carletz/DOMIX-Open-Source-Modular-Home-Automation-System/Images/3D Total 3.png

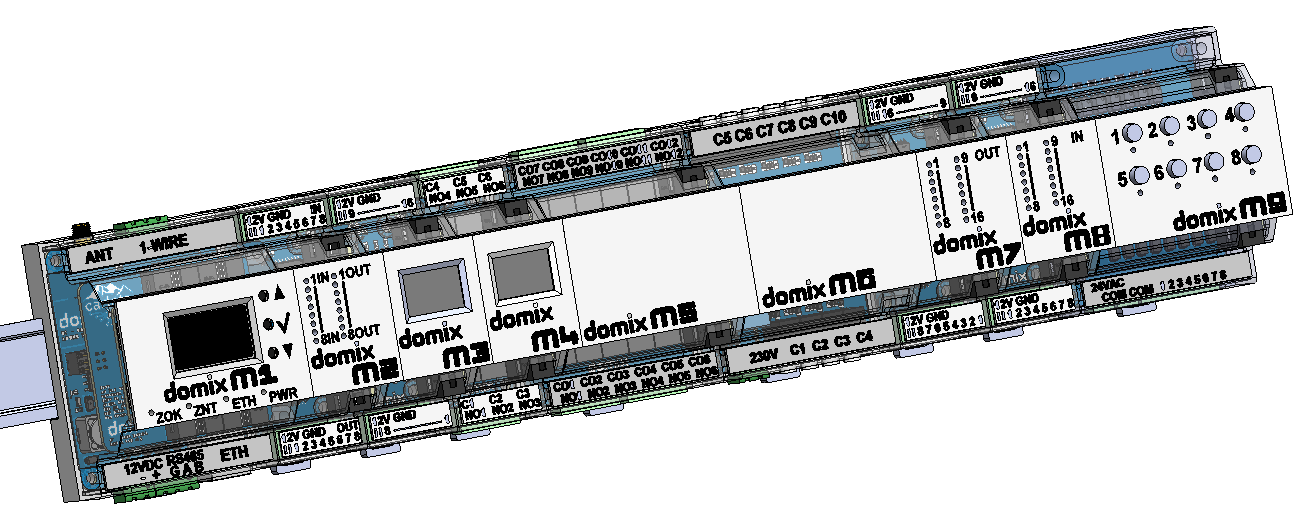
Images/3D Total 3.png
