carletz/DOMIX-Open-Source-Modular-Home-Automation-System/Images/8 module.png

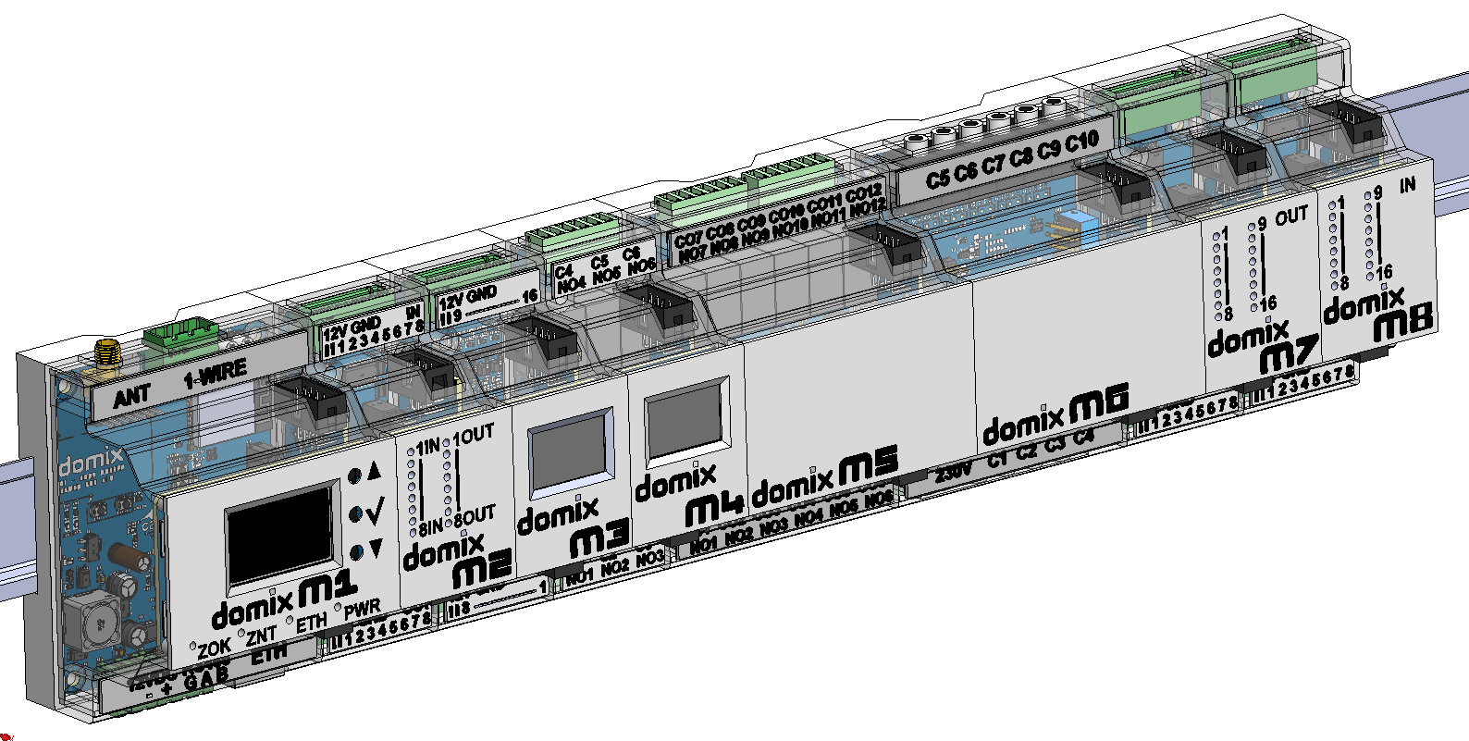
Images/8 module.png
