carletz/DOMIX-Open-Source-Modular-Home-Automation-System/Images/Board/domix total.png

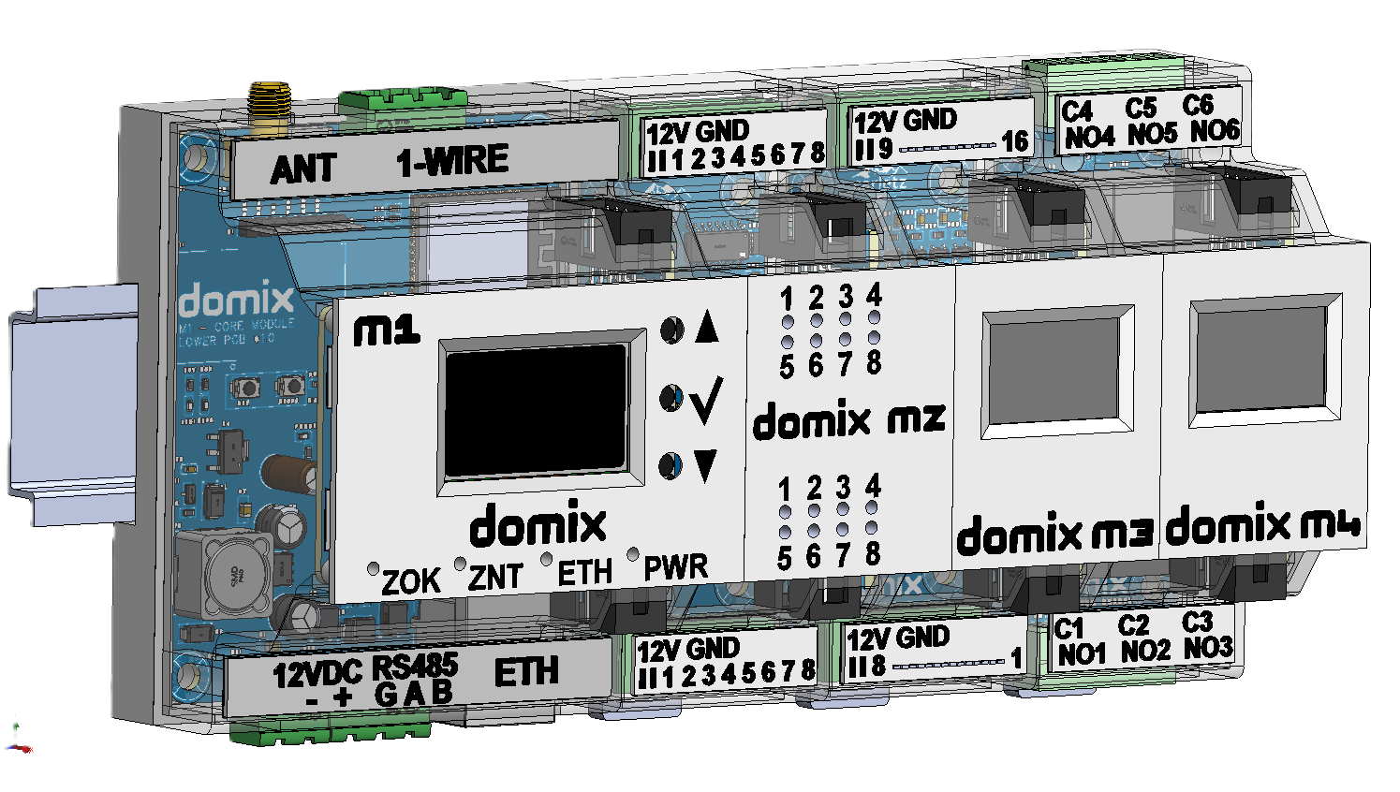
Images/Board/domix total.png
