carletz/DOMIX-Open-Source-Modular-Home-Automation-System/Images/Board/M1/M1 - 3D Board V0.1.png

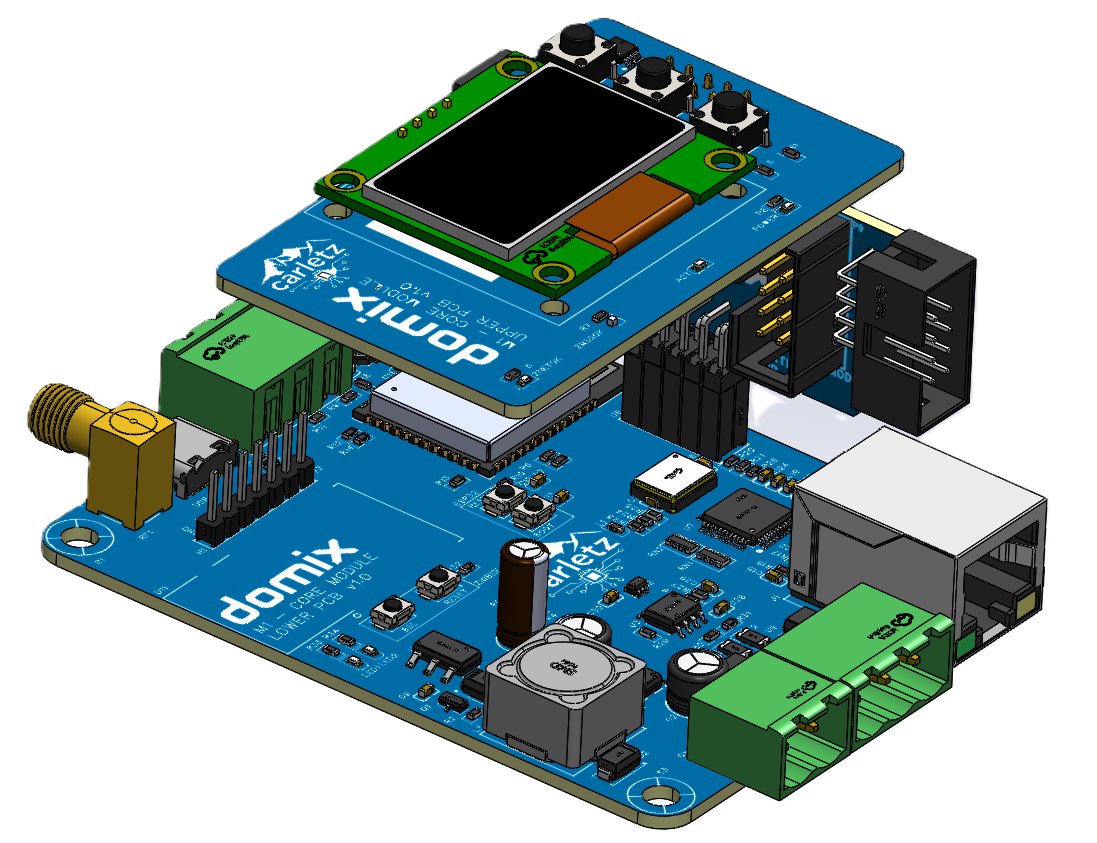
Images/Board/M1/M1 - 3D Board V0.1.png
