carletz/DOMIX-Open-Source-Modular-Home-Automation-System/Images/Board/M1/M1 - 3D Board V1.0.png

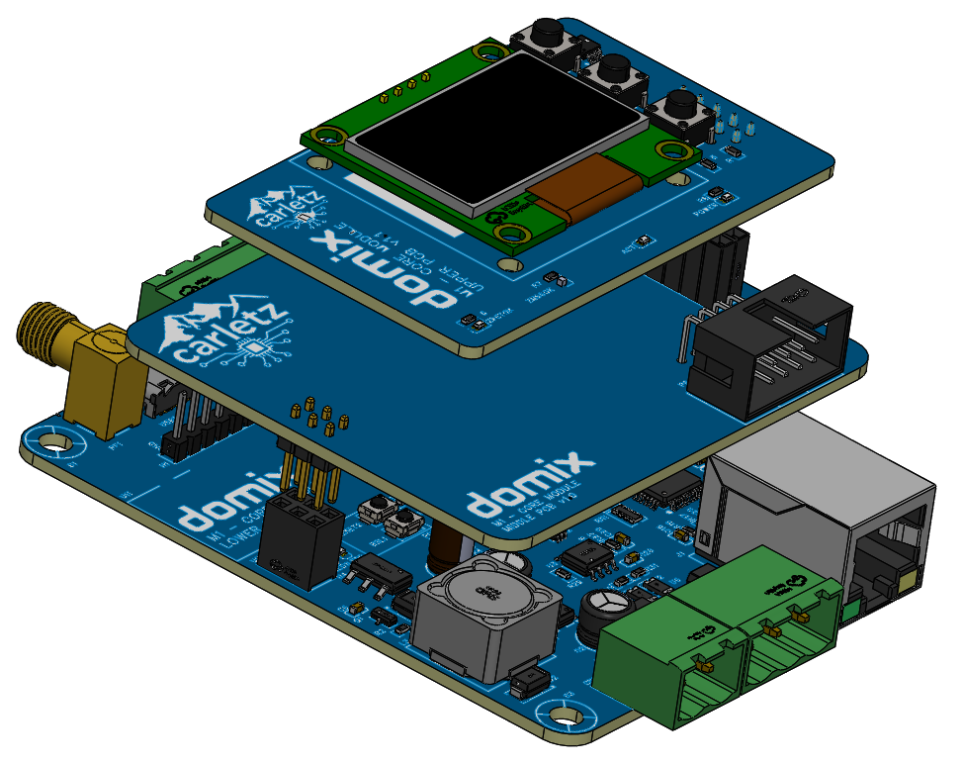
Images/Board/M1/M1 - 3D Board V1.0.png
