carletz/DOMIX-Open-Source-Modular-Home-Automation-System/Images/Board/M1/M1 - 3D Exploded.png

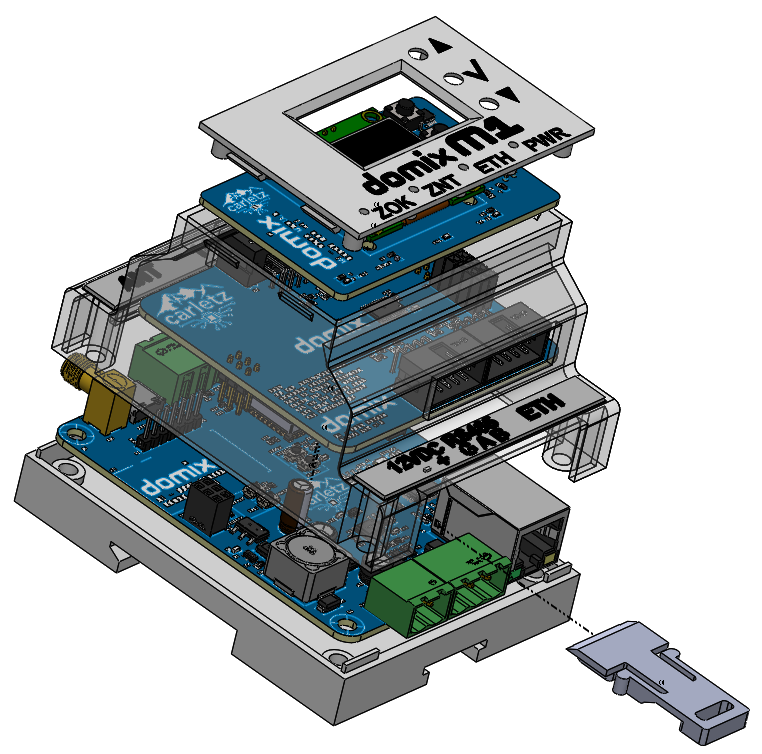
Images/Board/M1/M1 - 3D Exploded.png
