carletz/DOMIX-Open-Source-Modular-Home-Automation-System/Images/Board/M1/M1 - Lower.png

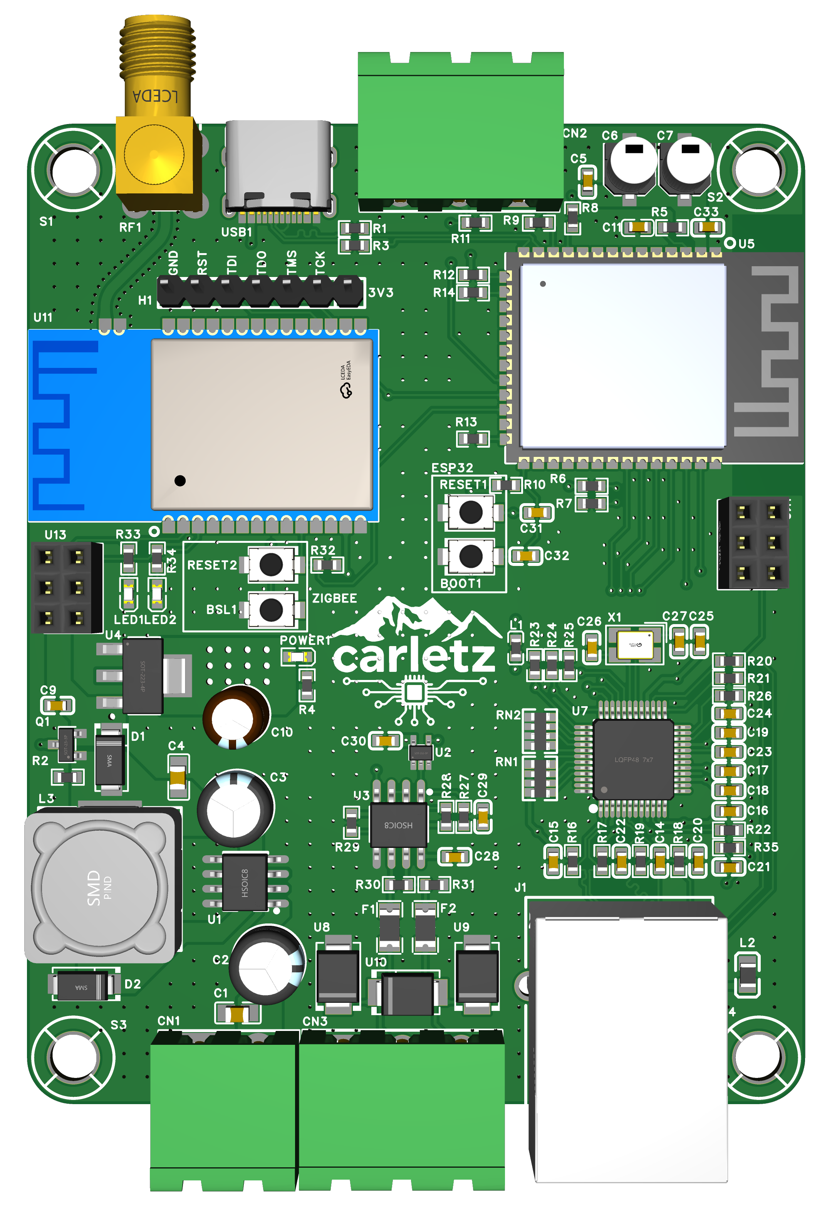
Images/Board/M1/M1 - Lower.png
