carletz/DOMIX-Open-Source-Modular-Home-Automation-System/Images/Board/M1/M1 - middle V1.0.png

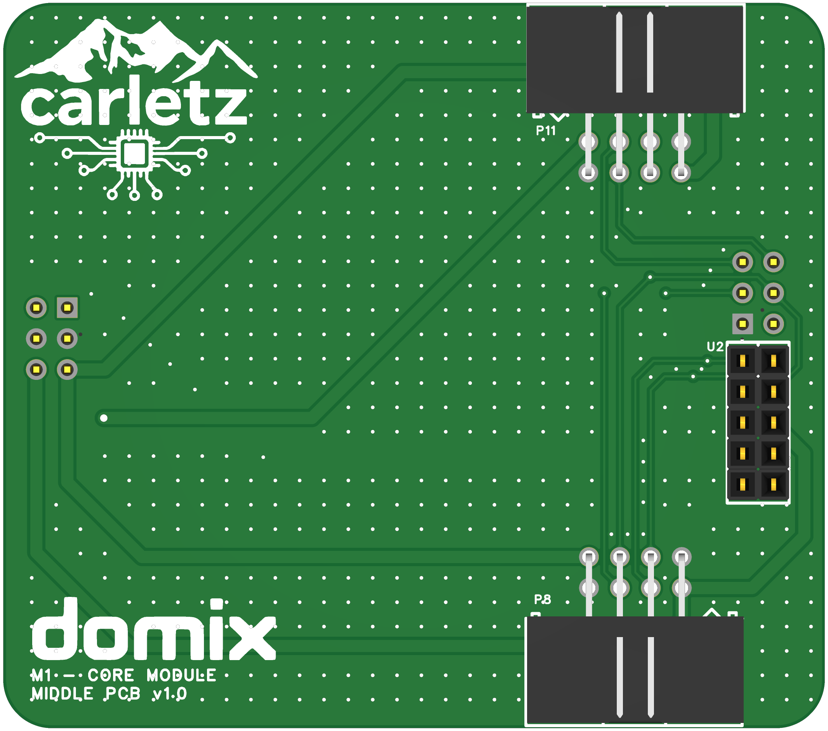
Images/Board/M1/M1 - middle V1.0.png
