carletz/DOMIX-Open-Source-Modular-Home-Automation-System/Images/Board/M1/M1 - Middle V1.1.png

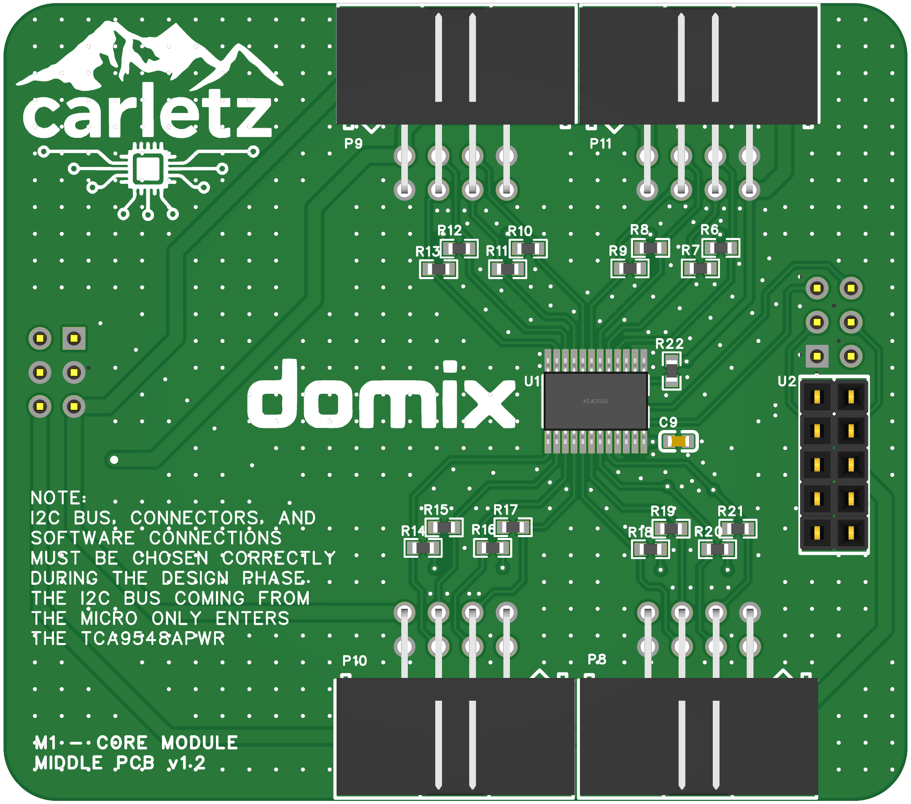
Images/Board/M1/M1 - Middle V1.1.png
