carletz/DOMIX-Open-Source-Modular-Home-Automation-System/Images/Board/M1/M1 - Upper.png

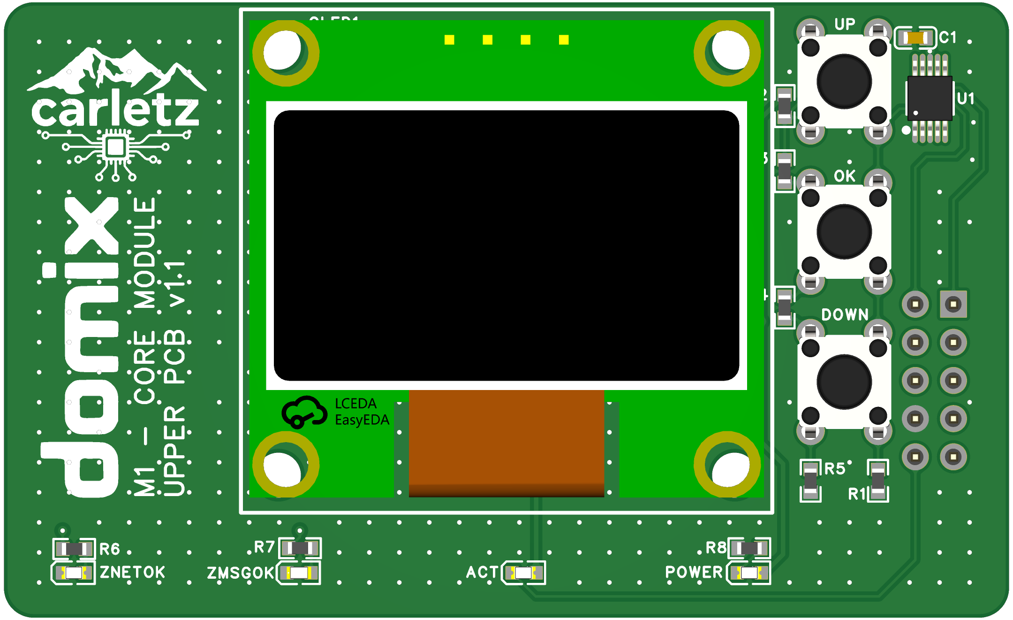
Images/Board/M1/M1 - Upper.png
