carletz/DOMIX-Open-Source-Modular-Home-Automation-System/Images/Board/M2/M2 - 3D Board.png

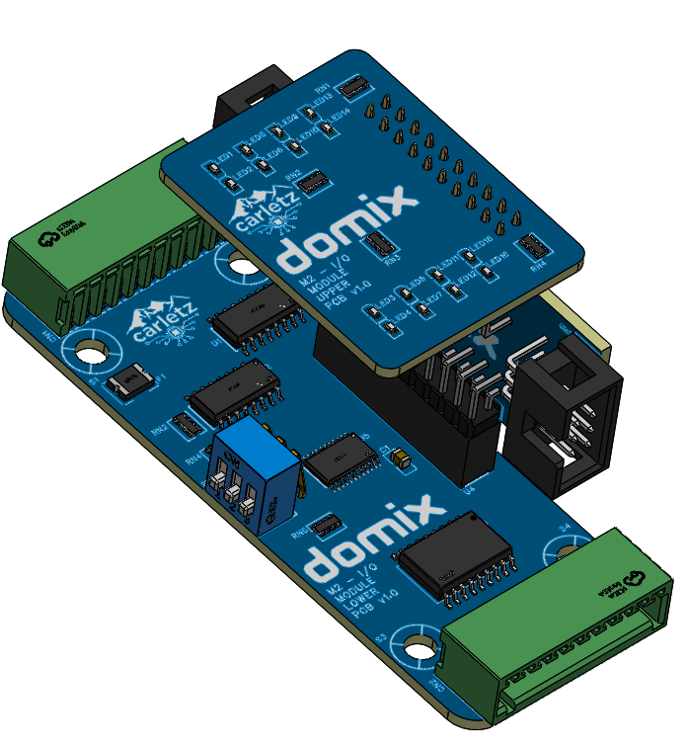
Images/Board/M2/M2 - 3D Board.png
