carletz/DOMIX-Open-Source-Modular-Home-Automation-System/Images/Board/M2/M2 - Lower.png

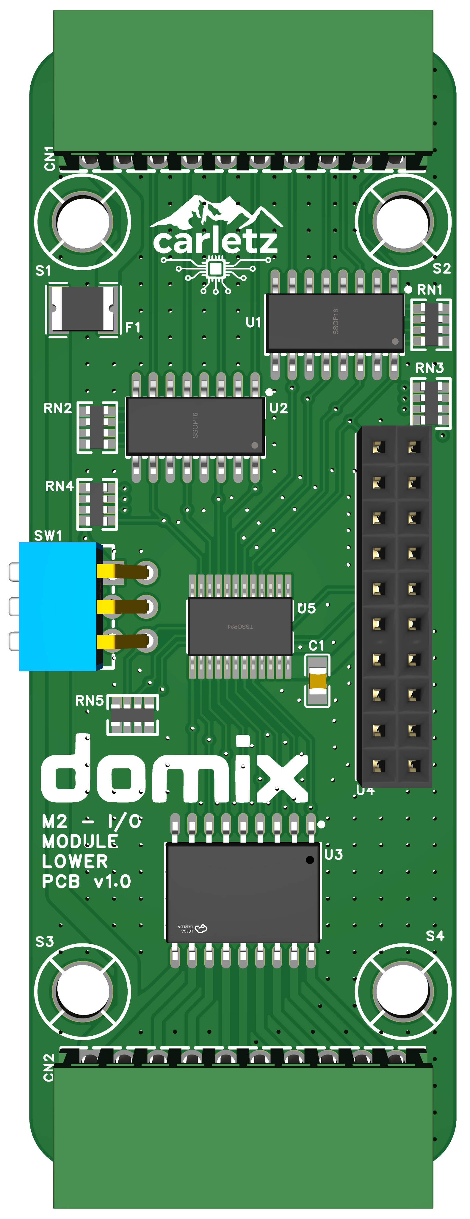
Images/Board/M2/M2 - Lower.png
