carletz/DOMIX-Open-Source-Modular-Home-Automation-System/Images/Board/M2/M2 - Pinout.png

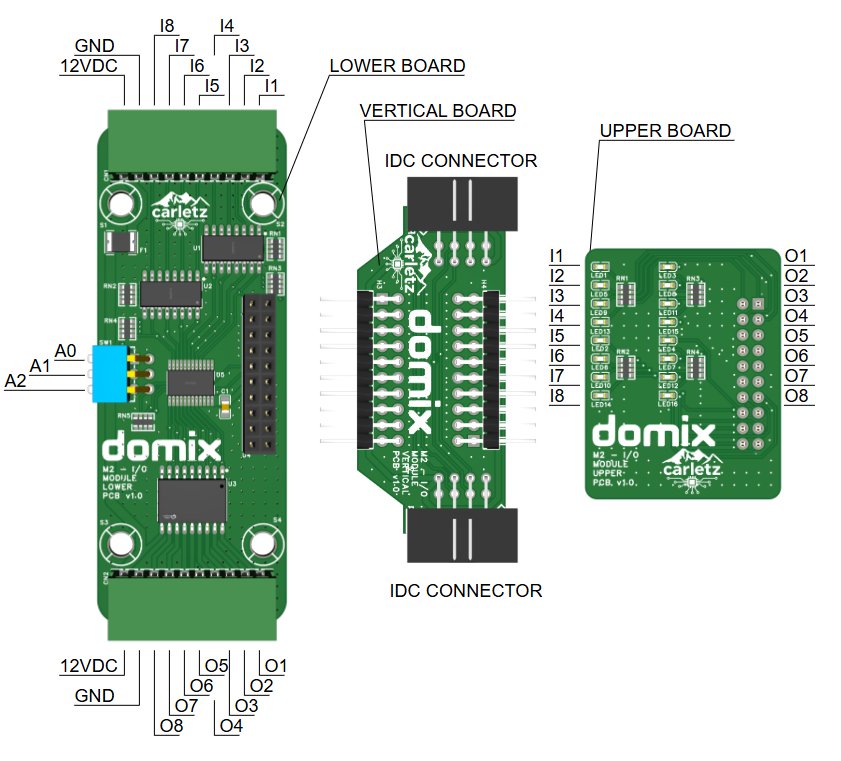
Images/Board/M2/M2 - Pinout.png
