carletz/DOMIX-Open-Source-Modular-Home-Automation-System/Images/Board/M3/M3 - 3D Board.png

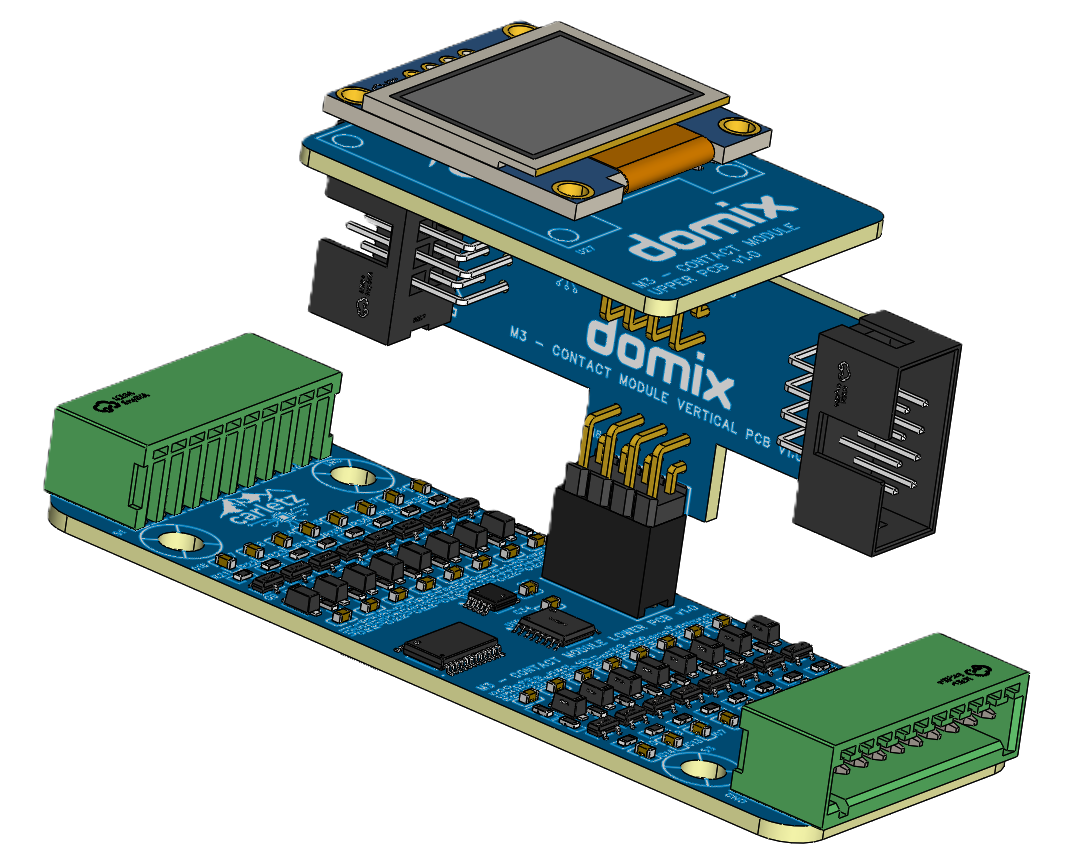
Images/Board/M3/M3 - 3D Board.png
