carletz/DOMIX-Open-Source-Modular-Home-Automation-System/Images/Board/M3/M3 - Lower.png

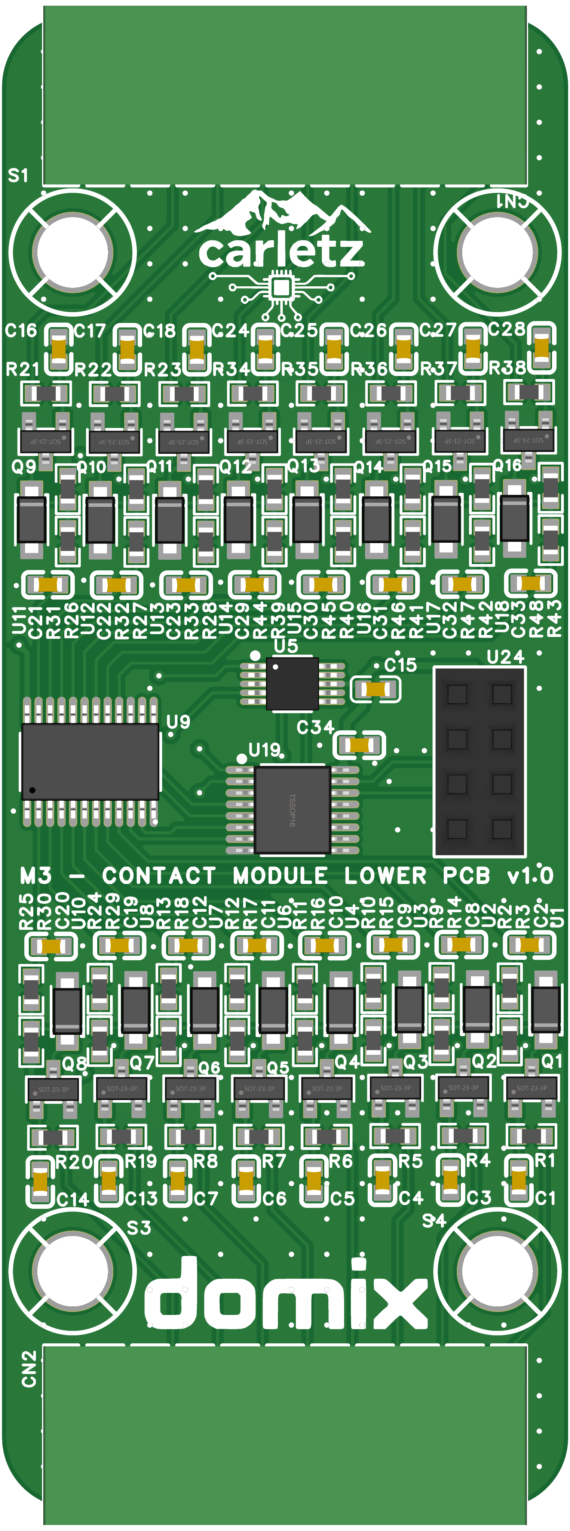
Images/Board/M3/M3 - Lower.png
