carletz/DOMIX-Open-Source-Modular-Home-Automation-System/Images/Board/M3/M3 - Upper.png

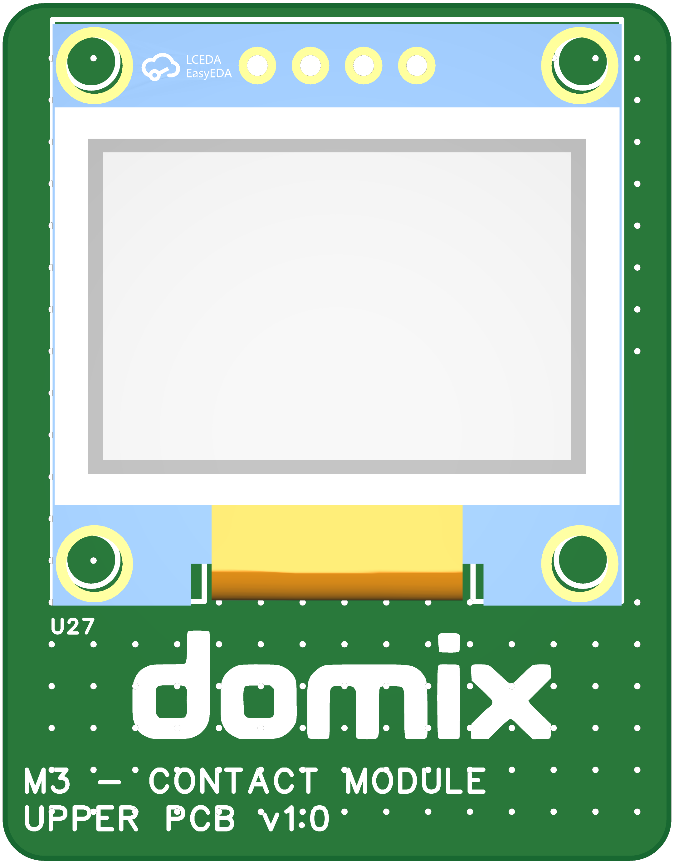
Images/Board/M3/M3 - Upper.png
