carletz/DOMIX-Open-Source-Modular-Home-Automation-System/Images/Board/M4/M4 - 3D Board.png

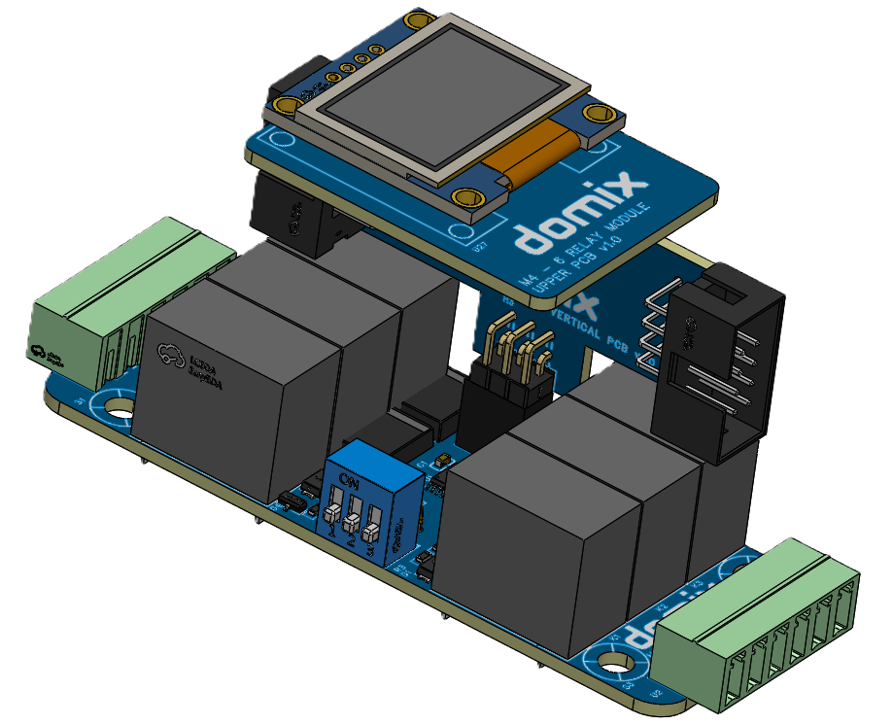
Images/Board/M4/M4 - 3D Board.png
