carletz/DOMIX-Open-Source-Modular-Home-Automation-System/Images/Board/M4/M4 - Pinout.png

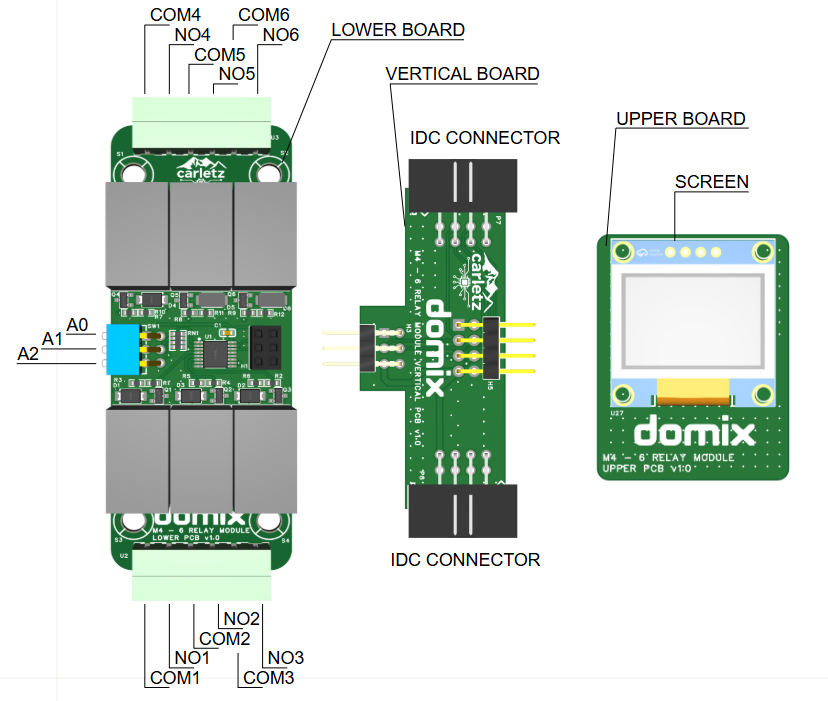
Images/Board/M4/M4 - Pinout.png
