carletz/DOMIX-Open-Source-Modular-Home-Automation-System/Images/Board/M5/M5 - Lower.png

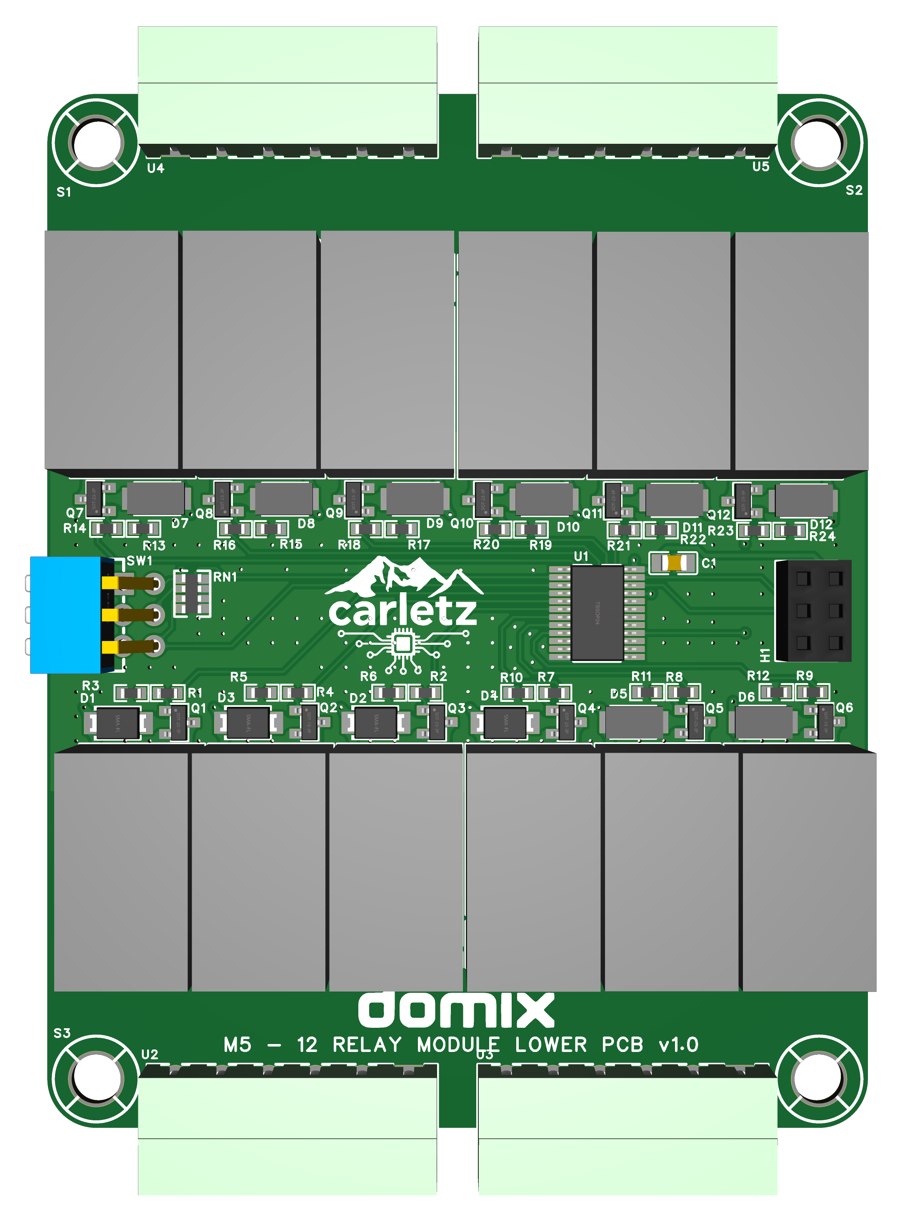
Images/Board/M5/M5 - Lower.png
