carletz/DOMIX-Open-Source-Modular-Home-Automation-System/Images/Board/M5/M5 - Pinout.png

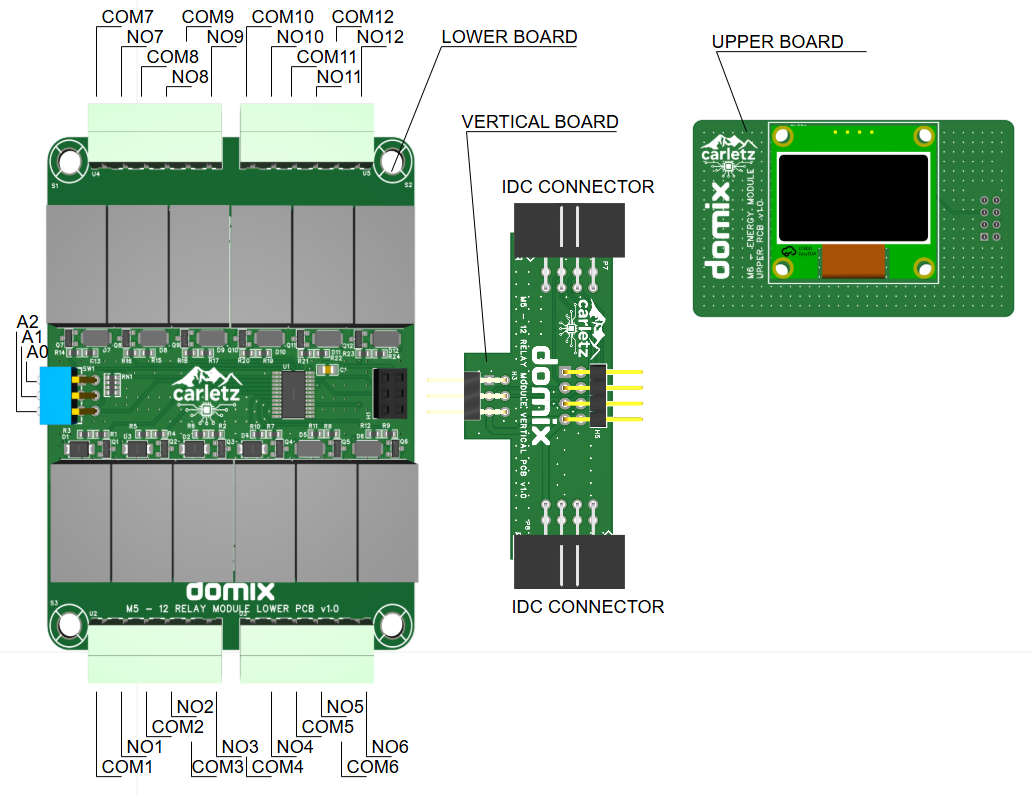
Images/Board/M5/M5 - Pinout.png
