carletz/DOMIX-Open-Source-Modular-Home-Automation-System/Images/Board/M5/M5-6 - Upper.png

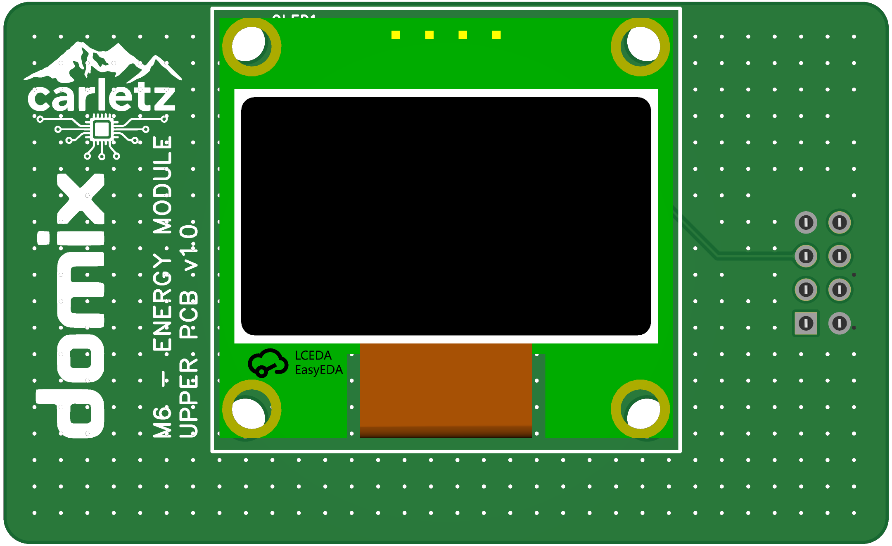
Images/Board/M5/M5-6 - Upper.png
