carletz/DOMIX-Open-Source-Modular-Home-Automation-System/Images/Board/M6/M6 - 3D Board.png

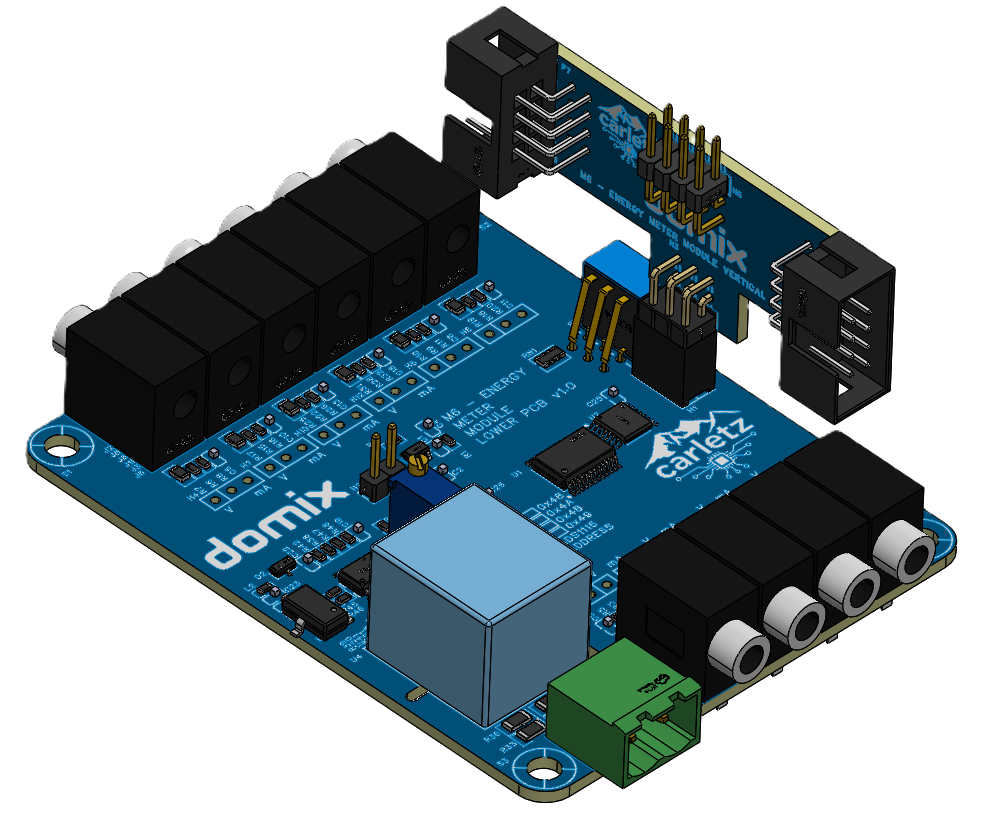
Images/Board/M6/M6 - 3D Board.png
