carletz/DOMIX-Open-Source-Modular-Home-Automation-System/Images/Board/M6/M6 - Lower.png

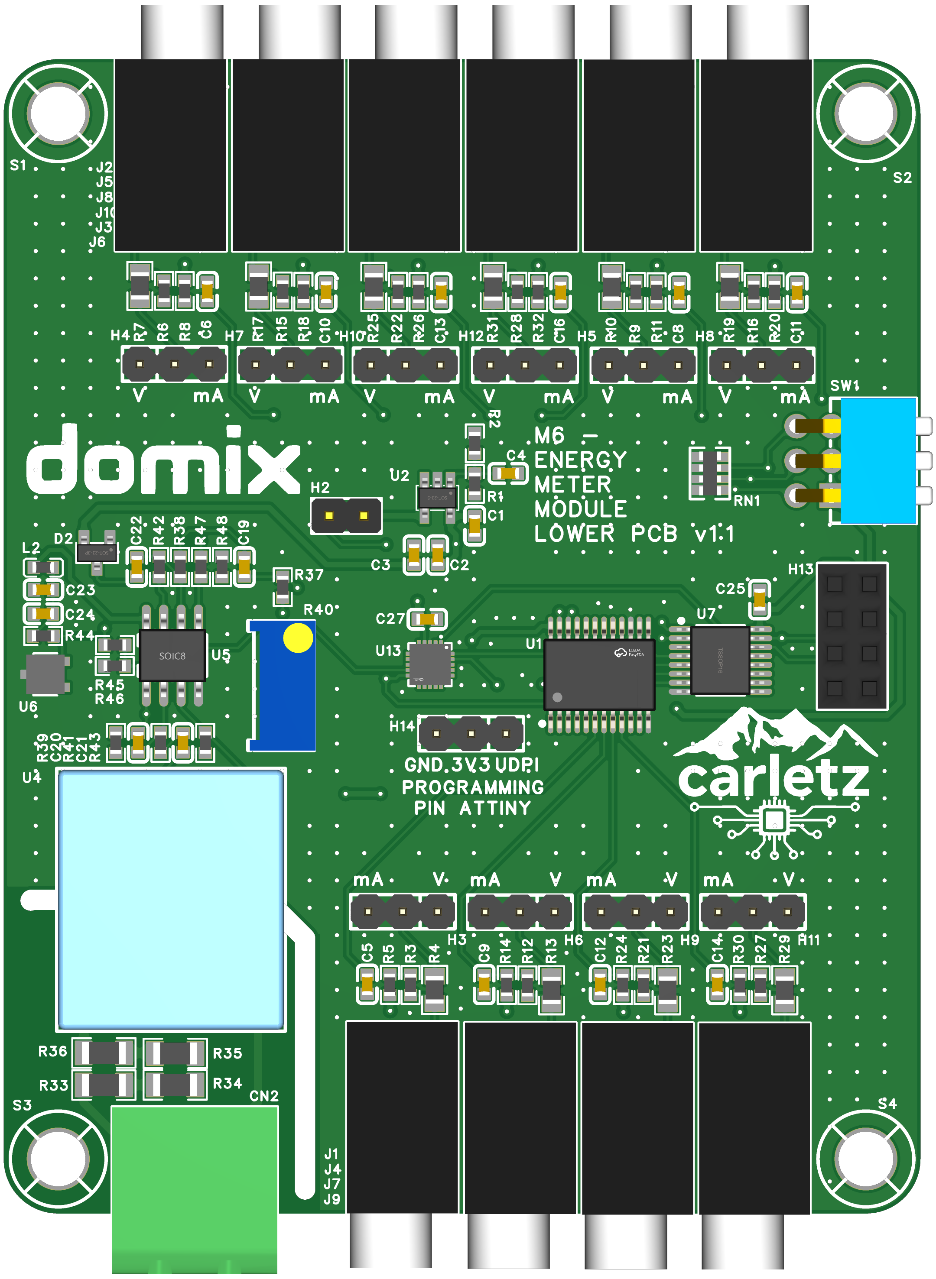
Images/Board/M6/M6 - Lower.png
