carletz/DOMIX-Open-Source-Modular-Home-Automation-System/Images/Board/M7/M7 - Upper.png

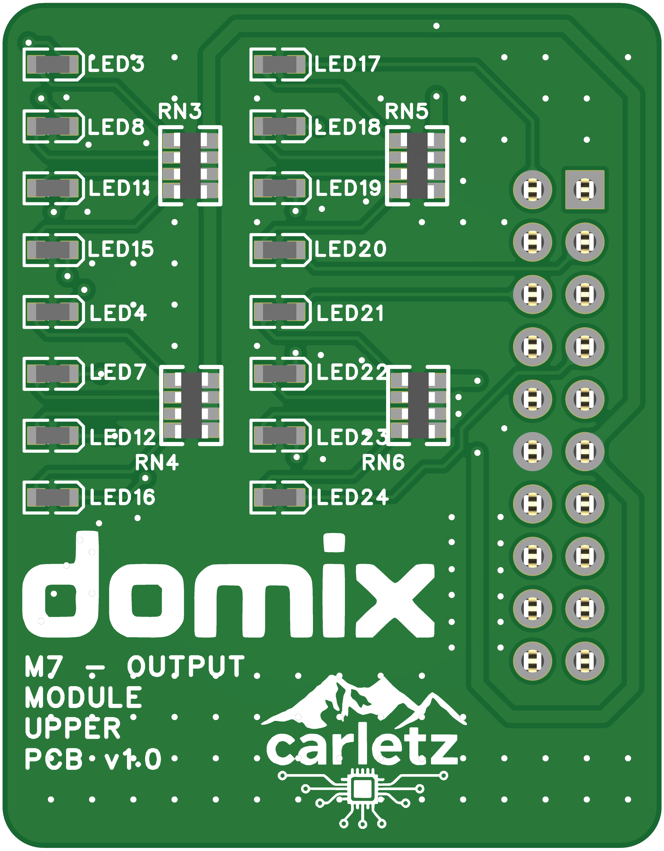
Images/Board/M7/M7 - Upper.png
