carletz/DOMIX-Open-Source-Modular-Home-Automation-System/Images/Board/M8/M8 - 3D Board.png

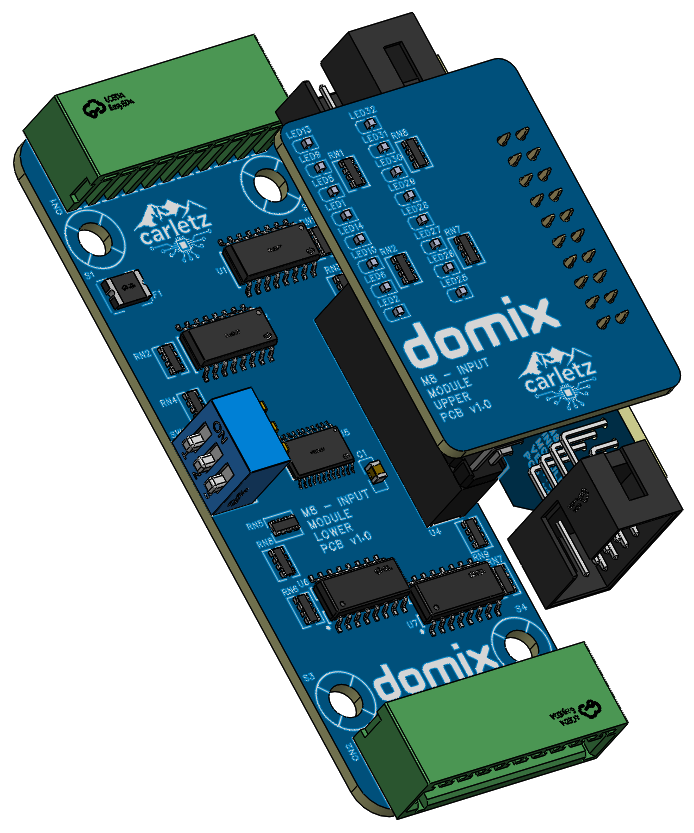
Images/Board/M8/M8 - 3D Board.png
