carletz/DOMIX-Open-Source-Modular-Home-Automation-System/Images/Board/M8/M8 - Lower.png

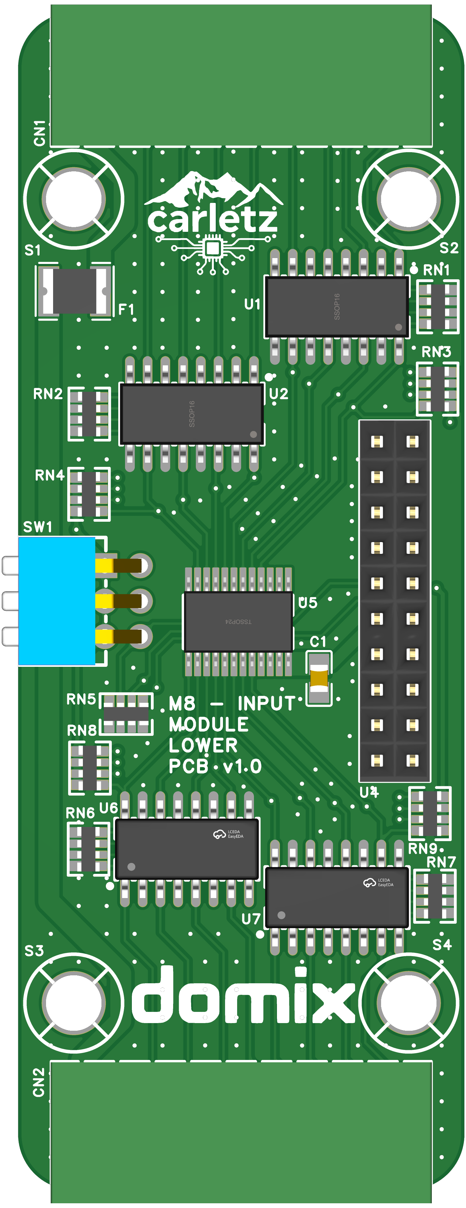
Images/Board/M8/M8 - Lower.png
