carletz/DOMIX-Open-Source-Modular-Home-Automation-System/Images/Board/M9/M9 - 3D Board.png

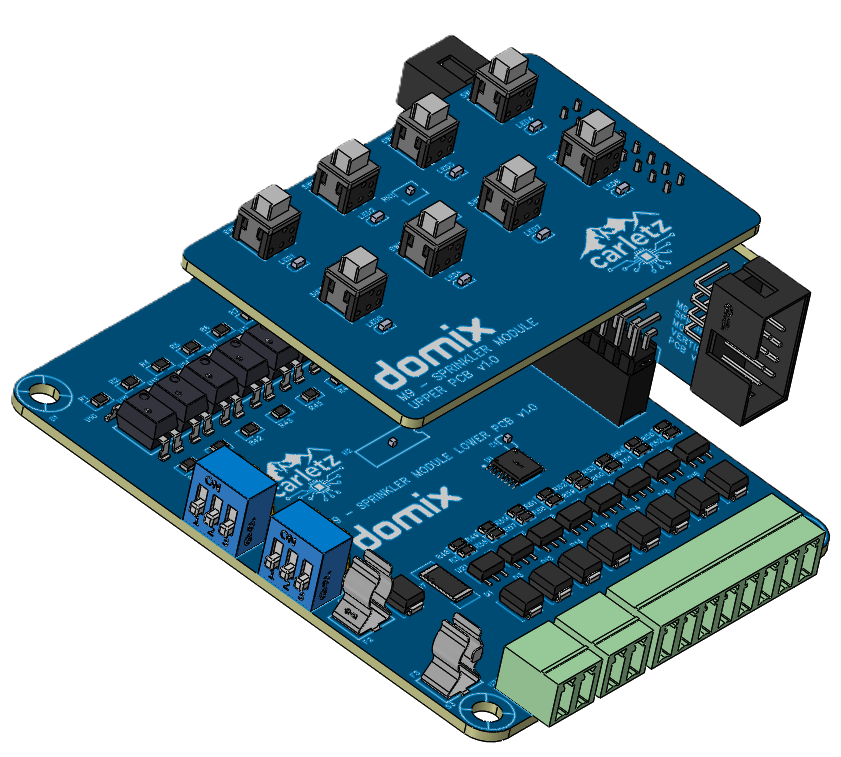
Images/Board/M9/M9 - 3D Board.png
