carletz/DOMIX-Open-Source-Modular-Home-Automation-System/Images/Board/M9/M9 - Upper.png

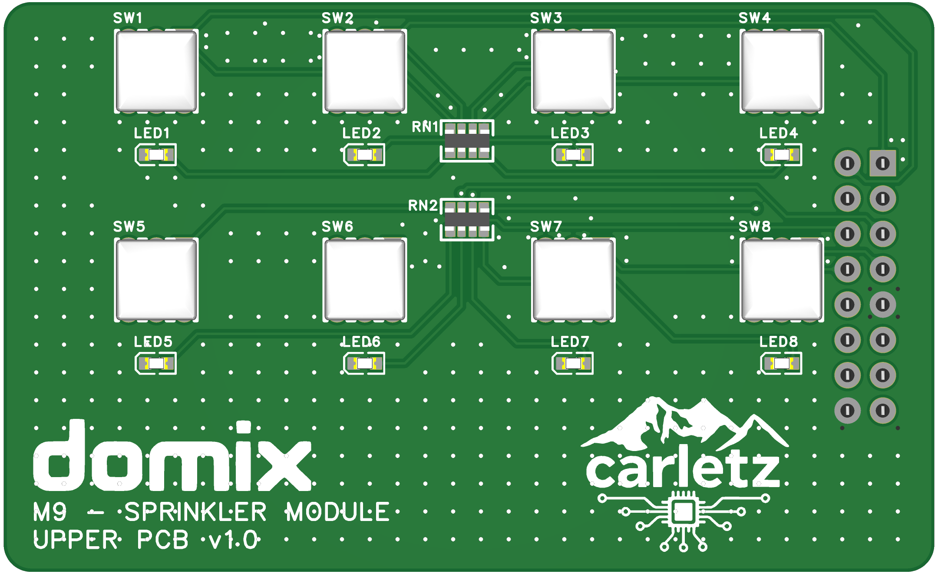
Images/Board/M9/M9 - Upper.png
