carletz/DOMIX-Open-Source-Modular-Home-Automation-System/Images/Board/S/S1 - 3D Explode.png

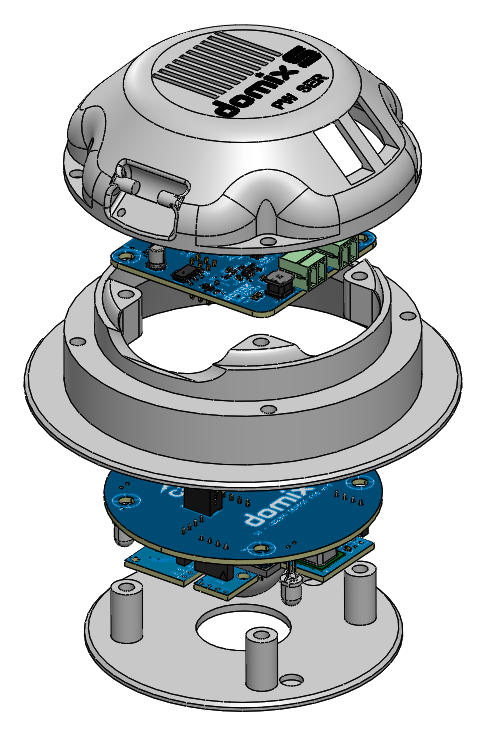
Images/Board/S/S1 - 3D Explode.png
