carletz/DOMIX-Open-Source-Modular-Home-Automation-System/Images/Board/S/S1b - 3D Module.png

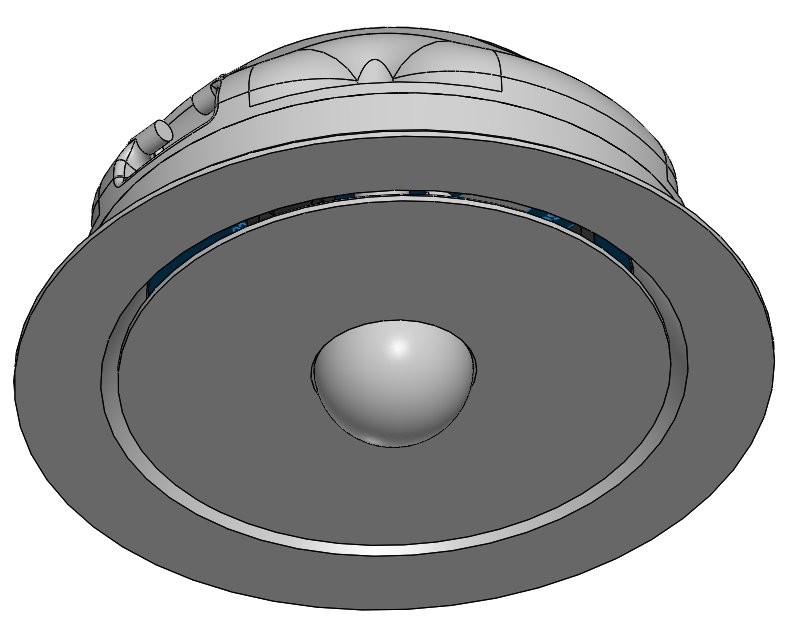
Images/Board/S/S1b - 3D Module.png
