carletz/DOMIX-Open-Source-Modular-Home-Automation-System/Images/Board/S/S1b - CEILING.png

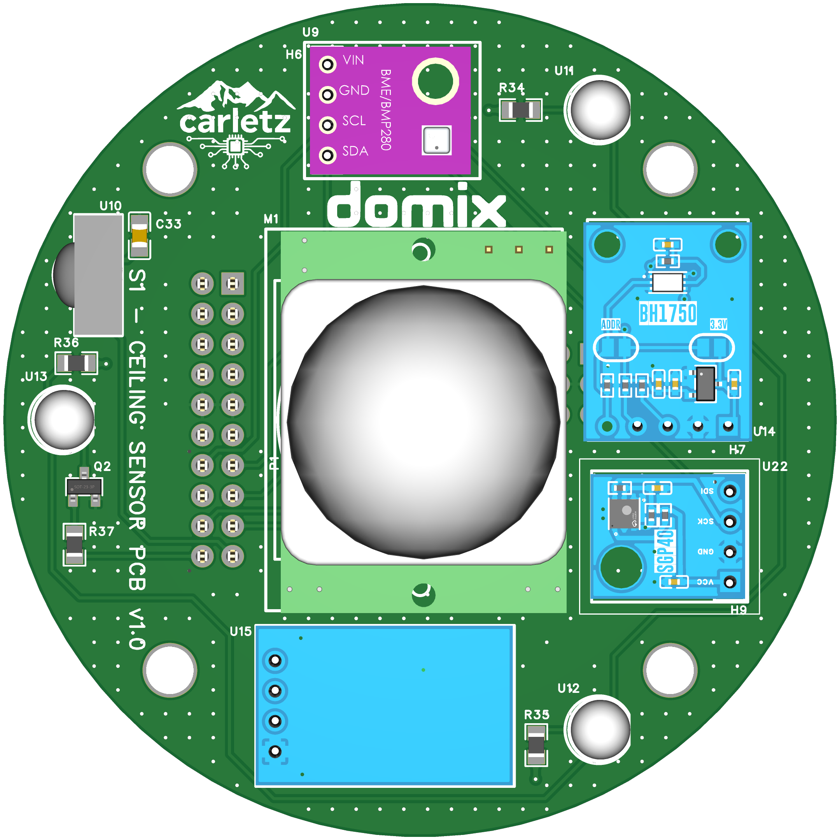
Images/Board/S/S1b - CEILING.png
