carletz/DOMIX-Open-Source-Modular-Home-Automation-System/Images/Board/S/S2a - 3D Module.png

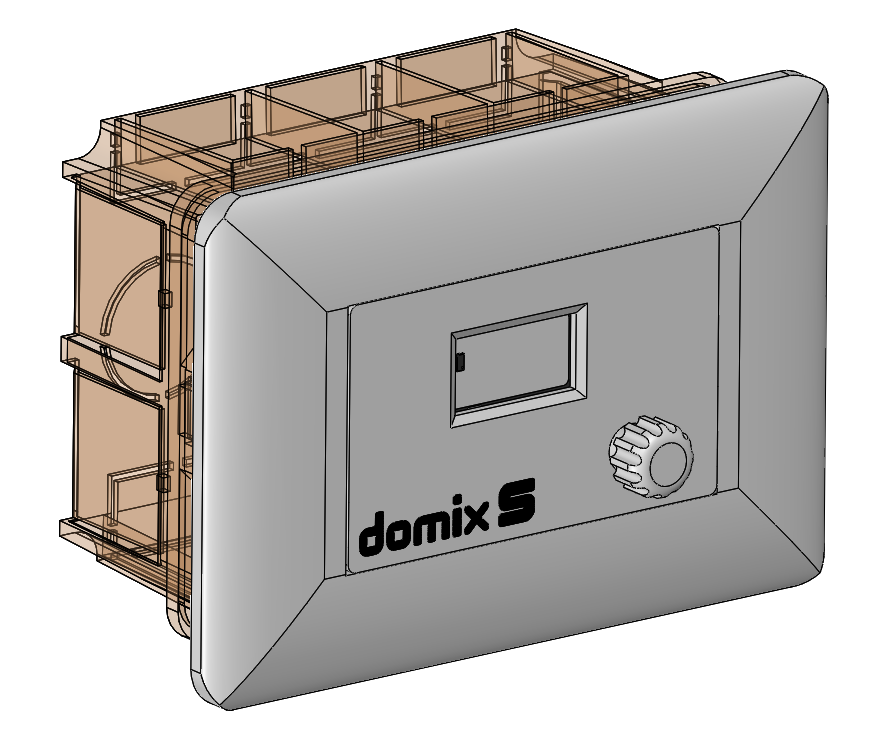
Images/Board/S/S2a - 3D Module.png
