carletz/DOMIX-Open-Source-Modular-Home-Automation-System/Images/Board/S/S2b - 3D Board.png

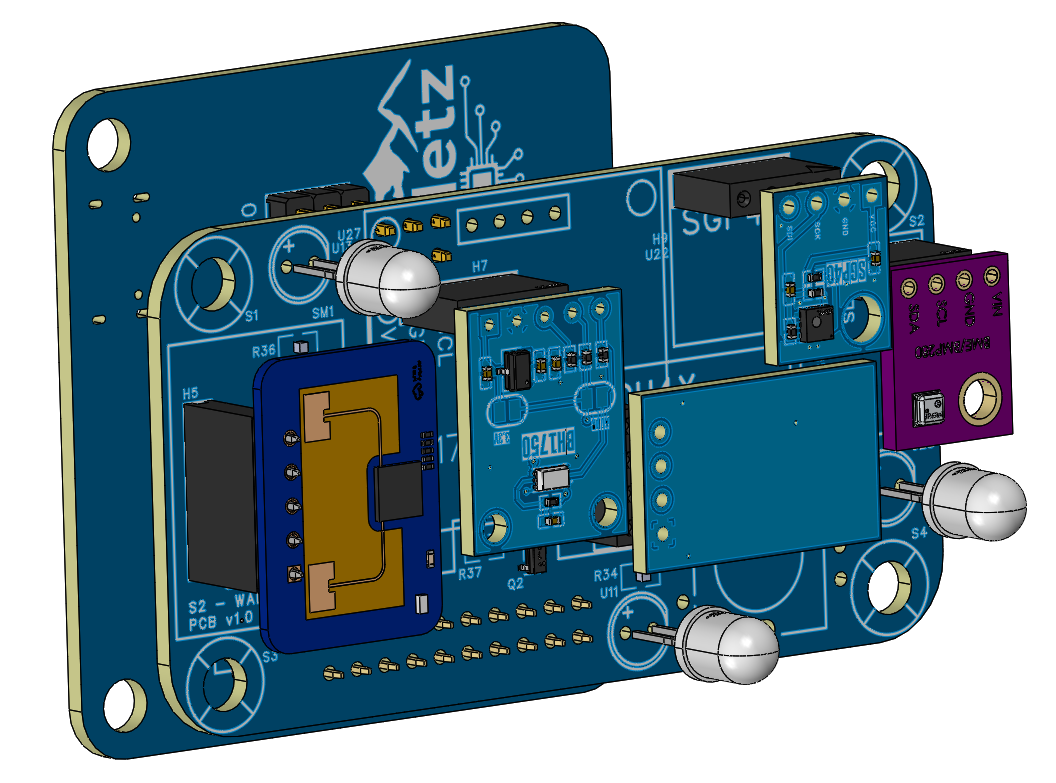
Images/Board/S/S2b - 3D Board.png
