carletz/DOMIX-Open-Source-Modular-Home-Automation-System/Images/Board/S/S2b - WALL.png

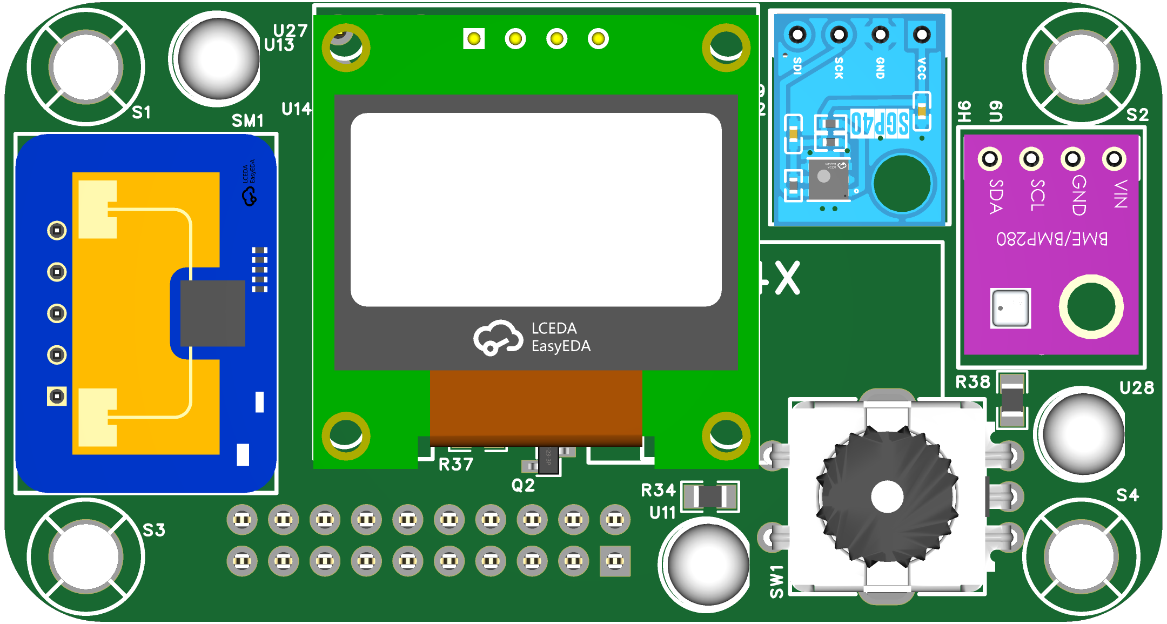
Images/Board/S/S2b - WALL.png
