carletz/DOMIX-Open-Source-Modular-Home-Automation-System/Images/Board/S/S - CORE SENSOR PCB.png

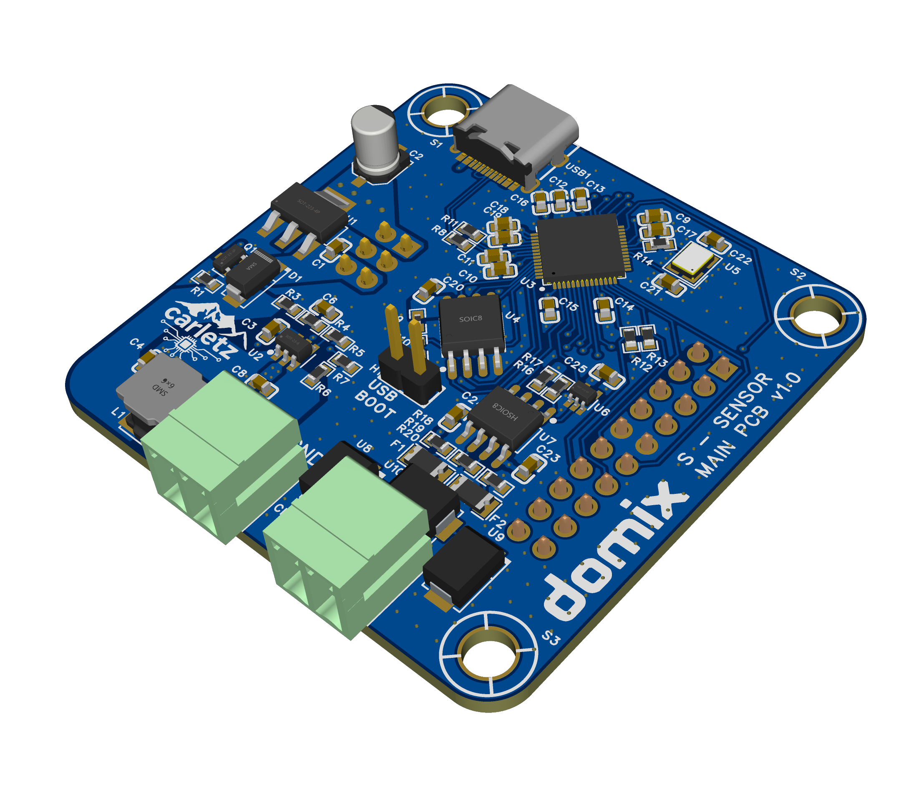
Images/Board/S/S - CORE SENSOR PCB.png
