carletz/DOMIX-Open-Source-Modular-Home-Automation-System/Images/Board/S/S - CORE SENSOR.png

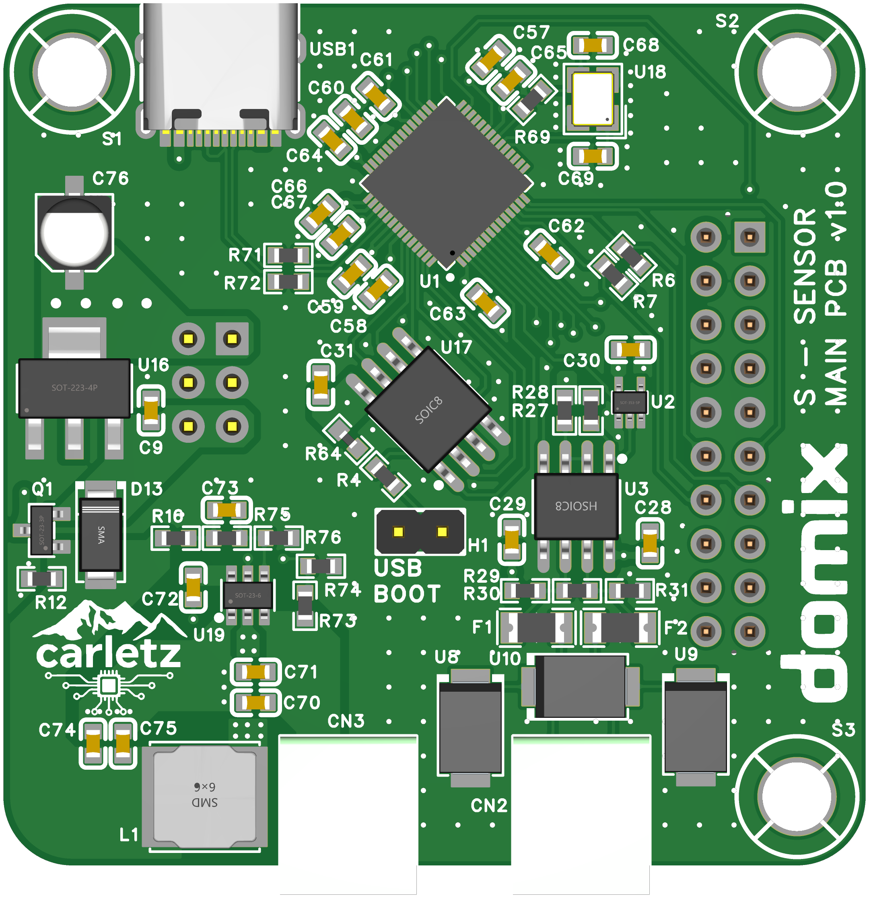
Images/Board/S/S - CORE SENSOR.png
