carletz/DOMIX-Open-Source-Modular-Home-Automation-System/Images/Board/S/S.png

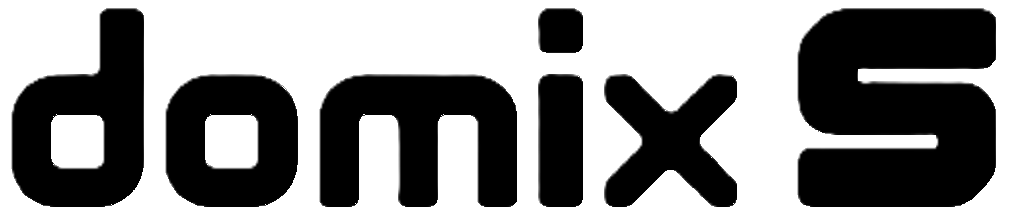
Images/Board/S/S.png
