carletz/DOMIX-Open-Source-Modular-Home-Automation-System/Images/IDC.png

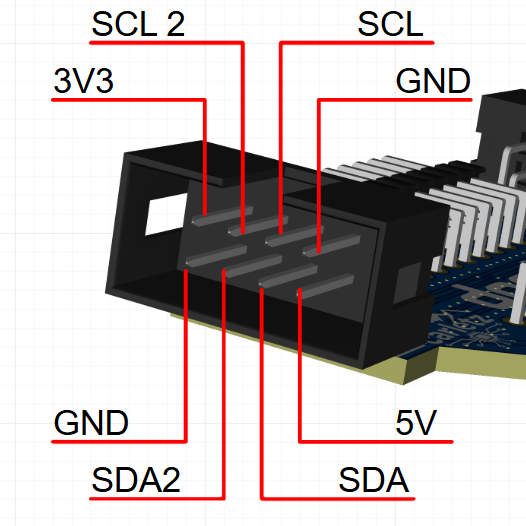
Images/IDC.png
