carletz/DOMIX-Open-Source-Modular-Home-Automation-System/BOM/BOM_M2 - I_O_M2 - I_O Module.xlsx

No. | Quantity | Comment | Designator | Footprint | Value | Manufacturer Part | Manufacturer | Supplier Part | Supplier | LCSC Stock | LCSC Price | Primary Category | Secondary Category | Pin Count | JLCPCB Stock | JLCPCB Price | 3D Model Title | Device | Name | Unique ID | Convert to PCB | Add into BOM | Symbol
1 | 1 | 100nF | C1 | C0805 | 100nF | 0805B104K500NT | FH(风华) | C38141 | LCSC |  |  | Capacitors | Multilayer Ceramic Capacitors MLCC - SMD/SMT | 2 | 3806470 | 0.0007 | C0805_L2.0-W1.3-H1.3 | 0805B104K500NT | 100nF | gge216_2 | yes | yes | 0805B104K500NT
2 | 2 | KF2EDGR-2.54-10P | CN1,CN2 | CONN-TH_10P-P2.54_KF2EDGR-2.54-10P |  | KF2EDGR-2.54-10P | KEFA(科发) | C577602 | LCSC |  |  | Connectors | Pluggable System Terminal Block | 10 | 1476 | 0.0757 | CONN-TH_10P-P2.54_KF2EDGR-2.54-10P | KF2EDGR-2.54-10P | KF2EDGR-2.54-10P | gge443,gge443_2 | yes | yes | KF2EDGR-2.54-10P
3 | 1 | JK-MSMD050-30 | F1 | F1812 |  | JK-MSMD050-30 | JK(金科) | C369168 | LCSC |  |  | Circuit Protection | Resettable Fuses | 2 | 127271 | 0.0051 | F1812_L4.5-W3.2-H1.0 | JK-MSMD050-30 | JK-MSMD050-30 | gge226 | yes | yes | JK-MSMD050-30
4 | 3 | 10kΩ | RN3,RN4,RN5 | RES-ARRAY-SMD_0603-8P-L3.2-W1.6-BL | 10kΩ | 4D03WGJ0103T5E | UNI-ROYAL(厚声) | C29718 | LCSC |  |  | Resistors | Resistor Networks, Arrays | 8 | 458521 | 0.0012 | R0603-8P_L3.2-W1.6-H0.6 | 4D03WGJ0103T5E | 10kΩ | gge210,gge210_1,gge225 | yes | yes | 4D03WGJ0103T5E
5 | 2 | 4.7kΩ | RN6,RN7 | RES-ARRAY-SMD_0603-8P-L3.2-W1.6-BL | 4.7kΩ | RC-ML08W472JT | FH(风华) | C172475 | LCSC |  |  | Resistors | Resistor Networks, Arrays | 8 | 12201 | 0.0012 | R0603-8P_L3.2-W1.6-H0.6 | RC-ML08W472JT | 4.7kΩ | gge445,gge446 | yes | yes | RC-ML08W472JT
6 | 1 | TM-03R | SW1 | SW-TH_TM-03R |  | TM-03R | Yuandi(元迪) | C882894 | LCSC |  |  | Switches | DIP Switches | 6 | 365 | 0.0642 | SW-TH_TM-03R | TM-03R | TM-03R | gge452_1 | yes | yes | TM-03R
7 | 2 | TLP290-4(GB-TP,E(T | U1,U2 | SOP-16_L10.3-W4.4-P1.27-LS7.0-BL |  | TLP290-4(GB-TP,E(T | TOSHIBA(东芝) | C39031 | LCSC |  |  | Optoisolators | Transistor, Photovoltaic Output Optoisolators | 16 | 19054 | 0.0783 | SOP-16_L10.3-W4.4-H2.0-LS7.0-P1.27 | TLP290-4(GB-TP,E(T | TLP290-4(GB-TP,E(T | gge219,gge219_1 | yes | yes | TLP290-4(GB-TP,E(T
8 | 1 | ULN2803A | U3 | SOP-18_L11.4-W7.6-P1.27-LS10.6-BL |  | ULN2803A | UMW(友台半导体) | C845537 | LCSC |  |  | Transistors/Thyristors | Darlington Transistor Arrays | 18 | 246001 | 0.0236 | SOP-18_L11.5-W7.5-H2.5-LS10.3-P1.27 | ULN2803A | ULN2803A | gge227_2 | yes | yes | ULN2803A_C845537
9 | 1 | ZX-PM2.54-2-10PY | U4 | HDR-TH_20P-P2.54-V-F-R2-C10-S2.54 |  | ZX-PM2.54-2-10PY | Megastar(兆星) | C7499346 | LCSC |  |  | Connectors | Female Headers | 20 | 8151 | 0.0264 | HDR-TH_20P-P2.54-F-LI-2X10P | ZX-PM2.54-2-10PY | ZX-PM2.54-2-10PY | gge444 | yes | yes | ZX-PM2.54-2-10PY
10 | 1 | PCA9535PW,118 | U5 | TSSOP-24_L7.8-W4.4-P0.65-LS6.4-BL |  | PCA9535PW,118 | NXP(恩智浦) | C255606 | LCSC |  |  | Interface | I/O Expanders | 24 | 2953 | 0.2662 | TSSOP-24_L7.8-W4.4-H1.0-LS6.4-P0.65 | PCA9535PW,118 | PCA9535PW,118 | gge234 | yes | yes | PCA9535PW,118
