carletz/DOMIX-Open-Source-Modular-Home-Automation-System/BOM/BOM_M9 - SPRINKLER_M9 - Sprinkler Module.xlsx

No. | Quantity | Comment | Designator | Footprint | Value | Manufacturer Part | Manufacturer | Supplier Part | Supplier | LCSC Stock | LCSC Price | Primary Category | Secondary Category | Pin Count | JLCPCB Stock | JLCPCB Price | 3D Model Title | Device | Name | Unique ID | Convert to PCB | Add into BOM | Symbol
1 | 1 | 100nF | C1 | C0603 | 100nF | CC0603KRX7R9BB104 | YAGEO(国巨) | C14663 | LCSC |  |  | Capacitors | Multilayer Ceramic Capacitors MLCC - SMD/SMT | 2 | 40399145 | 0.0004 | C0603_L1.6-W0.8-H0.8 | CC0603KRX7R9BB104 | 100nF | gge448_1 | yes | yes | CC0603KRX7R9BB104
2 | 9 | SMBJ43CA | D1,D2,D3,D4,D5,D13,D14,D15,D16 | SMB_L4.5-W3.6-LS5.3-BI |  | SMBJ43CA | GOODWORK(固得沃克) | C908858 | LCSC |  |  | TVS/Fuse/Board Level Protection | TVS | 2 | 5840 | 0.0058 | SMB_L4.5-W3.6-LS5.3-BI | SMBJ43CA_C908858 | SMBJ43CA | gge2,gge2_1,gge5,gge5_1,gge8,gge8_1,gge11,gge11_1,gge36 | yes | yes | SMBJ43CA_C908858
3 | 2 | 5x20 环保 保险管夹/座 | F2,F3 | FUSE-TH_5X20RHOSFUSECLIP-SEAT |  | 5x20 环保 保险管夹/座 | xcfuse(旭程) | C3130 | LCSC |  |  | TVS/Fuse/Board Level Protection | Fuse Holders | 1 | 448386 | 0.004 | FUSE-TH_5X20 | 5x20 环保 保险管夹/座 | 5x20 环保 保险管夹/座 | gge33,gge34 | yes | yes | 5x20 RHOS Fuse clip/seat
4 | 1 | 2.54-2*8P母 | J1 | HDR-TH_16P-P2.54-V-F-R2-C8-S2.54 |  | 2.54-2*8P母 | BOOMELE(博穆精密) | C30734 | LCSC |  |  | Connectors | Female Headers | 16 | 46451 | 0.0196 | HDR-TH_16P-P2.54-F-LI-2X8P | 2.54-2*8P母 | 2.54-2*8P母 | gge506 | yes | yes | Header-Female-2.54_2x8
5 | 8 | 1.33kΩ | R1,R2,R4,R5,R6,R7,R9,R11 | R0805 | 1.33kΩ | RC0805FR-071K33L | YAGEO(国巨) | C276298 | LCSC |  |  | Resistors | Chip Resistor - Surface Mount | 2 | 3057 | 0.0004 | R0805_L2.0-W1.3-H0.6 | RC0805FR-071K33L | 1.33kΩ | gge271,gge272,gge273,gge274,gge275,gge276,gge292,gge296 | yes | yes | RC0805FR-071K33L
6 | 8 | 10kΩ | R3,R56,R57,R58,R59,R60,R61,R62 | R0603 | 10kΩ | FRC0603F1002TS | FOJAN(富捷) | C2906982 | LCSC |  |  | Resistors | Chip Resistor - Surface Mount | 2 | 15261777 | 0.0002 | R0603 | FRC0603F1002TS | 10kΩ | gge422,gge422_1,gge422_2,gge422_3,gge422_4,gge422_5,gge422_6,gge422_7 | yes | yes | FRC0603F1002TS
7 | 8 | 1.43kΩ | R8,R10,R39,R40,R42,R43,R45,R46 | R0805 | 1.43kΩ | FRC0805F1431TS | FOJAN | C2933316 | LCSC |  |  | Resistors | Chip Resistor - Surface Mount | 2 | 11640 | 0.0004 | R0805_L2.0-W1.3-H0.6 | FRC0805F1431TS | 1.43kΩ | gge265,gge266,gge267,gge268,gge269,gge270,gge289,gge293 | yes | yes | FRC0805F1431TS
8 | 1 | 200mΩ | R47 | RES-SMD_L6.4-W3.2-R2512 | 200mΩ | HoYLR2512-3W-200mR-1% | Milliohm(毫欧) | C5375488 | LCSC |  |  | Resistors | Current Sense Resistors / Shunt Resistors | 2 | 30679 | 0.0083 | RES-SMD_L6.4-W3.2-R2512 | HoYLR2512-3W-200mR-1% | 200mΩ | gge494 | yes | yes | HOYLR2512-3W-200MR-1%
9 | 8 | 390Ω | R48,R49,R50,R51,R52,R53,R54,R55 | R0603 | 390Ω | 0603WAJ0391T5E | UNI-ROYAL(厚声) | C25235 | LCSC |  |  | Resistors | Chip Resistor - Surface Mount | 2 | 17094 | 0.0002 | R0603 | 0603WAJ0391T5E | 390Ω | gge495,gge496,gge497,gge498,gge499,gge500,gge501,gge502 | yes | yes | 0603WAJ0391T5E
10 | 2 | 10kΩ | RN1,RN2 | RES-ARRAY-SMD_0603-8P-L3.2-W1.6-BL | 10kΩ | 4D03WGJ0103T5E | UNI-ROYAL(厚声) | C29718 | LCSC |  |  | Resistors | Resistor Networks, Arrays | 8 | 458521 | 0.0012 | R0603-8P_L3.2-W1.6-H0.6 | 4D03WGJ0103T5E | 10kΩ | gge225,gge225_1 | yes | yes | 4D03WGJ0103T5E
11 | 9 | PCB-SGAP | SP1,SP2,SP3,SP4,SP5,SP6,SP7,SP8,SP9 | AIR-GAP |  |  |  |  |  | 25188300 | 0.0021 |  |  | 2 |  |  |  | PCB-SGAP | PCB-SGAP | gge3,gge3_1,gge6,gge6_1,gge9,gge9_1,gge12,gge12_1,gge37 | yes | yes | PCB-SGAP
12 | 2 | TM-03R | SW1,SW2 | SW-TH_TM-03R |  | TM-03R | Yuandi(元迪) | C882894 | LCSC |  |  | Switches | DIP Switches | 6 | 365 | 0.0642 | SW-TH_TM-03R | TM-03R | TM-03R | gge452,gge452_1 | yes | yes | TM-03R
13 | 1 | PCA9554APW,118 | U1 | TSSOP-16_L5.0-W4.4-P0.65-LS6.4-BL |  | PCA9554APW,118 | NXP(恩智浦) | C86803 | LCSC |  |  | Communication Interface Chip/UART/485/232 | I/O Expanders | 16 | 1902 | 0.1685 | TSSOP-16_L5.0-W4.4-H1.0-LS6.4-P0.65 | PCA9554APW,118 | PCA9554APW,118 | gge53_1 | yes | yes | PCA9554APW,118
14 | 1 | PCF8574M/TR | U2 | SOIC-16_L9.9-W3.9-P1.27-LS6.0-BL-1 |  | PCF8574M/TR | HGSEMI(华冠) | C5310792 | LCSC |  |  | Interface | I/O Expanders | 16 | 752 | 0.0799 | SOIC-16_L9.9-W3.9-H1.8-LS6.0-P1.27 | PCF8574M/TR | PCF8574M/TR | gge144_1 | yes | yes | PCF8574M/TR
15 | 8 | PC817AS | U3,U4,U5,U10,U12,U13,U14,U16 | SOP-4_L6.4-W4.6-P2.54-LS10.2-BL |  | PC817AS | AOTE(奥特) | C22375537 | LCSC |  |  | Optoisolators | Transistor, Photovoltaic Output Optoisolators | 4 | 17282 | 0.0066 | SOP-4_L6.5-W4.6-H4.5-P2.54-LS10.2-TL | PC817AS | PC817AS | gge147,gge152,gge156,gge160,gge164,gge168,gge168_1,gge168_2 | yes | yes | PC817AS
16 | 8 | MAC97A8 | U6,U9,U11,U15,U17,U18,U19,U21 | SOT-89-3_L4.5-W2.5-P1.50-LS4.2-BR |  | MAC97A8 | MSKSEMI(美森科) | C5140027 | LCSC |  |  | Triode/MOS Tube/Transistor | TRIACs | 3 | 271 | 0.0117 | SOT-89-3_L4.3-W2.5-H1.6-LS4.1-P1.50 | MAC97A8_1 | MAC97A8 | gge1,gge1_1,gge4,gge4_1,gge7,gge7_1,gge10,gge10_1 | yes | yes | MAC97A8_C5140027
17 | 1 | XD15EDGRC-3.81-8P-V | U22 | CONN-TH_8P-P3.81_XD15EDGRC-3.81-8P-V |  | XD15EDGRC-3.81-8P-V | XUNDA(讯答) | C22365798 | LCSC |  |  | Connectors | Pluggable System Terminal Block | 8 | 1635 | 0.0319 | CONN-TH_8P-P3.81_XD15EDGRC-3.81-8P-V | XD15EDGRC-3.81-8P-V | XD15EDGRC-3.81-8P-V | gge503 | yes | yes | XD15EDGRC-3.81-8P-V
18 | 2 | XD15EDGRC-3.81-2P-V | U23,U24 | CONN-TH_2P-P3.81_XD15EDGRC-3.81-2P-V |  | XD15EDGRC-3.81-2P-V | XUNDA(讯答) | C22365792 | LCSC |  |  | Connectors | Pluggable System Terminal Block | 2 | 1529 | 0.0075 | CONN-TH_2P-P3.81_XD15EDGRC-3.81-2P-V | XD15EDGRC-3.81-2P-V | XD15EDGRC-3.81-2P-V | gge504,gge505 | yes | yes | XD15EDGRC-3.81-2P-V
