carletz/DOMIX-Open-Source-Modular-Home-Automation-System/BOM/BOM_U1 - CORE - UPPER V1.1_M1 - Display Module V1.1.xlsx

No. | Quantity | Comment | Designator | Footprint | Value | Manufacturer Part | Manufacturer | Supplier Part | Supplier | LCSC Stock | LCSC Price | Primary Category | Secondary Category | Pin Count | JLCPCB Stock | JLCPCB Price | 3D Model Title | Device | Name | Unique ID | Convert to PCB | Add into BOM | Symbol
1 | 1 | 19-213/Y2C-CQ2R2L/3T(CY) | ACT1 | LED0603-RD-YELLOW |  | 19-213/Y2C-CQ2R2L/3T(CY) | EVERLIGHT(亿光) | C72038 | LCSC |  |  | Optoelectronics | LED Indication - Discrete | 2 | 1095857 | 0.0033 | LED0603-RD-YELLOW | 19-213/Y2C-CQ2R2L/3T(CY) | 19-213/Y2C-CQ2R2L/3T(CY) | gge439 | yes | yes | 19-213/Y2C-CQ2R2L/3T(CY)
2 | 1 | 1uF | C1 | C0603 | 1uF | CL10A105KA8NNNC | SAMSUNG(三星) | C5673 | LCSC |  |  | Capacitors | Multilayer Ceramic Capacitors MLCC - SMD/SMT | 2 | 207479 | 0.0009 | C0603_L1.6-W0.8-H0.8 | CL10A105KA8NNNC | 1uF | gge38_1 | yes | yes | CL10A105KA8NNNC
3 | 3 | KH-6X6X8H-TJ | DOWN1,OK1,UP1 | SW-TH_4P-L6.0-W6.0-P4.50-LS6.5 |  | KH-6X6X8H-TJ | kinghelm(金航标) | C2837518 | LCSC |  |  | Key/Switch | Tactile Switches | 4 | 10394 | 0.0023 | SW-TH_4P-L6.0-W6.0-H5.0-LS6.5-P4.50 | KH-6X6X8H-TJ | KH-6X6X8H-TJ | gge35_1,gge36_1,gge38 | yes | yes | KH-6X6X8H-TJ
4 | 1 | HDR-M_2.54_2x5 | H1 | HDR-TH_10P-P2.54-V-M-R2-C5-S2.54 |  |  |  |  |  |  | 0.0497 | Connectors | Pin Headers | 10 |  |  | HDR-TH_10P-P2.54-V-M-R2-C5-S2.54 | HDR-M_2.54_2x5 |  | gge440 | yes | yes | HDR-M-2.54_2x5
5 | 1 | HS13L03W2C01 | OLED1 | OLED-TH_L35.4-W33.5_HS13L03W2C01 |  | HS13L03W2C01 | HS(汉昇) | C7465997 | LCSC |  |  | Displays | OLED Display | 4 | 245 | 0.7645 | OLED-TH_L35.4-W33.5_HS13L03W2C01 | HS13L03W2C01 | HS13L03W2C01 | gge306 | yes | yes | HS13L03W2C01
6 | 1 | MHT192CRCT | POWER1 | LED0603-RD |  | MHT192CRCT | MEIHUA(美华) | C389517 | LCSC |  |  | Optoelectronics | LED Indication - Discrete | 2 | 102980 | 0.0033 | LED0603-RD | MHT192CRCT | MHT192CRCT | gge48 | yes | yes | MHT192CRCT
7 | 1 | 1MΩ | R1 | R0603 | 1MΩ | 0603WAF1004T5E | UNI-ROYAL(厚声) | C22935 | LCSC |  |  | Resistors | Chip Resistor - Surface Mount | 2 | 5022779 | 0.0002 | R0603 | 0603WAF1004T5E | 1MΩ | gge305 | yes | yes | 0603WAF1004T5E
8 | 7 | 1kΩ | R2,R3,R4,R5,R6,R7,R8 | R0603 | 1kΩ | RS-03K1001FT | FH(风华) | C115325 | LCSC |  |  | Resistors | Chip Resistor - Surface Mount | 2 | 4257181 | 0.0003 | R0603 | RS-03K1001FT | 1kΩ | gge46,gge46_1,gge46_2,gge46_3,gge46_4,gge46_5,gge46_6 | yes | yes | RS-03K1001FT
9 | 1 | ADS1115IDGSR | U1 | MSOP-10_L3.0-W3.0-P0.50-LS5.0-BL |  | ADS1115IDGSR | TI(德州仪器) | C37593 | LCSC |  |  | Data Acquisition | Analog to Digital Converters (ADC) | 10 | 1504 | 0.1424 | MSOP-10_L3.0-W3.0-H1.1-LS5.0-P0.50 | ADS1115IDGSR | ADS1115IDGSR | gge190 | yes | yes | ADS1115IDGSR
10 | 1 | MHT193CGCT | ZMSGOK1 | LED0603-RD_GREEN |  | MHT193CGCT | MEIHUA(美华) | C2962098 | LCSC |  |  | Optoelectronics | LED Indication - Discrete | 2 | 2139 | 0.0061 | LED0603-RD_GREEN | MHT193CGCT | MHT193CGCT | gge438 | yes | yes | MHT193CGCT
11 | 1 | MHT192UBCT | ZNETOK1 | LED0603-RD |  | MHT192UBCT | MEIHUA(美华) | C389520 | LCSC |  |  | Optoelectronics | LED Indication - Discrete | 2 | 46146 | 0.0037 | LED0603-RD | MHT192UBCT | MHT192UBCT | gge437 | yes | yes | MHT192UBCT
