carletz/DOMIX-Open-Source-Modular-Home-Automation-System/BOM/BOM_U2 - I_O - UPPER_M2 - Display Module.xlsx

No. | Quantity | Comment | Designator | Footprint | Value | Manufacturer Part | Manufacturer | Supplier Part | Supplier | LCSC Stock | LCSC Price | Primary Category | Secondary Category | Pin Count | JLCPCB Stock | JLCPCB Price | 3D Model Title | Device | Name | Unique ID | Convert to PCB | Add into BOM | Symbol
1 | 16 | MHT192CRCT | LED1,LED2,LED3,LED4,LED5,LED6,LED7,LED8,LED9,LED10,LED11,LED12,LED13,LED14,LED15,LED16 | LED0603-RD |  | MHT192CRCT | MEIHUA(美华) | C389517 | LCSC |  |  | Optoelectronics | LED Indication - Discrete | 2 | 102980 | 0.0033 | LED0603-RD | MHT192CRCT | MHT192CRCT | gge237_1,gge238_1,gge239_1,gge240_1,gge243_1,gge244_1,gge245_1,gge246_1,gge247_1,gge248_1,gge249_1,gge251_1,gge252_1,gge253_1,gge255_1,gge256_1 | yes | yes | MHT192CRCT
2 | 2 | 270Ω | RN1,RN2 | RES-ARRAY-SMD_0603-8P-L3.2-W1.6-BL | 270Ω | 4D03WGJ0271T5E | UNI-ROYAL(厚声) | C425067 | LCSC |  |  | Resistors | Resistor Networks, Arrays | 8 | 4137 | 0.0009 | R0603-8P_L3.2-W1.6-H0.6 | 4D03WGJ0271T5E | 270Ω | gge241_1,gge242_1 | yes | yes | 4D03WGJ0271T5E
3 | 2 | 680Ω | RN3,RN4 | RES-ARRAY-SMD_0603-8P-L3.2-W1.6-BL | 680Ω | 4D03WGJ0681T5E | UNI-ROYAL(厚声) | C12035 | LCSC |  |  | Resistors | Resistor Networks, Arrays | 8 | 17292 | 0.001 | R0603-8P_L3.2-W1.6-H0.6 | 4D03WGJ0681T5E | 680Ω | gge250_1,gge254_1 | yes | yes | 4D03WGJ0681T5E
4 | 1 | ZX-PM2.54-2-10PY | U1 | HDR-TH_20P-P2.54-V-F-R2-C10-S2.54 |  | ZX-PM2.54-2-10PY | Megastar(兆星) | C7499346 | LCSC |  |  | Connectors | Female Headers | 20 | 8151 | 0.0264 | HDR-TH_20P-P2.54-F-LI-2X10P | ZX-PM2.54-2-10PY | ZX-PM2.54-2-10PY | gge1 | yes | yes | ZX-PM2.54-2-10PY
