carletz/DOMIX-Open-Source-Modular-Home-Automation-System/BOM/BOM_U3-4 - MULTI - UPPER_M3-4 - Display Module.xlsx

No. | Quantity | Comment | Designator | Footprint | Value | Manufacturer Part | Manufacturer | Supplier Part | Supplier | LCSC Stock | LCSC Price | Primary Category | Secondary Category | Pin Count | JLCPCB Stock | JLCPCB Price | 3D Model Title | Device | Name | Unique ID | Convert to PCB | Add into BOM | Symbol
1 | 1 | 2.54-2*4 | U24 | HDR-TH_8P-P2.54-V-F-R2-C4-S2.54 |  | 2.54-2*4 | ZHOURI(洲日) | C2977588 | LCSC |  |  | Connectors | Female Headers | 8 | 17462 | 0.015 | HDR-TH_8P-P2.54-F-LI-2X4P | 2.54-2*4 | 2.54-2*4 | gge493 | yes | yes | 2.54-2*4
2 | 1 | HS96L03W2C03 | U27 | OLED-TH_L27.8-W27.2-P2.54_C9900033791 |  | HS96L03W2C03 | HS(汉昇) | C5248080 | LCSC |  |  | Displays | OLED Display | 4 | 11677 | 0.3192 | OLED-TH_L27.8-W27.2-P2.54_C9900033791 | HS96L03W2C03 | HS96L03W2C03 | gge304 | yes | yes | HS96L03W2C03
