carletz/DOMIX-Open-Source-Modular-Home-Automation-System/BOM/BOM_U8 - INPUT - UPPER_M8 - Display Module.xlsx

No. | Quantity | Comment | Designator | Footprint | Value | Manufacturer Part | Manufacturer | Supplier Part | Supplier | LCSC Stock | LCSC Price | Primary Category | Secondary Category | Pin Count | JLCPCB Stock | JLCPCB Price | 3D Model Title | Device | Name | Unique ID | Convert to PCB | Add into BOM | Symbol
1 | 16 | MHT192CRCT | LED1,LED2,LED5,LED6,LED9,LED10,LED13,LED14,LED25,LED26,LED27,LED28,LED29,LED30,LED31,LED32 | LED0603-RD |  | MHT192CRCT | MEIHUA(美华) | C389517 | LCSC |  |  | Optoelectronics | LED Indication - Discrete | 2 | 102980 | 0.0033 | LED0603-RD | MHT192CRCT | MHT192CRCT | gge237_1,gge237_2,gge238_1,gge238_2,gge239_1,gge239_2,gge240_1,gge240_2,gge243_1,gge243_2,gge244_1,gge244_2,gge245_1,gge245_2,gge246_1,gge246_2 | yes | yes | MHT192CRCT
2 | 4 | 270Ω | RN1,RN2,RN7,RN8 | RES-ARRAY-SMD_0603-8P-L3.2-W1.6-BL | 270Ω | 4D03WGJ0271T5E | UNI-ROYAL(厚声) | C425067 | LCSC |  |  | Resistors | Resistor Networks, Arrays | 8 | 4137 | 0.0009 | R0603-8P_L3.2-W1.6-H0.6 | 4D03WGJ0271T5E | 270Ω | gge241_1,gge241_2,gge242_1,gge242_2 | yes | yes | 4D03WGJ0271T5E
3 | 1 | ZX-PM2.54-2-10PY | U4 | HDR-TH_20P-P2.54-V-F-R2-C10-S2.54 |  | ZX-PM2.54-2-10PY | Megastar(兆星) | C7499346 | LCSC |  |  | Connectors | Female Headers | 20 | 8151 | 0.0264 | HDR-TH_20P-P2.54-F-LI-2X10P | ZX-PM2.54-2-10PY | ZX-PM2.54-2-10PY | gge444 | yes | yes | ZX-PM2.54-2-10PY
