carletz/DOMIX-Open-Source-Modular-Home-Automation-System/BOM/BOM_U9 - SPRINKLER - UPPER_M9 - Upper Module.xlsx

No. | Quantity | Comment | Designator | Footprint | Value | Manufacturer Part | Manufacturer | Supplier Part | Supplier | LCSC Stock | LCSC Price | Primary Category | Secondary Category | Pin Count | JLCPCB Stock | JLCPCB Price | 3D Model Title | Device | Name | Unique ID | Convert to PCB | Add into BOM | Symbol
1 | 1 | 2.54-2*8P母 | J1 | HDR-TH_16P-P2.54-V-F-R2-C8-S2.54 |  | 2.54-2*8P母 | BOOMELE(博穆精密) | C30734 | LCSC |  |  | Connectors | Female Headers | 16 | 46451 | 0.0196 | HDR-TH_16P-P2.54-F-LI-2X8P | 2.54-2*8P母 | 2.54-2*8P母 | gge506 | yes | yes | Header-Female-2.54_2x8
2 | 8 | MHT192CRCT | LED1,LED2,LED3,LED4,LED5,LED6,LED7,LED8 | LED0603-RD |  | MHT192CRCT | MEIHUA(美华) | C389517 | LCSC |  |  | Optoelectronics | LED Indication - Discrete | 2 | 102980 | 0.0033 | LED0603-RD | MHT192CRCT | MHT192CRCT | gge239_1,gge239_2,gge239_3,gge239_4,gge239_5,gge239_6,gge239_7,gge239_8 | yes | yes | MHT192CRCT
3 | 2 | 470Ω | RN1,RN2 | RES-ARRAY-SMD_0603-8P-L3.2-W1.6-BL | 470Ω | 4D03WGJ0471T5E | UNI-ROYAL(厚声) | C25510 | LCSC |  |  | Resistors | Resistor Networks, Arrays | 8 | 53494 | 0.0011 | R0603-8P_L3.2-W1.6-H0.6 | 4D03WGJ0471T5E | 470Ω | gge507,gge508 | yes | yes | 4D03WGJ0471T5E
4 | 8 | 5.8 ZSPT | SW1,SW2,SW3,SW4,SW5,SW6,SW7,SW8 | SW-TH_5.8ZSPT |  | 5.8 ZSPT | SHOU HAN(首韩) | C2681588 | LCSC |  |  | Switches | Pushbutton Switches | 6 | 18282 | 0.0107 | SW-TH_5.8ZSPT | 5.8 ZSPT | 5.8 ZSPT | gge278,gge278_1,gge278_2,gge278_3,gge278_4,gge278_5,gge278_6,gge278_7 | yes | yes | 5.8 ZSPT
