carletz/DOMIX-Open-Source-Modular-Home-Automation-System/BOM/BOM_V1 - CORE - MIDDLE V1.0_M1 - Middle Module V1.0.xlsx

No. | Quantity | Comment | Designator | Footprint | Value | Manufacturer Part | Manufacturer | Supplier Part | Supplier | LCSC Stock | LCSC Price | Primary Category | Secondary Category | Pin Count | JLCPCB Stock | JLCPCB Price | 3D Model Title | Device | Name | Unique ID | Convert to PCB | Add into BOM | Symbol
1 | 2 | HDR-M_2.54_2x3 | H7,H8 | HDR-TH_6P-P2.54-V-R2-C3-S2.54_A2541WV-2X3P |  |  |  |  |  |  | 0.0169 | Connectors | Pin Headers | 6 |  |  | HDR2.54-M-LI-2x3P | HDR-M_2.54_2x3 |  | gge8,gge9 | yes | yes | HDR-M-2.54_2x3
2 | 2 | 2.54-2*4P弯简牛 | P8,P11 | IDC-TH_8P-P2.54-H-R2-C4-S2.54_1 |  | 2.54-2*4P弯简牛 | BOOMELE(博穆精密) | C9139 | LCSC |  |  | Connectors | IDC Connectors | 8 | 2340 | 0.0178 |  | 2.54-2*4P弯简牛 | 2.54-2*4P弯简牛 | gge7_1,gge7_4 | yes | yes | IDC Box 2X4 2.54MM
3 | 1 | ZX-PM2.54-2-5PY | U2 | HDR-TH_10P-P2.54-V-F-R2-C5-S2.54 |  | ZX-PM2.54-2-5PY | Megastar(兆星) | C7499341 | LCSC |  |  | Connectors | Female Headers | 10 | 955 | 0.0225 | HDR2.54-F-LI-2X5P | ZX-PM2.54-2-5PY | ZX-PM2.54-2-5PY | gge437_1 | yes | yes | ZX-PM2.54-2-5PY
