carletz/DOMIX-Open-Source-Modular-Home-Automation-System/BOM/BOM_V1 - CORE - MIDDLE V1.2_M1 - Middle Module V1.2.xlsx

No. | Quantity | Comment | Designator | Footprint | Value | Manufacturer Part | Manufacturer | Supplier Part | Supplier | LCSC Stock | LCSC Price | Primary Category | Secondary Category | Pin Count | JLCPCB Stock | JLCPCB Price | 3D Model Title | Device | Name | Unique ID | Convert to PCB | Add into BOM | Symbol
1 | 1 | 10uF | C9 | C0603 | 10uF | CL10A106KP8NNNC | SAMSUNG(三星) | C19702 | LCSC |  |  | Capacitors | Multilayer Ceramic Capacitors MLCC - SMD/SMT | 2 | 18469542 | 0.001 | C0603_L1.6-W0.8-H0.8 | CL10A106KP8NNNC | 10uF | gge432 | yes | yes | CL10A106KP8NNNC
2 | 2 | HDR-M_2.54_2x3 | H7,H8 | HDR-TH_6P-P2.54-V-R2-C3-S2.54_A2541WV-2X3P |  |  |  |  |  |  | 0.0013 | Connectors | Pin Headers | 6 |  |  | HDR2.54-M-LI-2x3P | HDR-M_2.54_2x3 |  | gge8,gge9 | yes | yes | HDR-M-2.54_2x3
3 | 4 | 2.54-2*4P弯简牛 | P8,P9,P10,P11 | IDC-TH_8P-P2.54-H-R2-C4-S2.54_1 |  | 2.54-2*4P弯简牛 | BOOMELE(博穆精密) | C9139 | LCSC |  |  | Connectors | IDC Connectors | 8 | 2340 | 0.0178 |  | 2.54-2*4P弯简牛 | 2.54-2*4P弯简牛 | gge7_1,gge7_2,gge7_3,gge7_4 | yes | yes | IDC Box 2X4 2.54MM
4 | 16 | 2.2kΩ | R6,R7,R8,R9,R10,R11,R12,R13,R14,R15,R16,R17,R18,R19,R20,R21 | R0603 | 2.2kΩ | FRC0603F2201TS | FOJAN(富捷) | C2907005 | LCSC |  |  | Resistors | Chip Resistor - Surface Mount | 2 | 3498670 | 0.0002 | R0603 | FRC0603F2201TS | 2.2kΩ | gge435,gge435_1,gge435_2,gge435_3,gge435_4,gge435_5,gge435_6,gge435_7,gge436,gge436_1,gge436_2,gge436_3,gge436_4,gge436_5,gge436_6,gge436_7 | yes | yes | FRC0603F2201TS
5 | 1 | 10kΩ | R22 | R0603 | 10kΩ | FRC0603F1002TS | FOJAN(富捷) | C2906982 | LCSC |  |  | Resistors | Chip Resistor - Surface Mount | 2 | 15261777 | 0.0002 | R0603 | FRC0603F1002TS | 10kΩ | gge422 | yes | yes | FRC0603F1002TS
6 | 1 | TCA9548APWR | U1 | TSSOP-24_L7.8-W4.4-P0.65-LS6.4-BL |  | TCA9548APWR | TI(德州仪器) | C130026 | LCSC |  |  | Interface | Interface - Specialized | 24 | 4323 | 0.0713 | TSSOP-24_L7.8-W4.4-H1.0-LS6.4-P0.65 | TCA9548APWR | TCA9548APWR | gge433 | yes | yes | TCA9548APWR
7 | 1 | ZX-PM2.54-2-5PY | U2 | HDR-TH_10P-P2.54-V-F-R2-C5-S2.54 |  | ZX-PM2.54-2-5PY | Megastar(兆星) | C7499341 | LCSC |  |  | Connectors | Female Headers | 10 | 955 | 0.0225 | HDR2.54-F-LI-2X5P | ZX-PM2.54-2-5PY | ZX-PM2.54-2-5PY | gge437_1 | yes | yes | ZX-PM2.54-2-5PY
