carletz/DOMIX-Open-Source-Modular-Home-Automation-System/BOM/BOM_V3-4-5-6 - MULTI - VERTICAL_M3-4-5-6 - Vertical Module.xlsx

No. | Quantity | Comment | Designator | Footprint | Value | Manufacturer Part | Manufacturer | Supplier Part | Supplier | LCSC Stock | LCSC Price | Primary Category | Secondary Category | Pin Count | JLCPCB Stock | JLCPCB Price | 3D Model Title | Device | Name | Unique ID | Convert to PCB | Add into BOM | Symbol
1 | 2 | A254AD-WS04P | H5,H6 | HDR-TH_8P-P2.54-H-M-R2-C4-S2.54-W12.4-N |  | A254AD-WS04P | BXCONN(宝讯) | C41413854 | LCSC |  |  | Connectors | Pin Headers | 8 | 6100 | 0.0064 | HDR-TH_8P-P2.54-H-M-R2-C4-S2.54-W12.4-N | A254AD-WS04P | A254AD-WS04P | gge8,gge9 | yes | yes | A254AD-WS04P
2 | 2 | 2.54-2*4P弯简牛 | P7,P8 | IDC-TH_8P-P2.54-H-R2-C4-S2.54_1 |  | 2.54-2*4P弯简牛 | BOOMELE(博穆精密) | C9139 | LCSC |  |  | Connectors | IDC Connectors | 8 | 2340 | 0.0178 |  | 2.54-2*4P弯简牛 | 2.54-2*4P弯简牛 | gge7,gge7_1 | yes | yes | IDC Box 2X4 2.54MM
