carletz/DOMIX-Open-Source-Modular-Home-Automation-System/BOM/BOM_V9 - SPRINKLER - VERTICAL_M9 - Vertical Module.xlsx

No. | Quantity | Comment | Designator | Footprint | Value | Manufacturer Part | Manufacturer | Supplier Part | Supplier | LCSC Stock | LCSC Price | Primary Category | Secondary Category | Pin Count | JLCPCB Stock | JLCPCB Price | 3D Model Title | Device | Name | Unique ID | Convert to PCB | Add into BOM | Symbol
1 | 2 | 2.54-2*4P弯简牛 | P7,P8 | IDC-TH_8P-P2.54-H-R2-C4-S2.54_1 |  | 2.54-2*4P弯简牛 | BOOMELE(博穆精密) | C9139 | LCSC |  |  | Connectors | IDC Connectors | 8 | 2340 | 0.0178 |  | 2.54-2*4P弯简牛 | 2.54-2*4P弯简牛 | gge7,gge7_1 | yes | yes | IDC Box 2X4 2.54MM
2 | 2 | 2541WR-2x08P | U1,U2 | HDR-TH_16P-P2.54-H-M-R2-C8-S2.54 |  | 2541WR-2x08P | HanElectricity(瀚源) | C5383092 | LCSC |  |  | Connectors | Pin Headers | 16 | 4468 | 0.0095 | HDR-TH_16P-P2.54-M-WI-2X8P | 2541WR-2x08P | 2541WR-2x08P | gge8,gge9 | yes | yes | 2541WR-2X08P
