carletz/DOMIX-Open-Source-Modular-Home-Automation-System/3D Print files/M6 - ENERGY - Top clean.STL

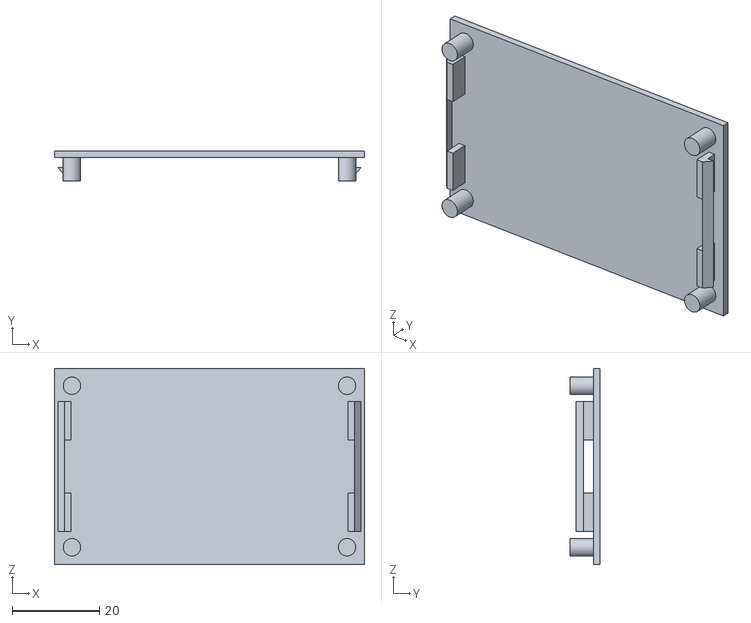
[picture p104: CAD file, 2026-03-12]
3D Print files/M6 - ENERGY - Top clean.STL
71.0 x 6.80 x 45.0
