carletz/DOMIX-Open-Source-Modular-Home-Automation-System/3D Print files/S - Wall Cover clean no hole.STL

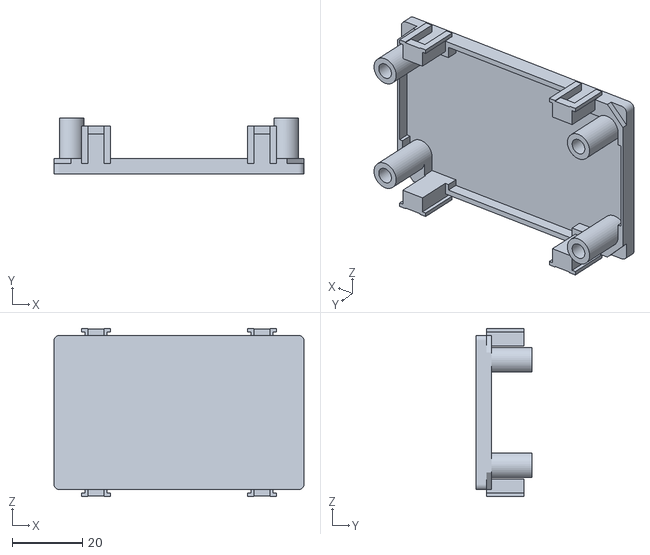
[picture p105: CAD file, 2026-03-12]
3D Print files/S - Wall Cover clean no hole.STL
71.0 x 16.0 x 47.8
