carletz/DOMIX-Open-Source-Modular-Home-Automation-System/3D Print files/M7 - OUTPUT - Top clean.STL

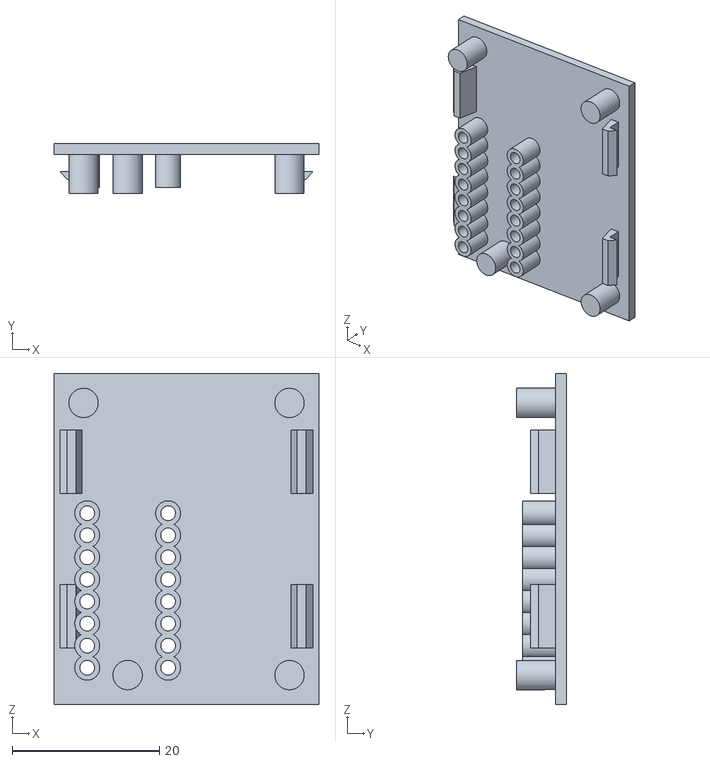
[picture p106: CAD file, 2026-03-12]
3D Print files/M7 - OUTPUT - Top clean.STL
36.0 x 6.80 x 45.0
