carletz/DOMIX-Open-Source-Modular-Home-Automation-System/3D Print files/M9 - SPRINKLER - Top clean.STL

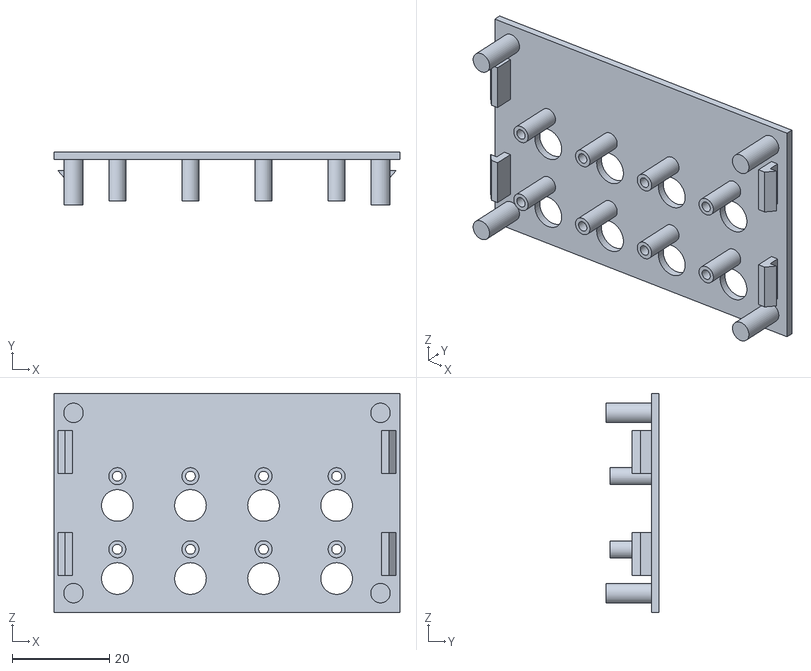
[picture p107: CAD file, 2026-03-12]
3D Print files/M9 - SPRINKLER - Top clean.STL
71.0 x 10.8 x 45.0
