carletz/DOMIX-Open-Source-Modular-Home-Automation-System/3D Print files/S - Ceiling Top Cover clean.STL

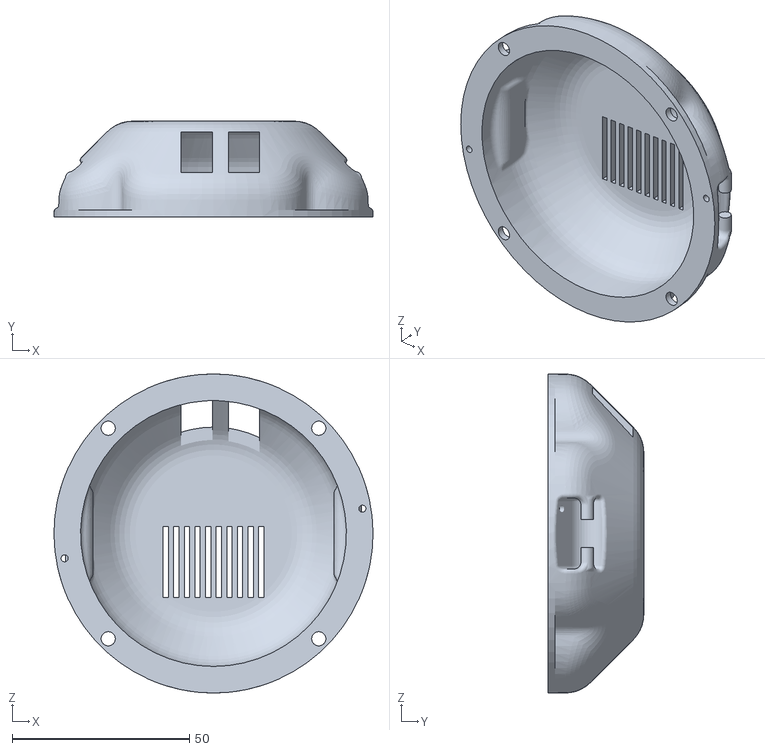
[picture p108: CAD file, 2026-03-12]
3D Print files/S - Ceiling Top Cover clean.STL
90.0 x 27.0 x 90.0
