carletz/DOMIX-Open-Source-Modular-Home-Automation-System/3D Print files/M4 - 6 RELAY - Top clean hole.STL

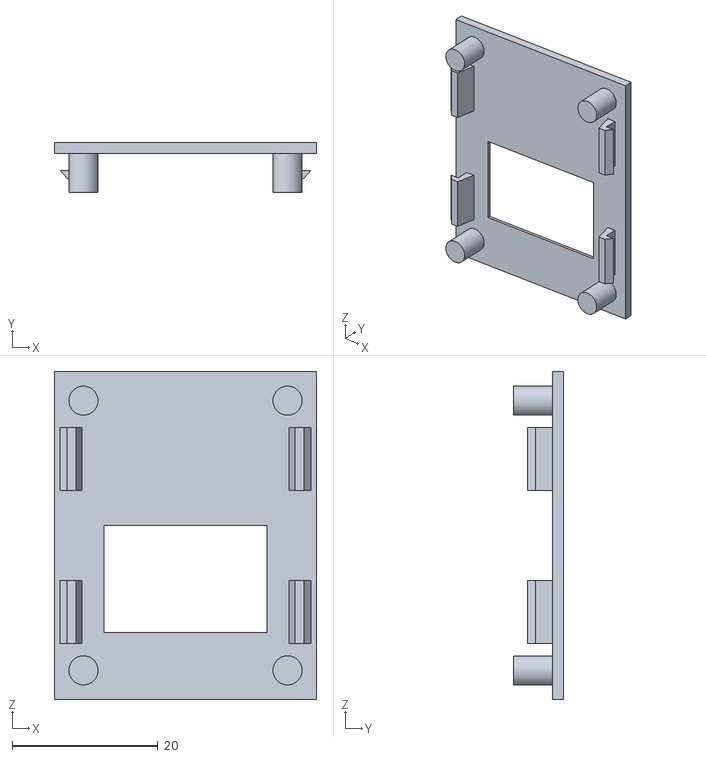
[picture p109: CAD file, 2026-03-12]
3D Print files/M4 - 6 RELAY - Top clean hole.STL
36.0 x 6.80 x 45.0
