carletz/DOMIX-Open-Source-Modular-Home-Automation-System/3D Print files/S - Ceiling External.STL

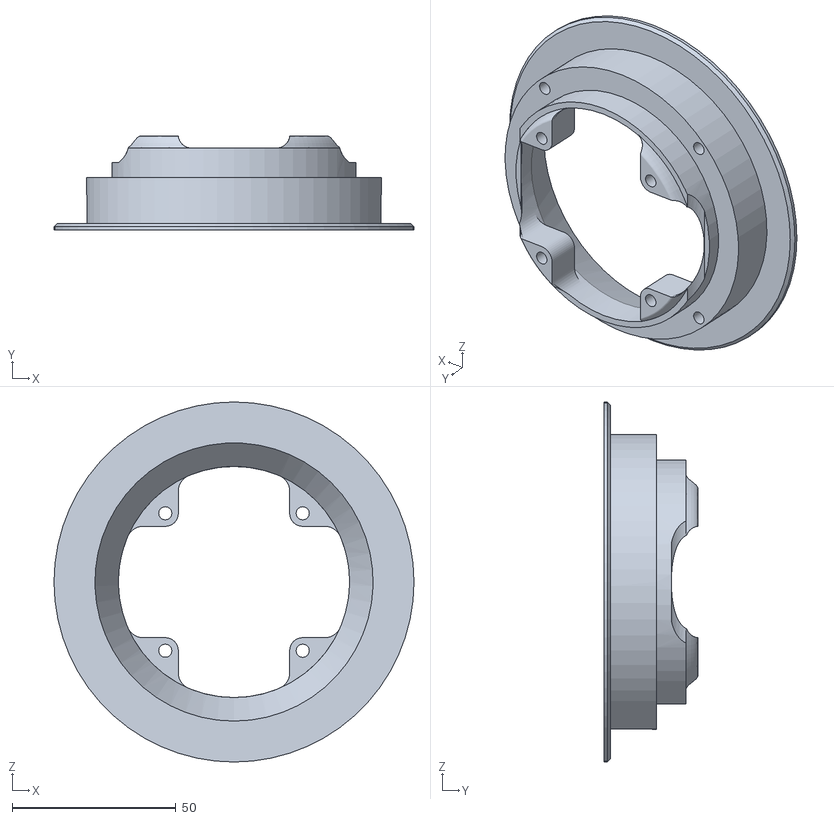
[picture p111: CAD file, 2026-03-01]
3D Print files/S - Ceiling External.STL
110.0 x 28.6 x 110.0
