carletz/DOMIX-Open-Source-Modular-Home-Automation-System/3D Print files/S - Ceiling Cover.STL

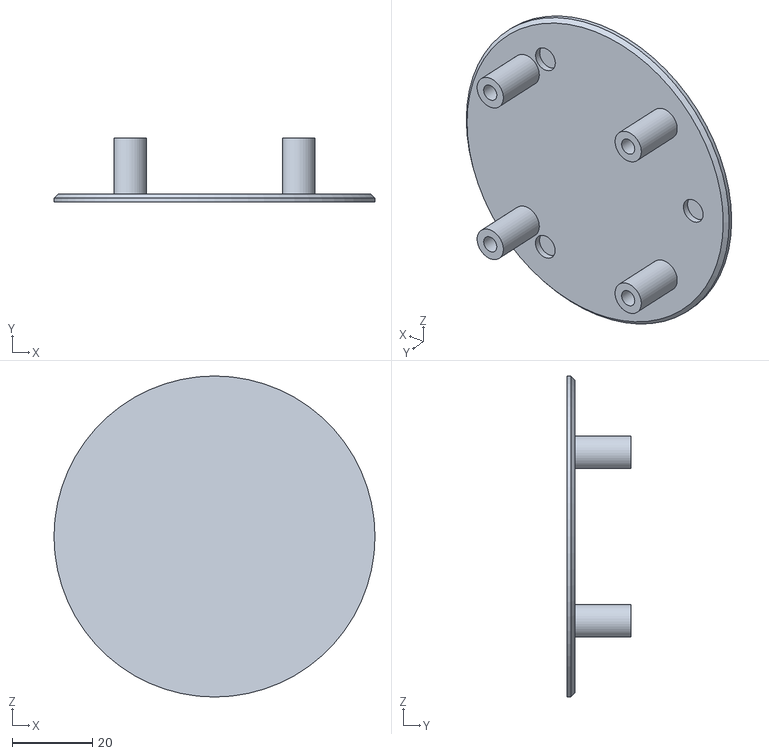
[picture p112: CAD file, 2026-03-01]
3D Print files/S - Ceiling Cover.STL
80.0 x 16.0 x 80.0
