carletz/DOMIX-Open-Source-Modular-Home-Automation-System/3D Print files/S - Ceiling Top Cover.3MF

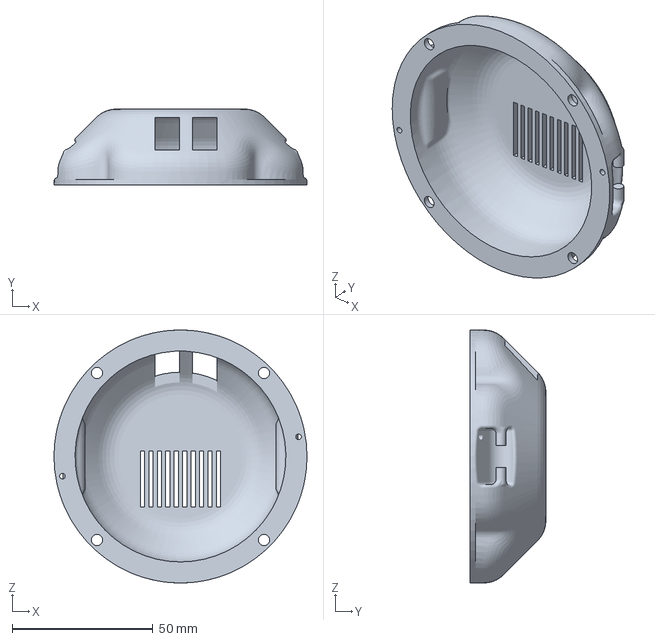
[picture p113: CAD file, 2026-03-01]
3D Print files/S - Ceiling Top Cover.3MF
90.0 x 27.0 x 90.0 mm
