carletz/DOMIX-Open-Source-Modular-Home-Automation-System/3D Print files/S - Ceiling Cover PIR.STL

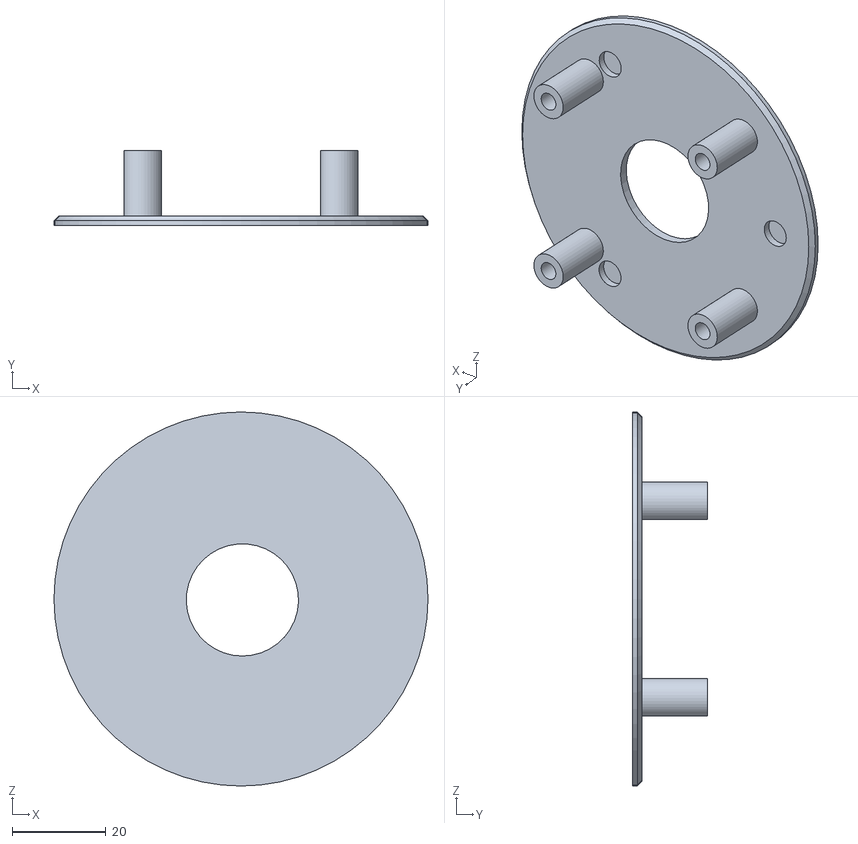
[picture p114: CAD file, 2026-03-01]
3D Print files/S - Ceiling Cover PIR.STL
80.0 x 16.0 x 80.0
