carletz/DOMIX-Open-Source-Modular-Home-Automation-System/3D Print files/M3 - CONTACT - Bottom.STL

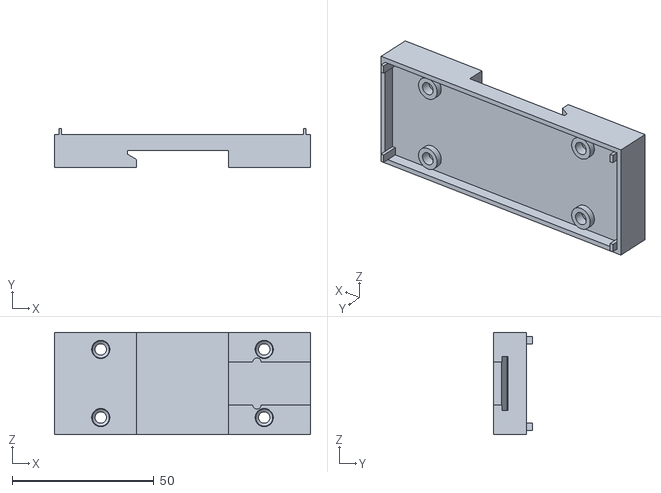
[picture p115: CAD file, 2026-02-15]
3D Print files/M3 - CONTACT - Bottom.STL
90.2 x 13.6 x 36.0
