carletz/DOMIX-Open-Source-Modular-Home-Automation-System/3D Print files/Stopper.STL

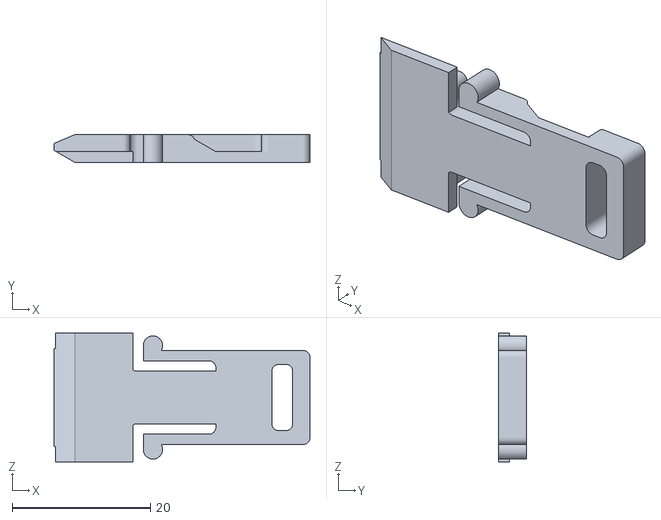
[picture p116: CAD file, 2026-02-15]
3D Print files/Stopper.STL
37.0 x 4.00 x 18.6
