carletz/DOMIX-Open-Source-Modular-Home-Automation-System/3D Print files/M3 - CONTACT - Top Clean.3MF

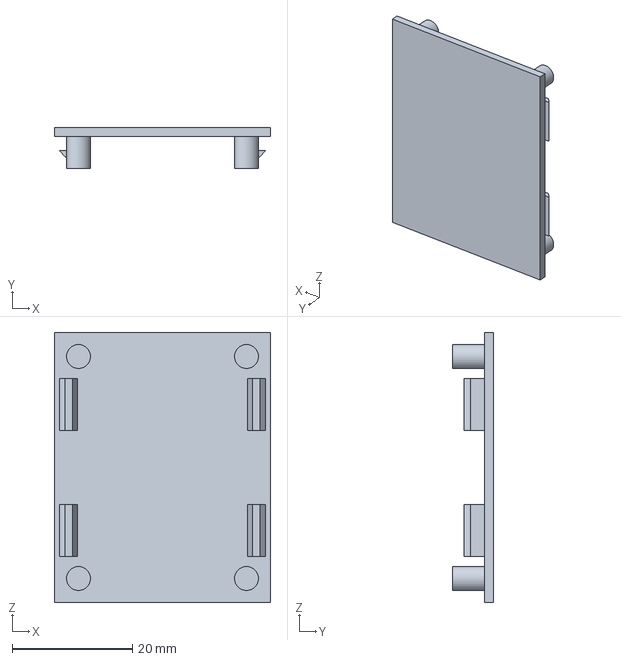
[picture p117: CAD file, 2026-02-15]
3D Print files/M3 - CONTACT - Top Clean.3MF
36.0 x 6.80 x 45.0 mm
