carletz/DOMIX-Open-Source-Modular-Home-Automation-System/3D Print files/M3 - CONTACT - Indication2.3MF

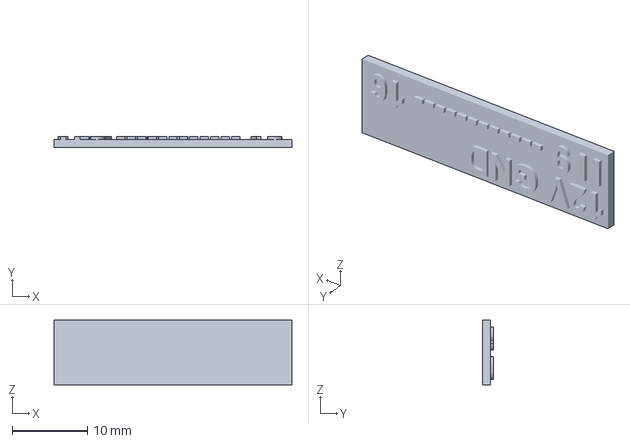
[picture p120: CAD file, 2026-02-15]
3D Print files/M3 - CONTACT - Indication2.3MF
31.6 x 1.40 x 8.60 mm
