carletz/DOMIX-Open-Source-Modular-Home-Automation-System/3D Print files/M6 - ENERGY - Box.STL

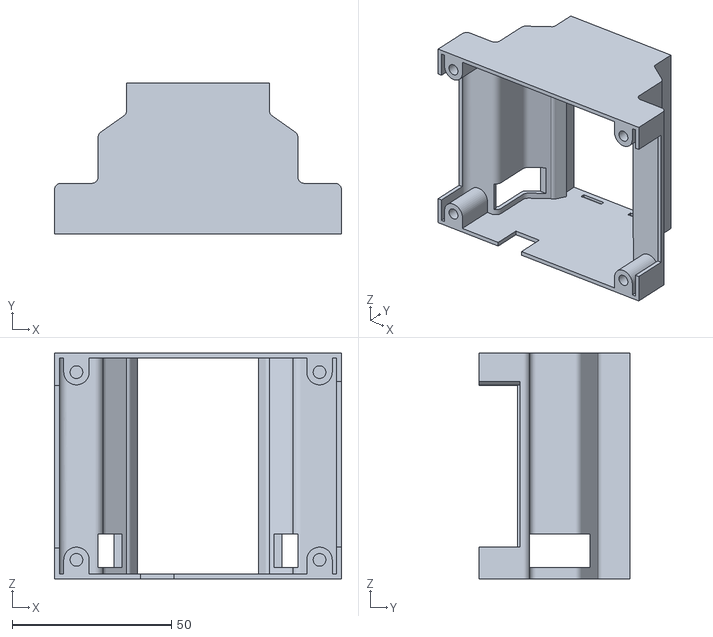
[picture p121: CAD file, 2026-02-15]
3D Print files/M6 - ENERGY - Box.STL
90.2 x 47.4 x 71.0
