carletz/DOMIX-Open-Source-Modular-Home-Automation-System/3D Print files/DOMIX.3mf

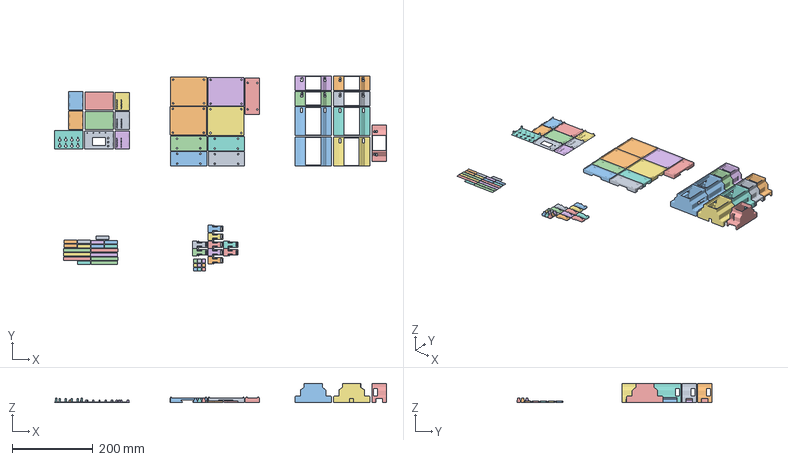
[picture p122: CAD file, 2026-02-15]
3D Print files/DOMIX.3mf
821.6 x 483.1 x 47.4 mm
M2 - IO - Top
M3 - CONTACT Top Clean
M4 - 6 RELAY Top Clean
M5 - 12 RELAY - Top
M6 - ENERGY - Top
M7 - OUTPUT - Top
M8 - INPUT - Top
M9 - SPRINKLER - Top
M1 - CORE - Top
M1 - CORE - Bottom.STL
M2 - IO - Bottom.STL
M3 - CONTACT - Bottom.STL
M4 - 6 RELAY - Bottom.STL
M5 - 12 RELAY - Bottom.STL
M6 - ENERGY - Bottom.STL
M7 - OUTPUT - Bottom.STL
M8 - INPUT - Bottom.STL
M9 - SPRINKLER - Bottom.STL
M1 - CORE - Box.STL
M2 - IO - Box.STL
M3 - CONTACT - Box.STL
M4 - 6 RELAY - Box.STL
M5 - 12 RELAY - Box.STL
M6 - ENERGY - Box.STL
M7 - OUTPUT - Box.STL
M8 - INPUT - Box.STL
M9 - SPRINKLER - Box.STL
M1 - CORE - Indication
M1 - CORE - Indication2
M2 - IO - Indication
M2 - IO - Indication2
M3 - CONTACT - Indication
M3 - CONTACT - Indication2
M4 - 6 RELAY - Indication
M4 - 6 RELAY - Indication2
M5 - 12 RELAY - Indication
M5 - 12 RELAY - Indication2
M6 - ENERGY - Indication
M6 - ENERGY - Indication2
M7 - OUTPUT - Indication
M7 - OUTPUT - Indication2
M8 - INPUT - Indication
M8 - INPUT - Indication2
M9 - SPRINKLER - Indication
Stopper.STL x 9
M9 - SPRINKLER - Button.STL x 9
