carletz/DOMIX-Open-Source-Modular-Home-Automation-System/3D Print files/M3 - CONTACT - Top Screen.3MF

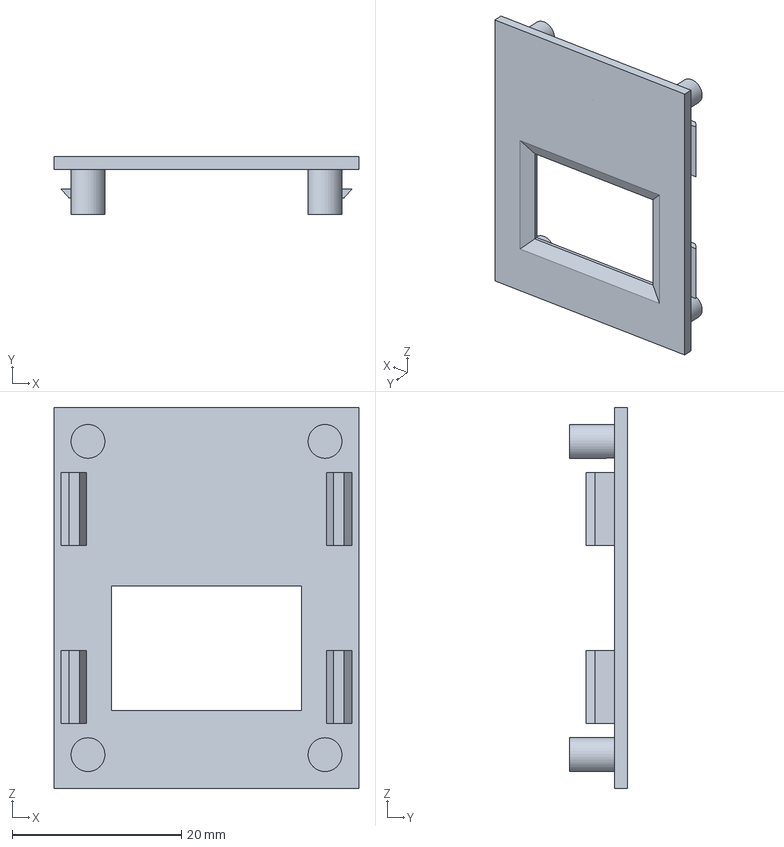
[picture p123: CAD file, 2026-02-15]
3D Print files/M3 - CONTACT - Top Screen.3MF
36.0 x 6.80 x 45.0 mm
