carletz/DOMIX-Open-Source-Modular-Home-Automation-System/3D Print files/M8 - INPUT - Top.3MF

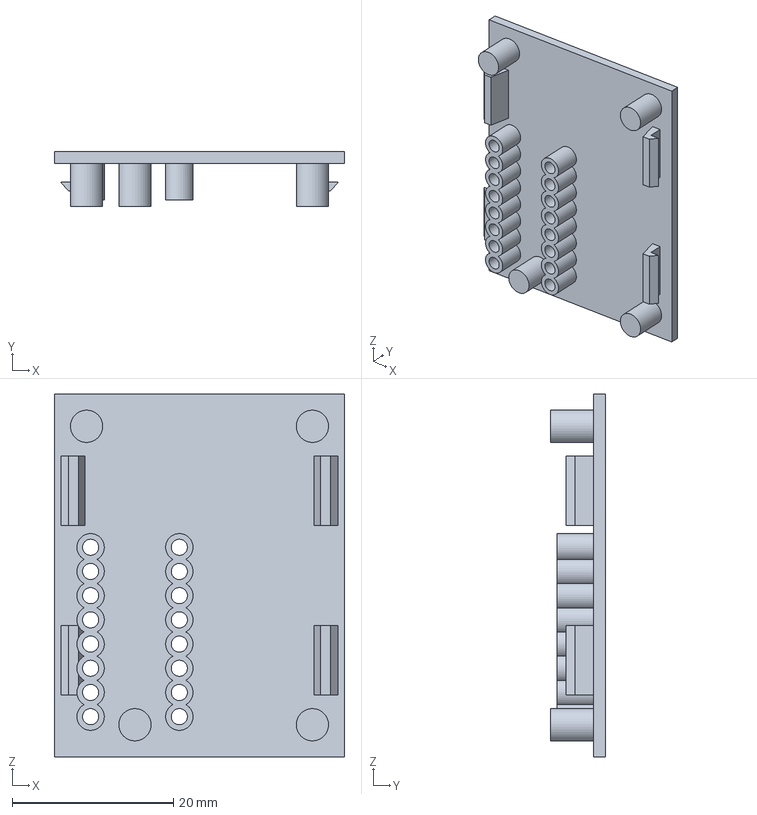
[picture p124: CAD file, 2026-02-15]
3D Print files/M8 - INPUT - Top.3MF
36.0 x 6.80 x 45.0 mm
