carletz/DOMIX-Open-Source-Modular-Home-Automation-System/3D Print files/M1 - CORE - Box.STL

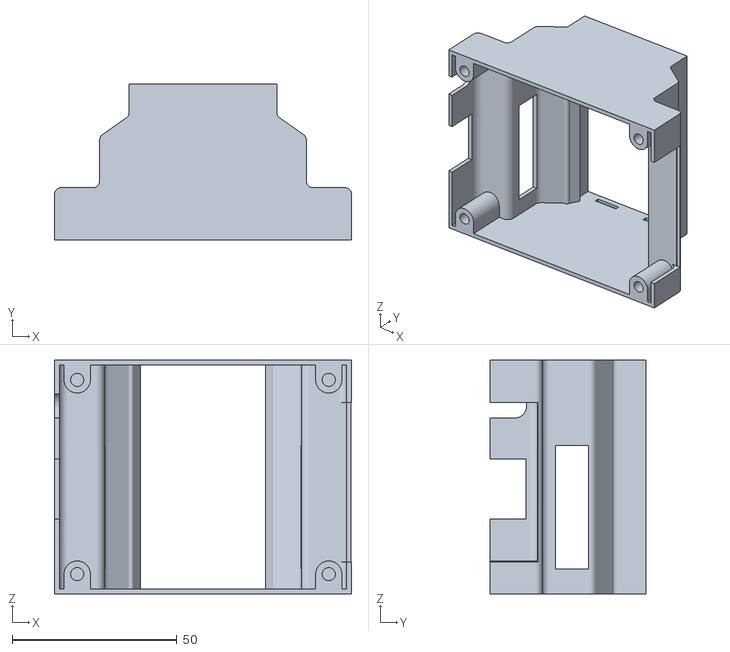
[picture p125: CAD file, 2026-02-15]
3D Print files/M1 - CORE - Box.STL
90.2 x 47.4 x 71.0
