carletz/DOMIX-Open-Source-Modular-Home-Automation-System/3D Print files/M5 - 12 RELAY - Top.3MF

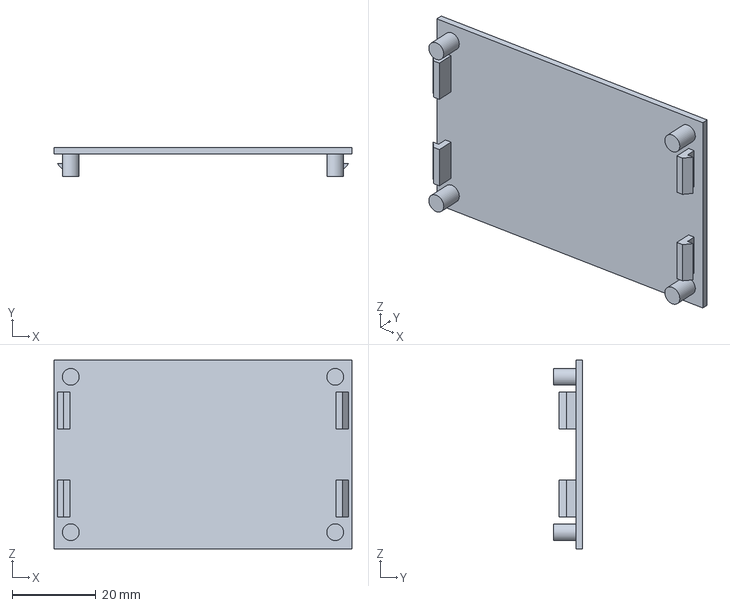
[picture p127: CAD file, 2026-02-15]
3D Print files/M5 - 12 RELAY - Top.3MF
71.0 x 6.80 x 45.0 mm
