carletz/DOMIX-Open-Source-Modular-Home-Automation-System/3D Print files/M1 - CORE - Bottom.STL

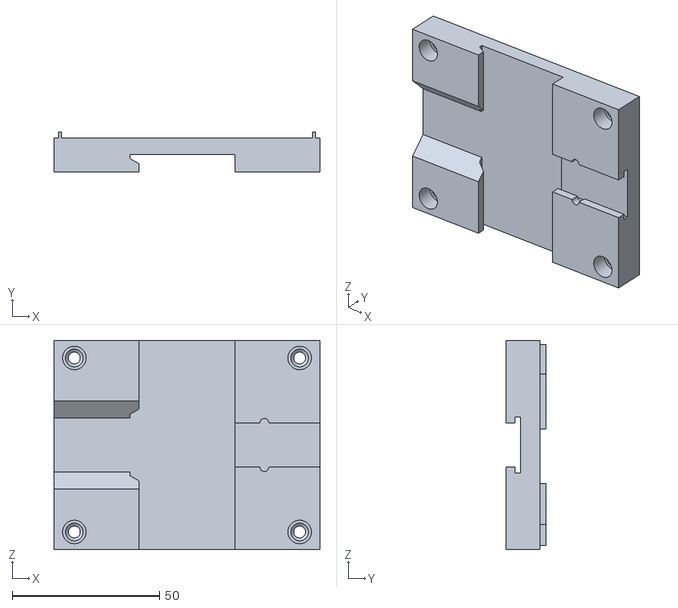
[picture p128: CAD file, 2026-02-15]
3D Print files/M1 - CORE - Bottom.STL
90.2 x 13.6 x 71.0
