carletz/DOMIX-Open-Source-Modular-Home-Automation-System/3D Print files/M2 - IO - Box.STL

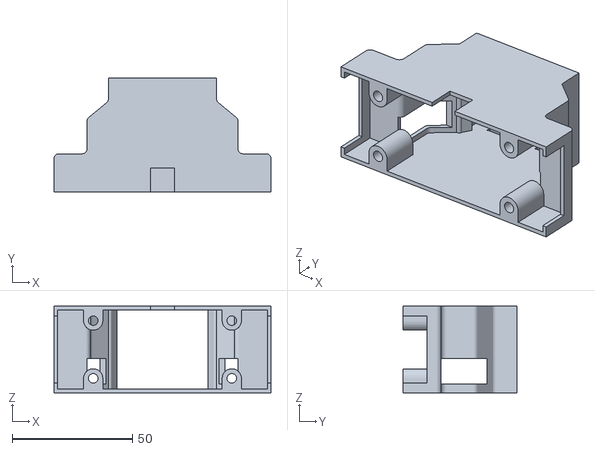
[picture p129: CAD file, 2026-02-15]
3D Print files/M2 - IO - Box.STL
90.2 x 47.4 x 36.0
