carletz/DOMIX-Open-Source-Modular-Home-Automation-System/3D Print files/M1 - CORE - Top.3MF

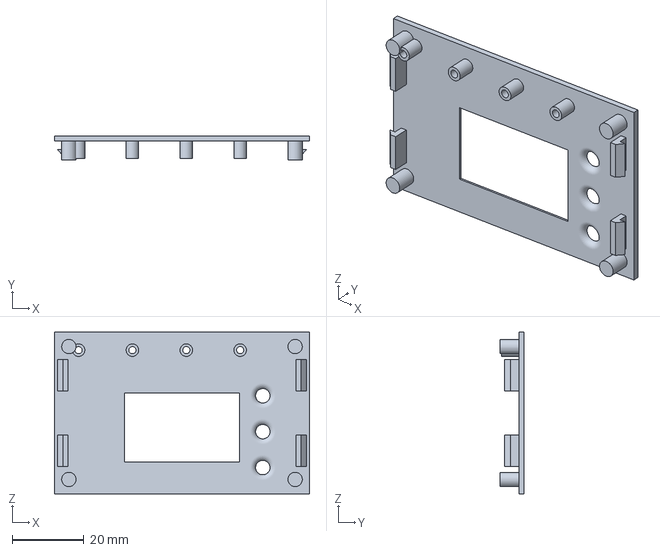
[picture p131: CAD file, 2026-02-15]
3D Print files/M1 - CORE - Top.3MF
71.0 x 6.80 x 45.0 mm
