carletz/DOMIX-Open-Source-Modular-Home-Automation-System/3D Print files/M9 - SPRINKLER - Top.3MF

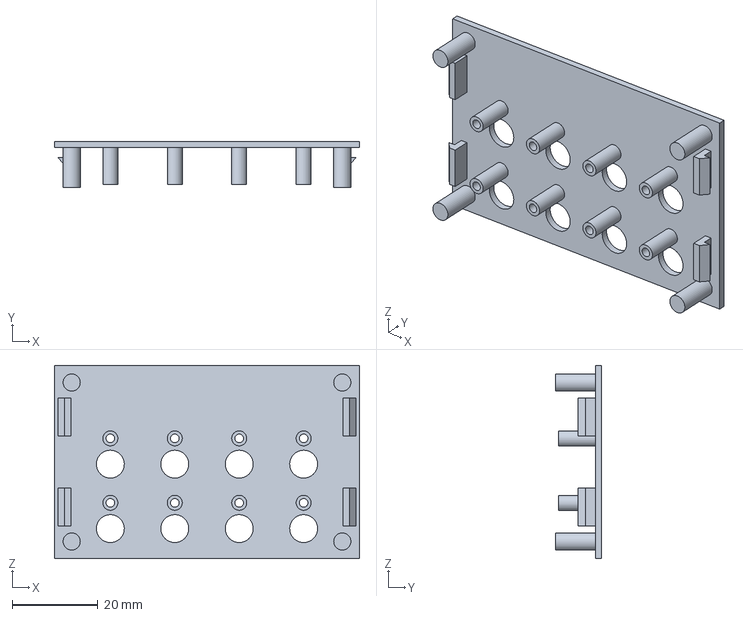
[picture p132: CAD file, 2026-02-15]
3D Print files/M9 - SPRINKLER - Top.3MF
71.0 x 10.8 x 45.0 mm
