carletz/DOMIX-Open-Source-Modular-Home-Automation-System/3D Print files/M6 - ENERGY - Top.3MF

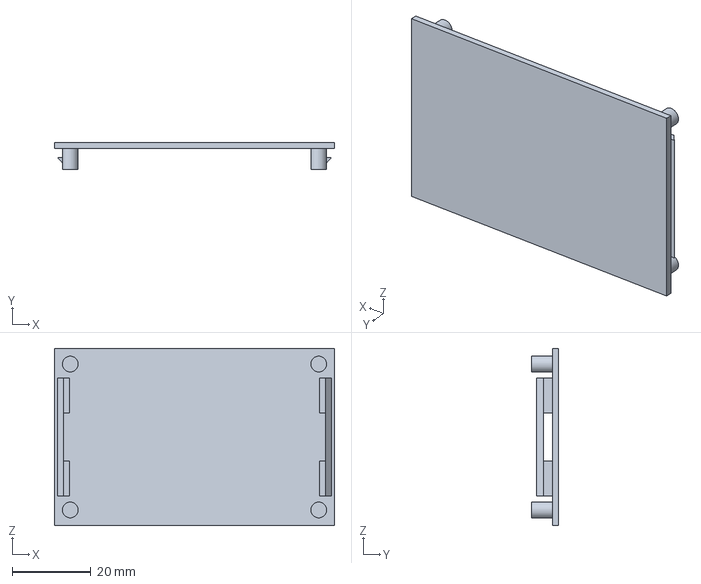
[picture p133: CAD file, 2026-02-15]
3D Print files/M6 - ENERGY - Top.3MF
71.0 x 6.80 x 45.0 mm
