carletz/DOMIX-Open-Source-Modular-Home-Automation-System/3D Print files/M9 - SPRINKLER - Box.STL

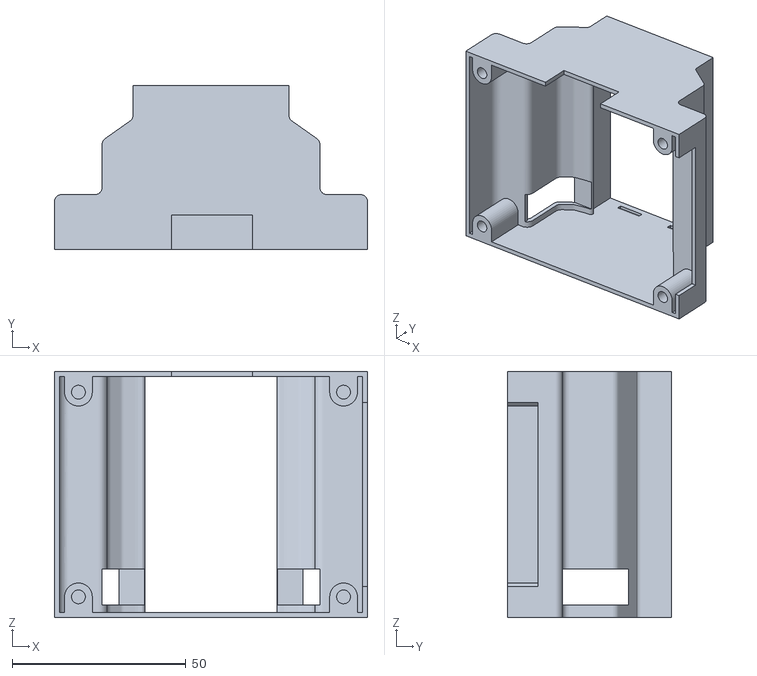
[picture p135: CAD file, 2026-02-15]
3D Print files/M9 - SPRINKLER - Box.STL
90.2 x 47.4 x 71.0
