carletz/DOMIX-Open-Source-Modular-Home-Automation-System/3D Print files/M2 - IO - Top.3MF

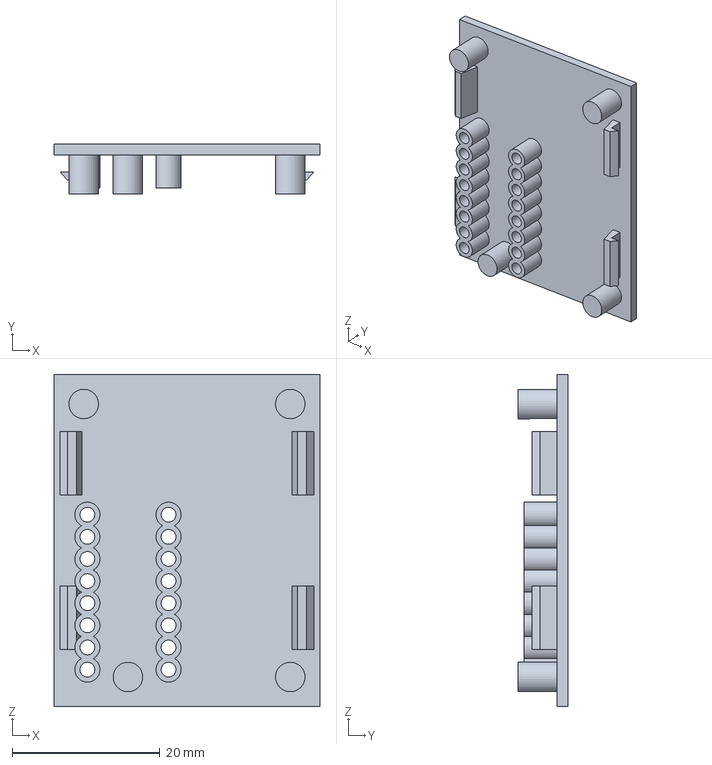
[picture p138: CAD file, 2026-02-15]
3D Print files/M2 - IO - Top.3MF
36.0 x 6.80 x 45.0 mm
