carletz/DOMIX-Open-Source-Modular-Home-Automation-System/3D Print files/M9 - SPRINKLER - Button.STL

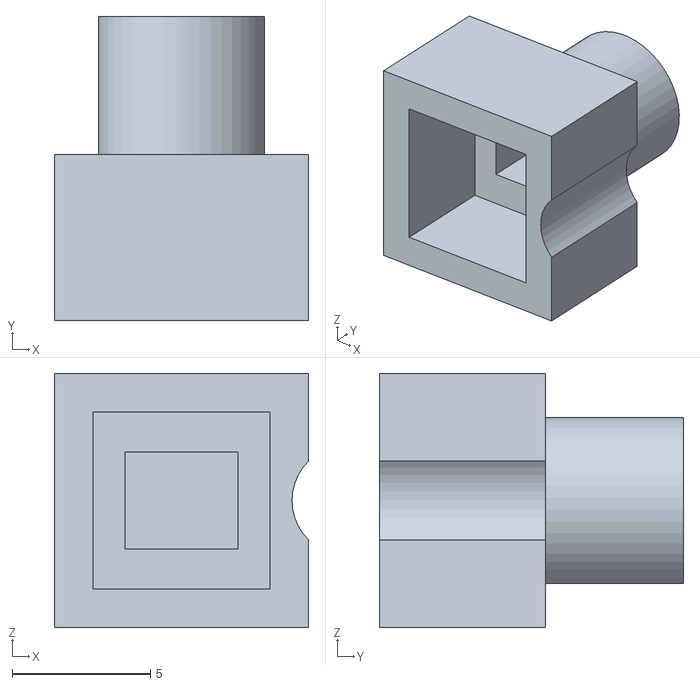
[picture p142: CAD file, 2026-02-15]
3D Print files/M9 - SPRINKLER - Button.STL
9.20 x 11.0 x 9.20
