carletz/DOMIX-Open-Source-Modular-Home-Automation-System/3D Print files/M1 - CORE - Indication.3MF

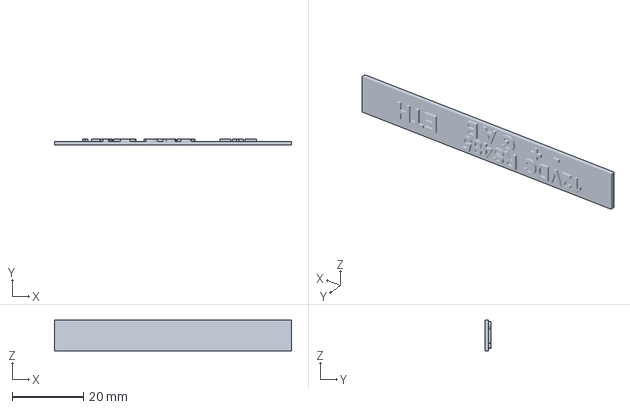
[picture p143: CAD file, 2026-02-15]
3D Print files/M1 - CORE - Indication.3MF
66.6 x 1.60 x 8.60 mm
