carletz/DOMIX-Open-Source-Modular-Home-Automation-System/M8 - INPUT/SCH_M8 - I-O Module_2026-02-14.pdf

# PINOUT

# Domotic Module for smart home & co

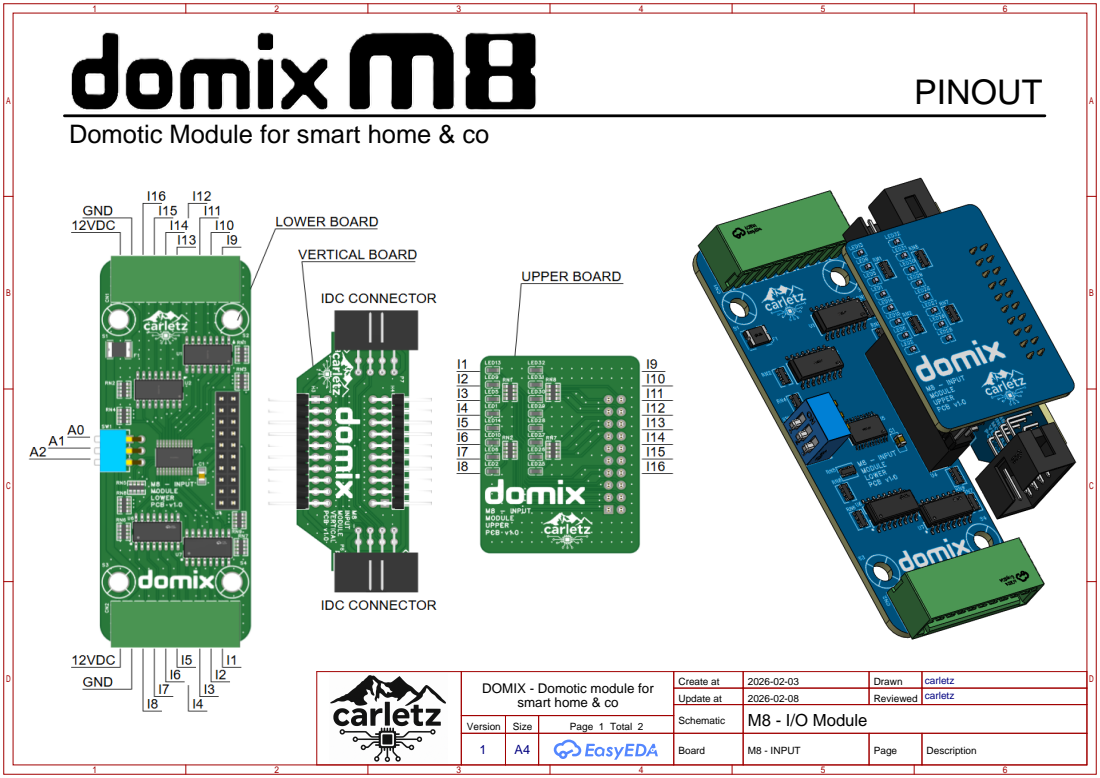
[picture p165: page 1]

smart home & co | Create at | 2026-02-03 | Drawn | carletz DOMIX - Domotic module for

Update at | 2026-02-08 | Reviewed | carletz

Schematic | M8 - I/O Module
1 | A4 | | Board | M8 - INPUT | Page | Description

Version | Size | Page 1 Total 2

# I/O Logic

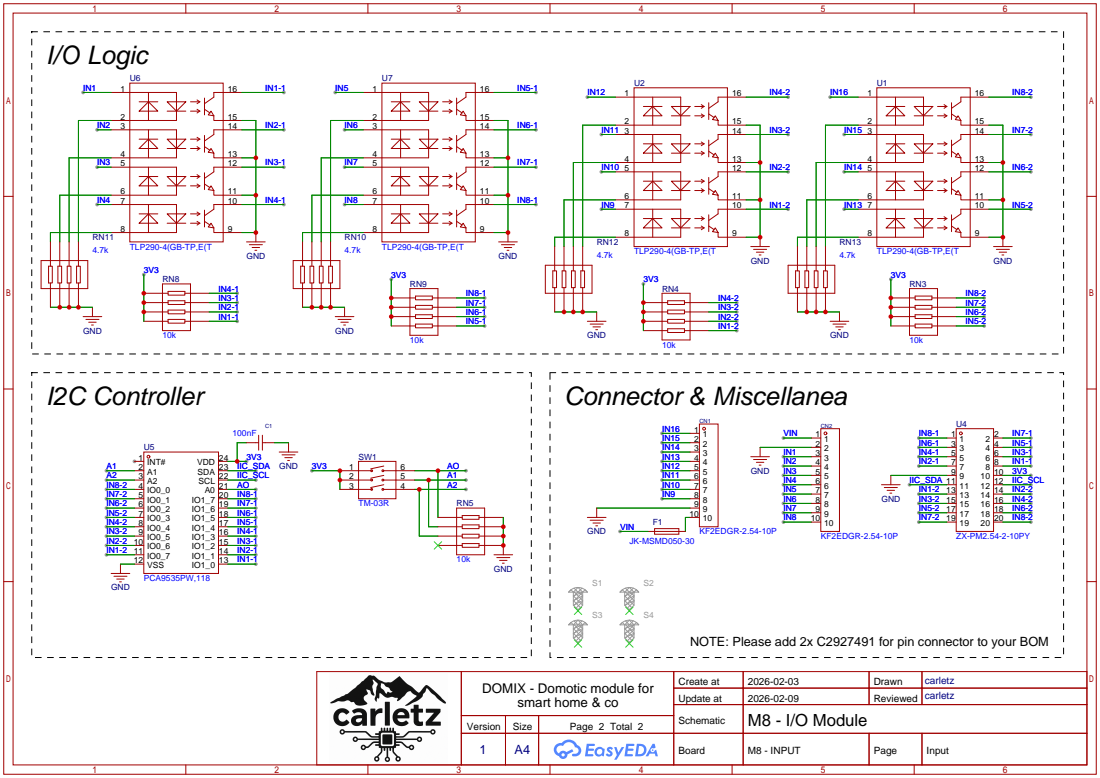
[picture p166: page 2]

NOTE: Please add 2x C2927491 for pin connector to your BOM

smart home & co | Create at | 2026-02-03 | Drawn | carletz DOMIX - Domotic module for

Update at | 2026-02-09 | Reviewed | carletz

Schematic | M8 - I/O Module
1 | A4 | | Board | M8 - INPUT | Page | Input

Version | Size | Page 2 Total 2
