carletz/DOMIX-Open-Source-Modular-Home-Automation-System/M7 - OUTPUT/SCH_M7 - Display Module_2026-02-14.pdf

# Led Indicator

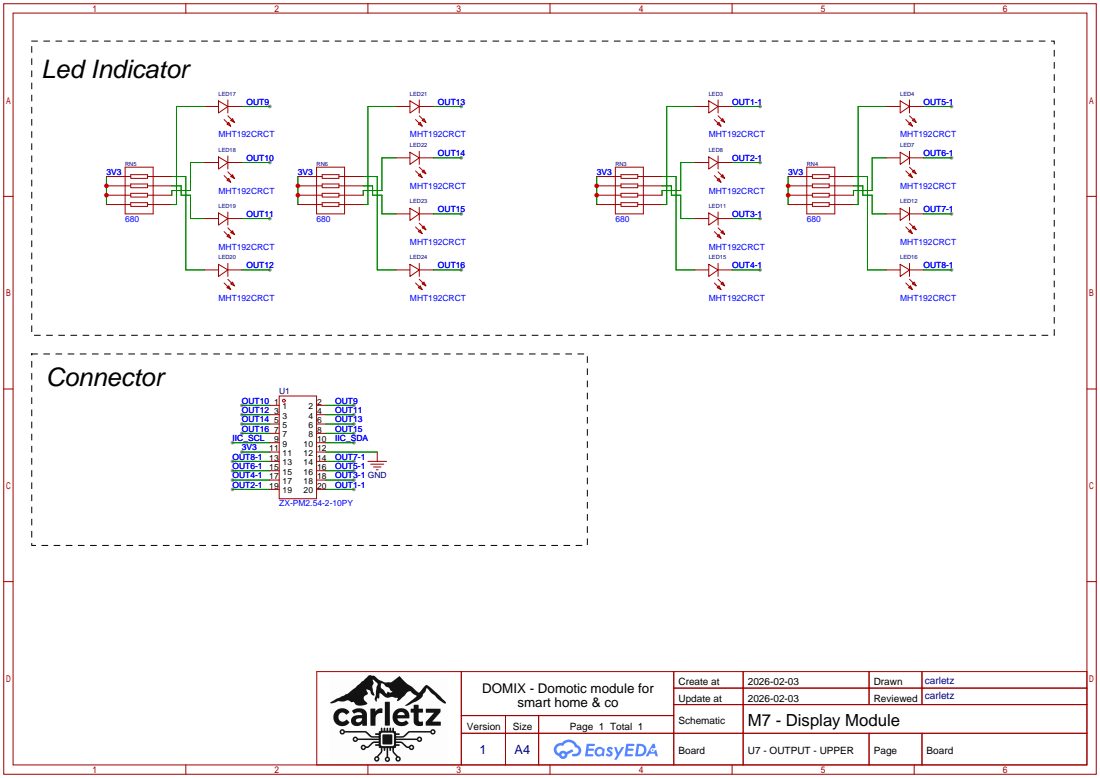
[picture p167: page 1]

smart home & co | Create at | 2026-02-03 | Drawn | carletz DOMIX - Domotic module for

Update at | 2026-02-03 | Reviewed | carletz

Schematic | M7 - Display Module
1 | A4 | | Board | U7 - OUTPUT - UPPER | Page | Board

Version | Size | Page 1 Total 1
