carletz/DOMIX-Open-Source-Modular-Home-Automation-System/M7 - OUTPUT/SCH_M7 - Output Module_2026-02-14.pdf

# PINOUT

# Domotic Module for smart home & co

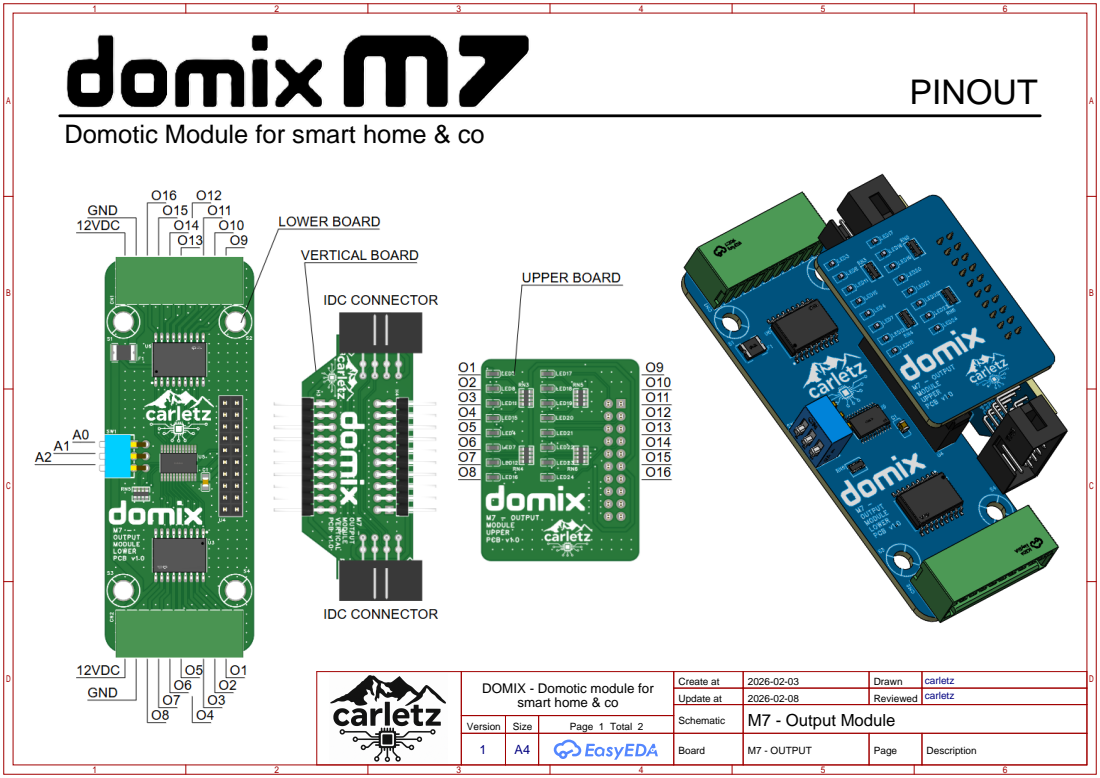
[picture p168: page 1]

smart home & co | Create at | 2026-02-03 | Drawn | carletz DOMIX - Domotic module for

Update at | 2026-02-08 | Reviewed | carletz

Schematic | M7 - Output Module
1 | A4 | | Board | M7 - OUTPUT | Page | Description

Version | Size | Page 1 Total 2

# COM 10 Output 11 Output 12 Output 13 Output 14 Output 15 Output 16 Output 17 Output 18

# Output Logic

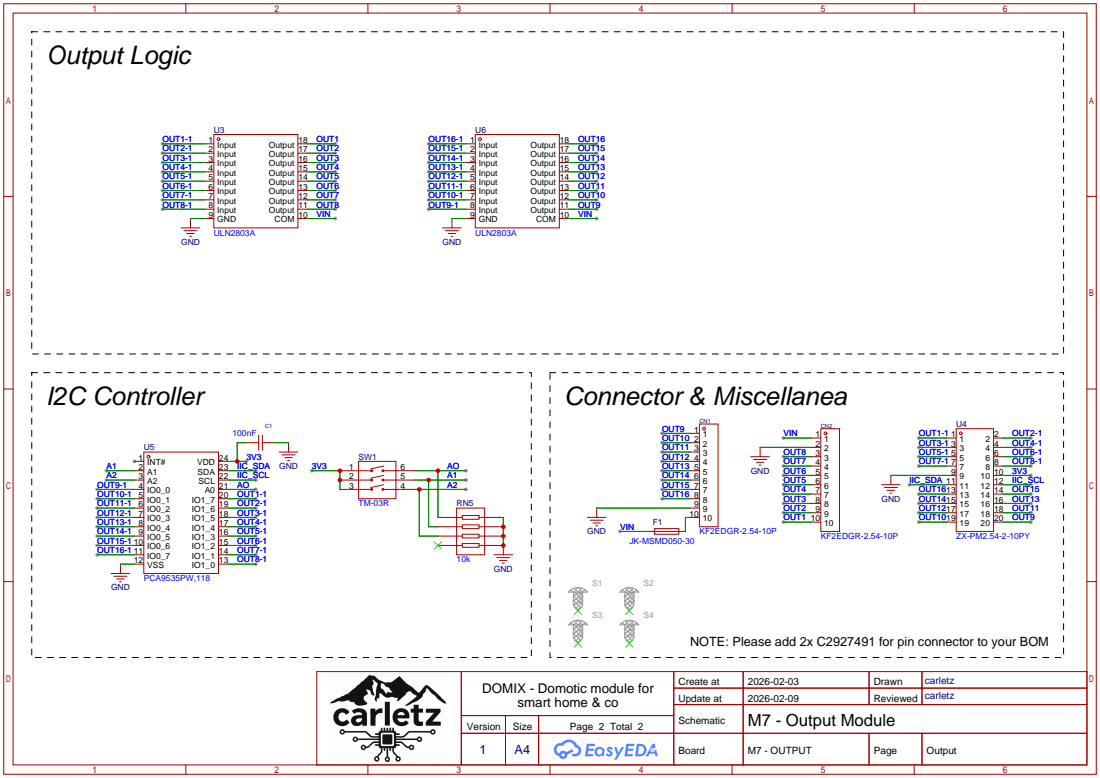
[picture p169: page 2]

OUT16
COM 10 Output 11 Output 12 Output 13 Output 14 Output 15 Output 16 Output 17 Output 18

NOTE: Please add 2x C2927491 for pin connector to your BOM

smart home & co | Create at | 2026-02-03 | Drawn | carletz DOMIX - Domotic module for

Update at | 2026-02-09 | Reviewed | carletz

Schematic | M7 - Output Module
1 | A4 | | Board | M7 - OUTPUT | Page | Output

Version | Size | Page 2 Total 2
