carletz/DOMIX-Open-Source-Modular-Home-Automation-System/M5 - 12 RELAY/SCH_M5 - 12 Relay Module_2026-02-14.pdf

# PINOUT

# Domotic Module for smart home & co

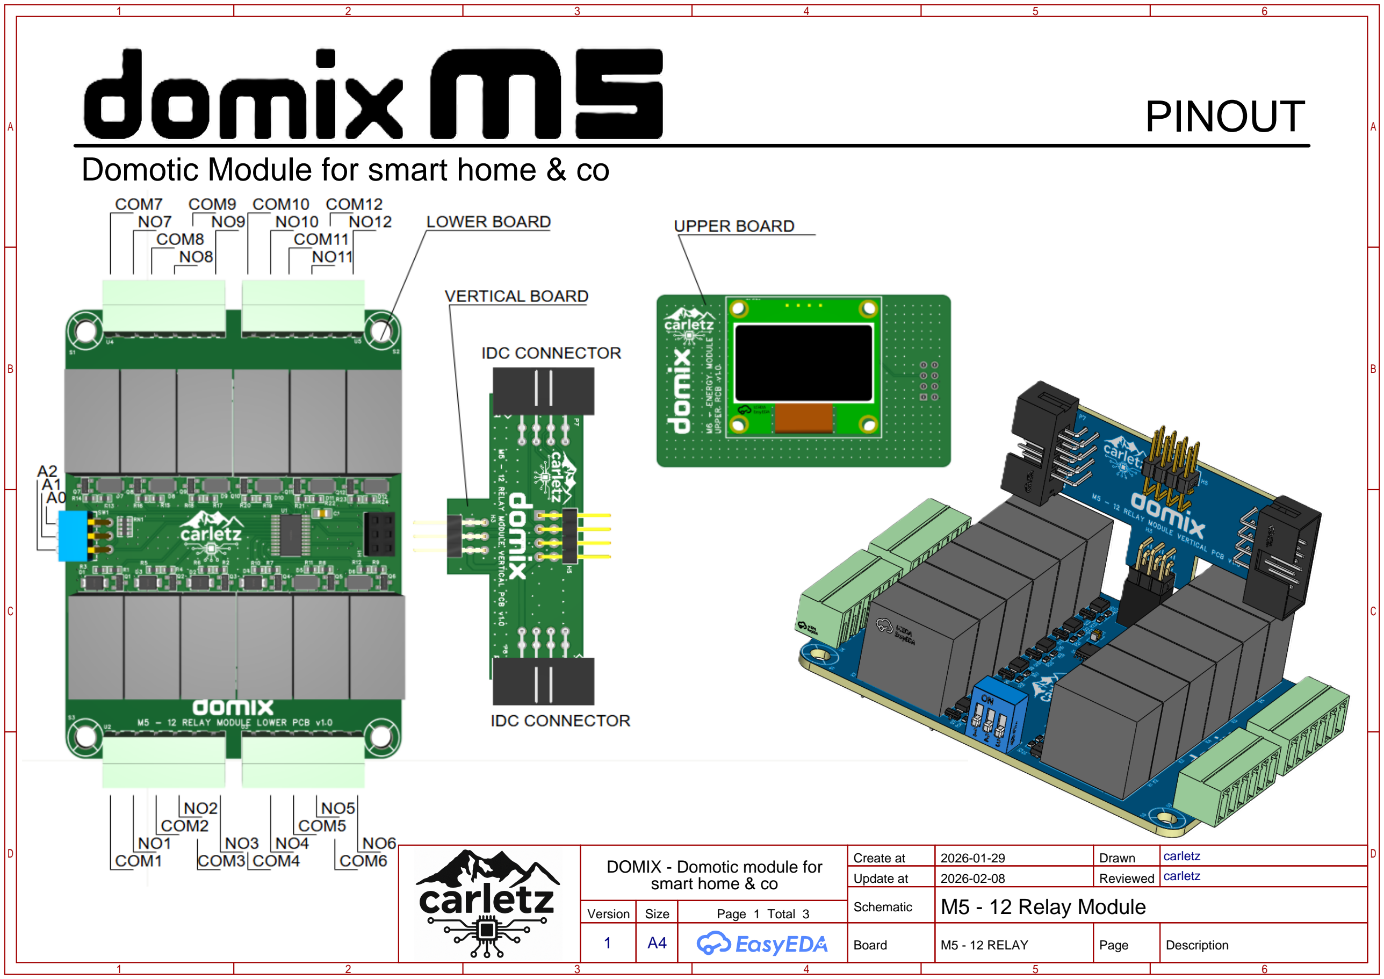
[picture p170: page 1]

smart home & co | Create at | 2026-01-29 | Drawn | carletz DOMIX - Domotic module for
| Update at | 2026-02-08 | Reviewed | carletz
| Schematic | M5 - 12 Relay Module
Version | Size | Page 1 Total 3
1 | A4 | | Board | M5 - 12 RELAY | Page | Description

I2C Controller | Connector & Miscellanea

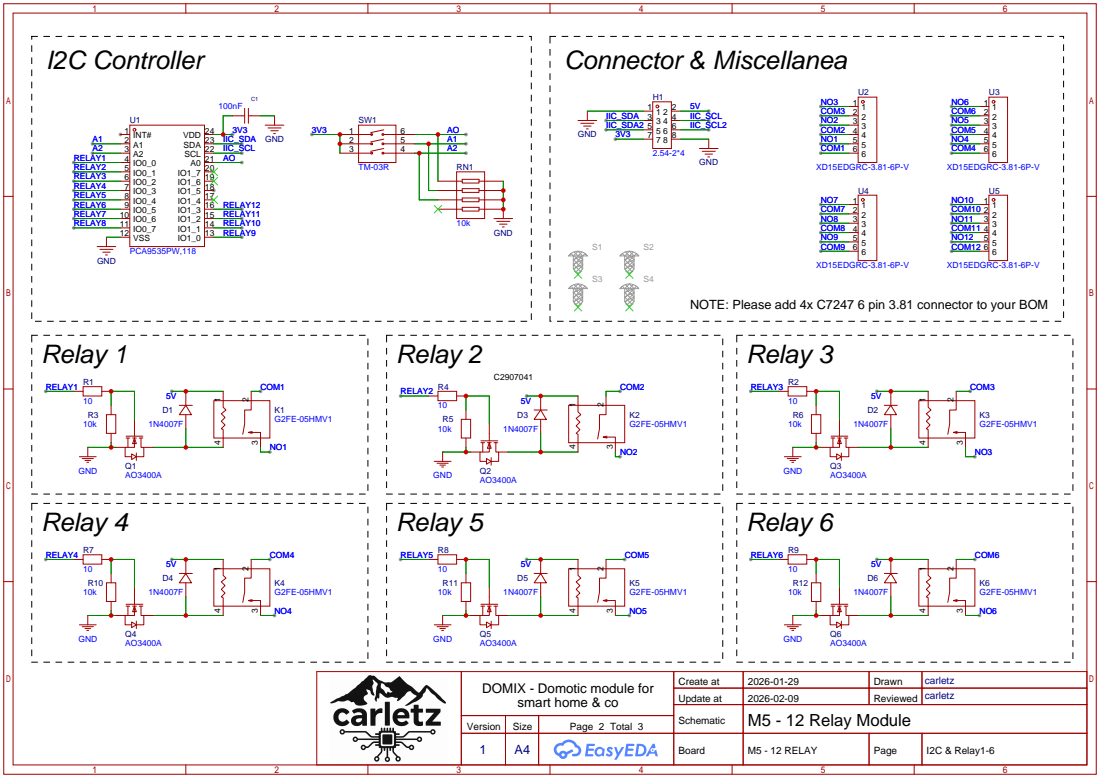
[picture p171: page 2]

NOTE: Please add 4x C7247 6 pin 3.81 connector to your BOM

smart home & co | Create at | 2026-01-29 | Drawn | carletz DOMIX - Domotic module for

Update at | 2026-02-09 | Reviewed | carletz

Schematic | M5 - 12 Relay Module

Version | Size | Page 2 Total 3

Board | M5 - 12 RELAY | Page | I2C & Relay1-6

# Relay 7

Relay 8 | Relay 9

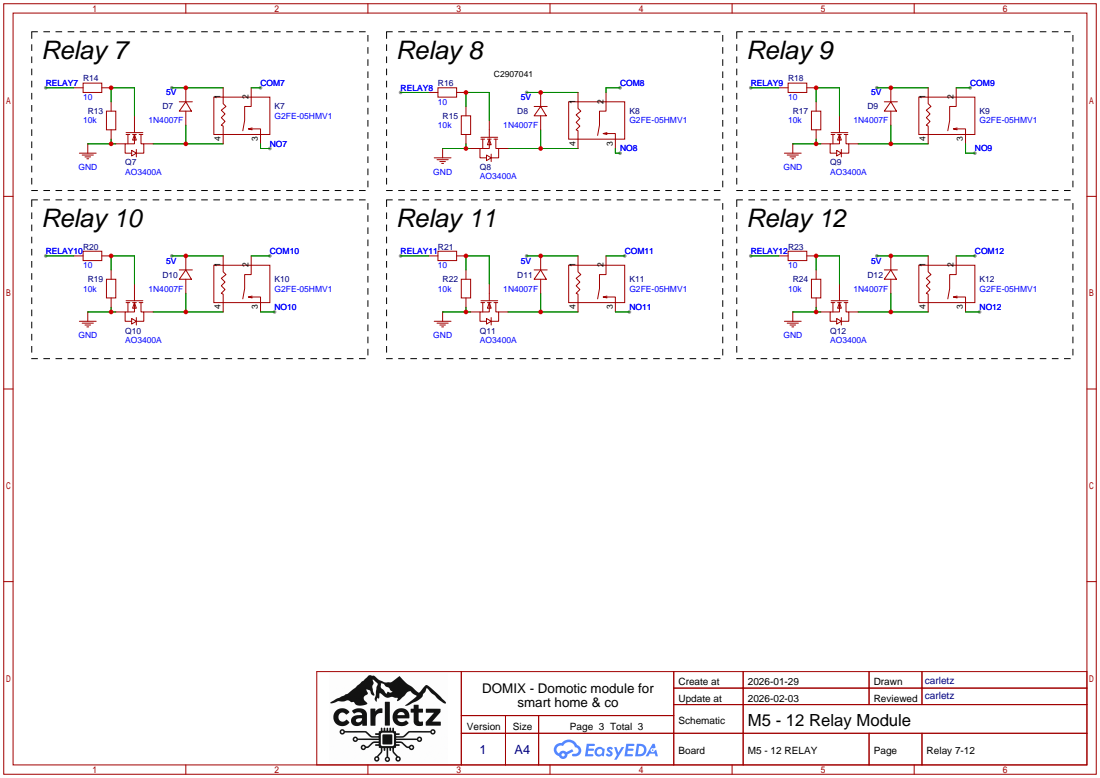
[picture p172: page 3]

smart home & co | Create at | 2026-01-29 | Drawn | carletz DOMIX - Domotic module for

Update at | 2026-02-03 | Reviewed | carletz

Schematic | M5 - 12 Relay Module

Version | Size | Page 3 Total 3

Board | M5 - 12 RELAY | Page | Relay 7-12
