carletz/DOMIX-Open-Source-Modular-Home-Automation-System/M6 - ENERGY/SCH_M5-6 - Display Module_2026-02-14.pdf

# Screen

# Connector

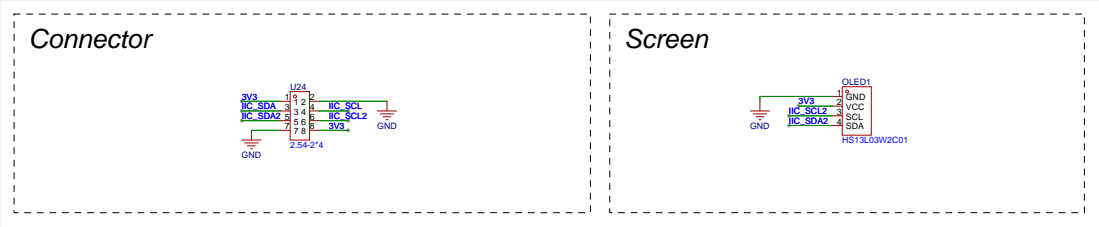
[picture p173: page 1]

smart home & co | Create at | 2026-01-29 | Drawn | carletz DOMIX - Domotic module for

Update at | 2026-02-03 | Reviewed | carletz

Schematic | M5-6 - Display Module
1 | A4 | | Board | U5-6 - MULTI - UPPER | Page | Board

Version | Size | Page 1 Total 1
