carletz/DOMIX-Open-Source-Modular-Home-Automation-System/M4 - 6 RELAY/SCH_M4 - 6 Relay Module_2026-02-14.pdf

# PINOUT

# Domotic Module for smart home & co

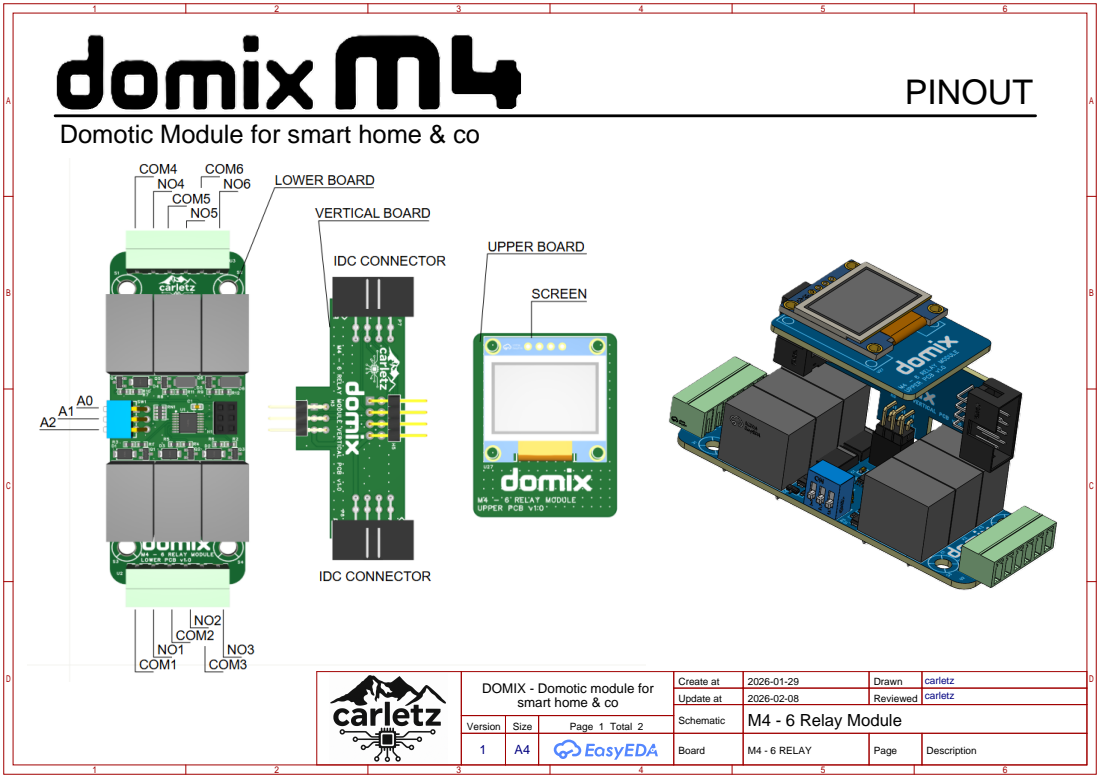
[picture p174: page 1]

smart home & co | Create at | 2026-01-29 | Drawn | carletz DOMIX - Domotic module for

Update at | 2026-02-08 | Reviewed | carletz

Schematic | M4 - 6 Relay Module
1 | A4 | | Board | M4 - 6 RELAY | Page | Description

Version | Size | Page 1 Total 2

I2C Controller | Connector & Miscellanea

# IO5 10 IO6 11 IO7 12 INT# 13 SCL 14 SDA 15 VDD 16

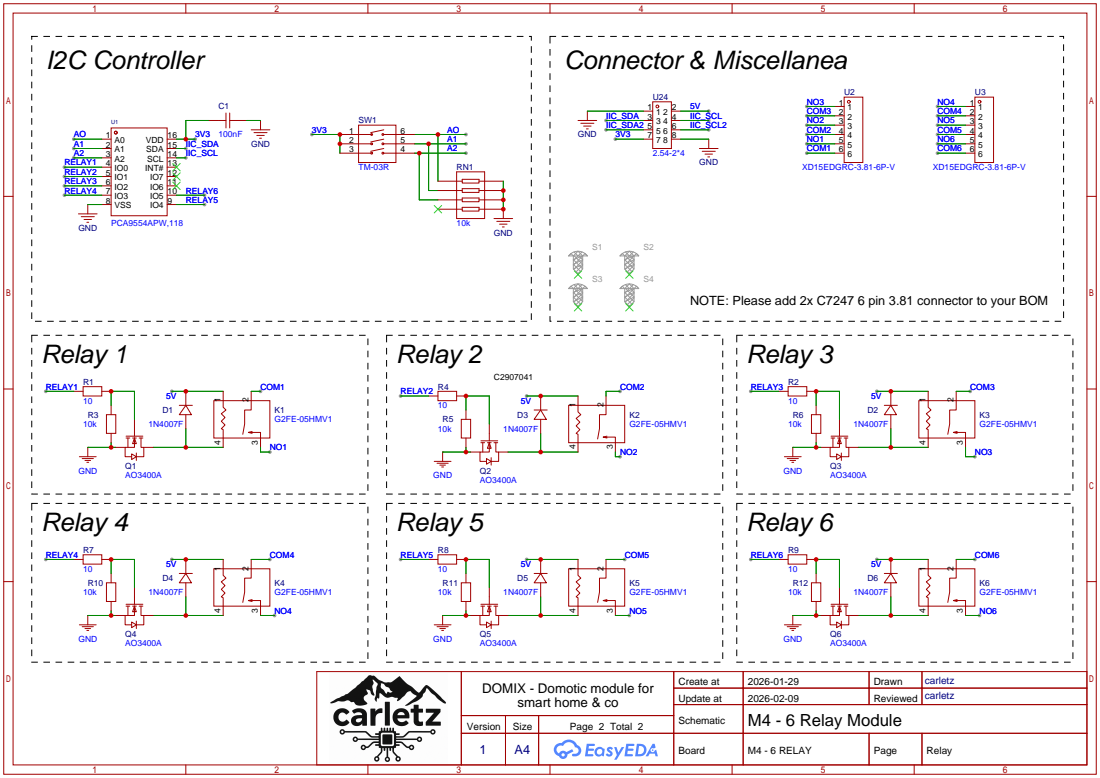
[picture p175: page 2]

NOTE: Please add 2x C7247 6 pin 3.81 connector to your BOM

smart home & co | Create at | 2026-01-29 | Drawn | carletz DOMIX - Domotic module for

Update at | 2026-02-09 | Reviewed | carletz

Schematic | M4 - 6 Relay Module
1 | A4 | | Board | M4 - 6 RELAY | Page | Relay

Version | Size | Page 2 Total 2
