carletz/DOMIX-Open-Source-Modular-Home-Automation-System/M4 - 6 RELAY/SCH_M3-4 - Display Module_2026-02-14.pdf

Connector | Screen

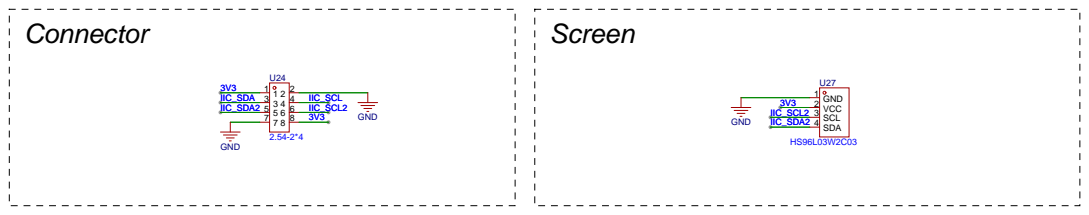
[picture p176: page 1]

smart home & co | Create at | 2026-01-29 | Drawn | carletz DOMIX - Domotic module for

Update at | 2026-02-03 | Reviewed | carletz

Schematic | M3-4 - Display Module
1 | A4 | | Board | U3-4 - MULTI - UPPER | Page | Board

Version | Size | Page 1 Total 1
