carletz/DOMIX-Open-Source-Modular-Home-Automation-System/M6 - ENERGY/SCH_M3-4-5-6 - Vertical Module_2026-02-14.pdf

# Connector

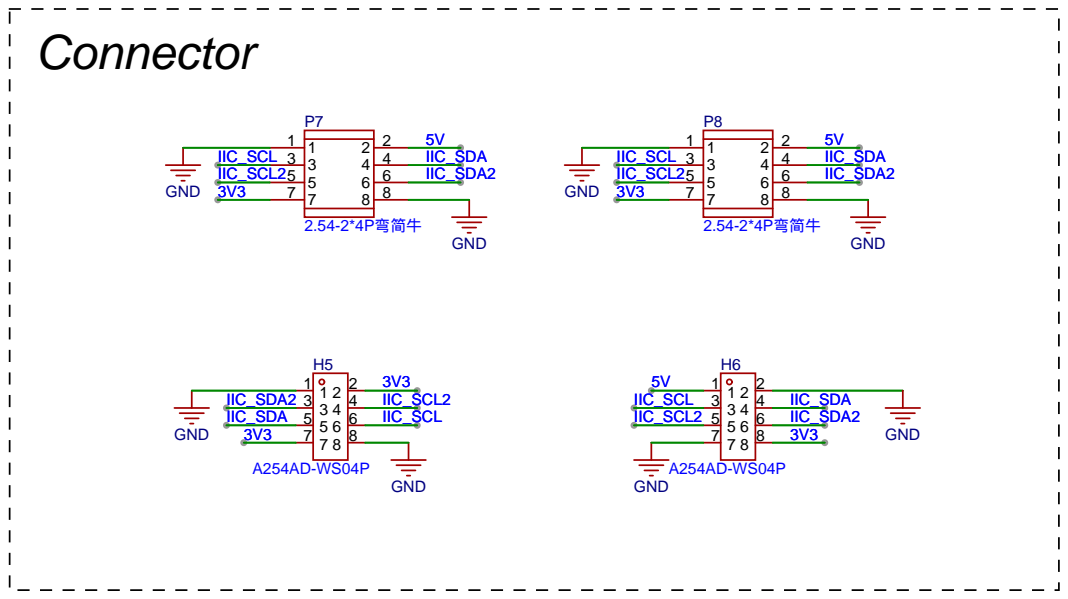
[picture p177: page 1]

smart home & co | Create at | 2026-01-29 | Drawn | carletz DOMIX - Domotic module for

Update at | 2026-02-03 | Reviewed | carletz

Schematic | M3-4-5-6 - Vertical Module
1 | A4 | | Board | V3-4-5-6 - MULTI -VERTICAL | Page | Connector

Version | Size | Page 1 Total 1
