carletz/DOMIX-Open-Source-Modular-Home-Automation-System/M2 - IO/SCH_M2 - Display Module_2026-02-14.pdf

# Led Indicator

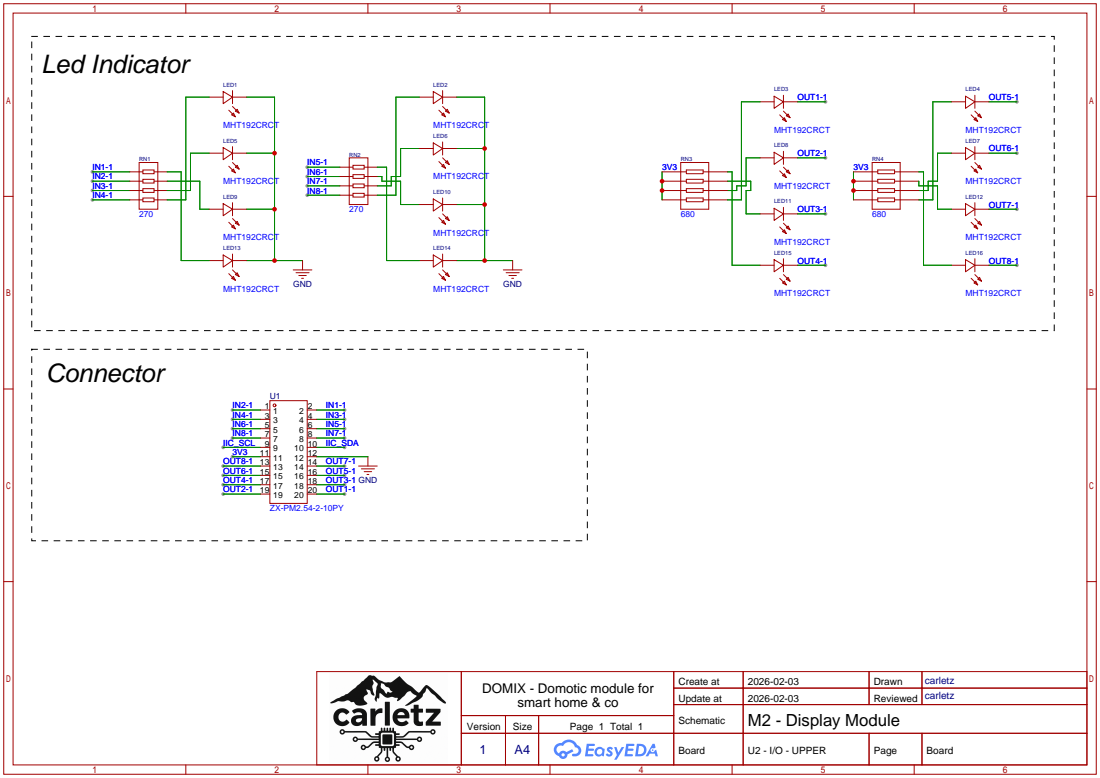
[picture p178: page 1]

smart home & co | Create at | 2026-02-03 | Drawn | carletz DOMIX - Domotic module for

Update at | 2026-02-03 | Reviewed | carletz

Schematic | M2 - Display Module
1 | A4 | | Board | U2 - I/O - UPPER | Page | Board

Version | Size | Page 1 Total 1
