carletz/DOMIX-Open-Source-Modular-Home-Automation-System/M1 - CORE V1.1/SCH_M1 - Core Module V1.1_2026-02-14.pdf

# PINOUT

# Domotic Module for smart home & co

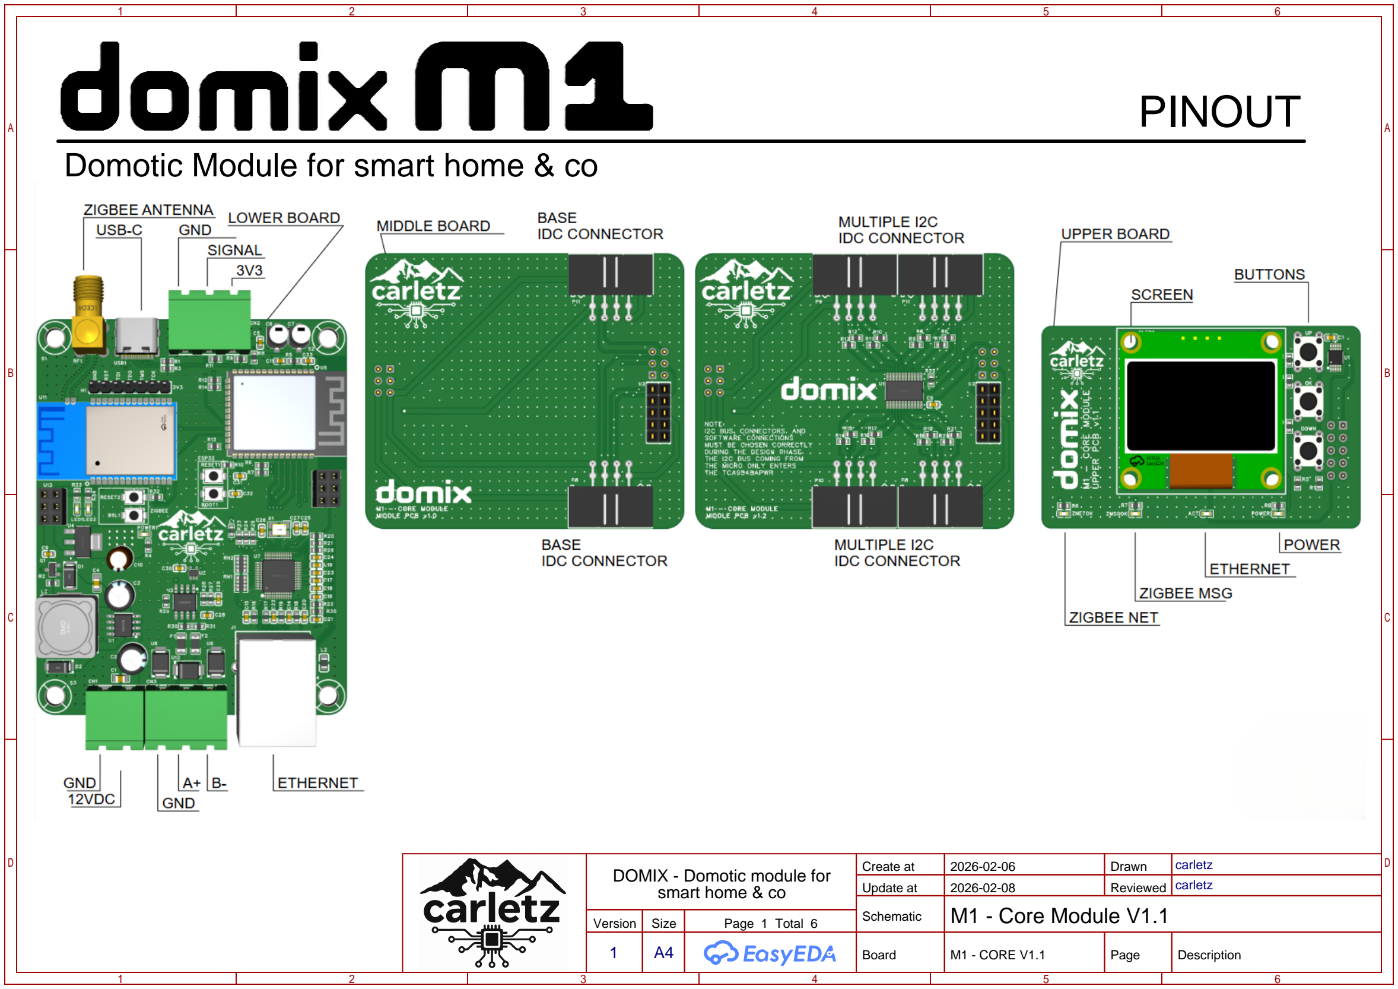
[picture p181: page 1]

smart home & co | Create at | 2026-02-06 | Drawn | carletz DOMIX - Domotic module for
| Update at | 2026-02-08 | Reviewed | carletz
| Schematic | M1 - Core Module V1.1
Version | Size | Page 1 Total 6
1 | A4 | | Board | M1 - CORE V1.1 | Page | Description

# VERSION

# Domotic Module for smart home & co

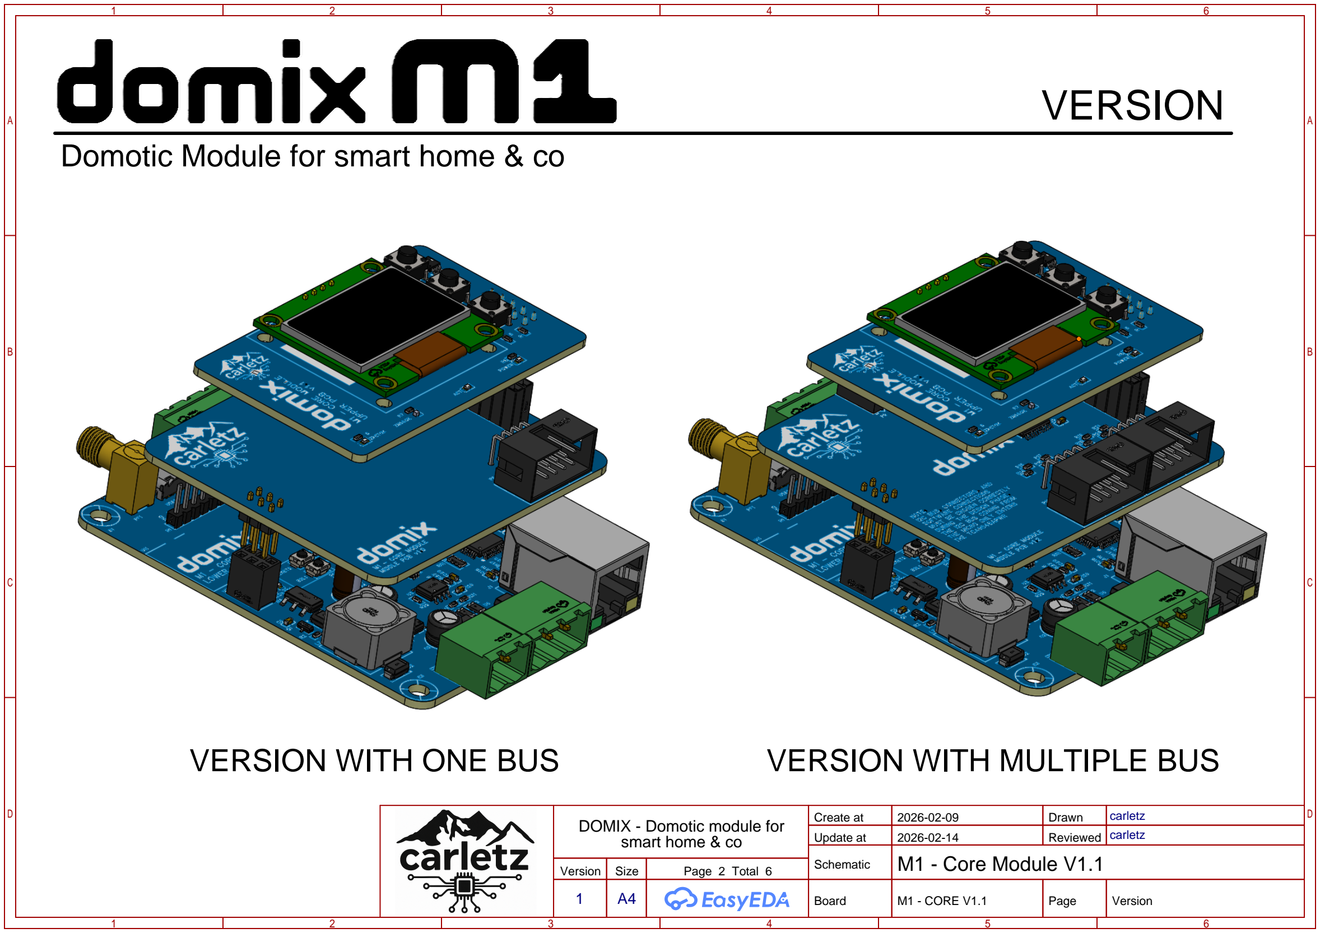
[picture p182: page 2]

smart home & co | Create at | 2026-02-09 | Drawn | carletz DOMIX - Domotic module for
| Update at | 2026-02-14 | Reviewed | carletz
| Schematic | M1 - Core Module V1.1
Version | Size | Page 2 Total 6
| | | Board | M1 - CORE V1.1 | Page | Version
VERSION WITH ONE BUS | VERSION WITH MULTIPLE BUS

# USB Board Power supply

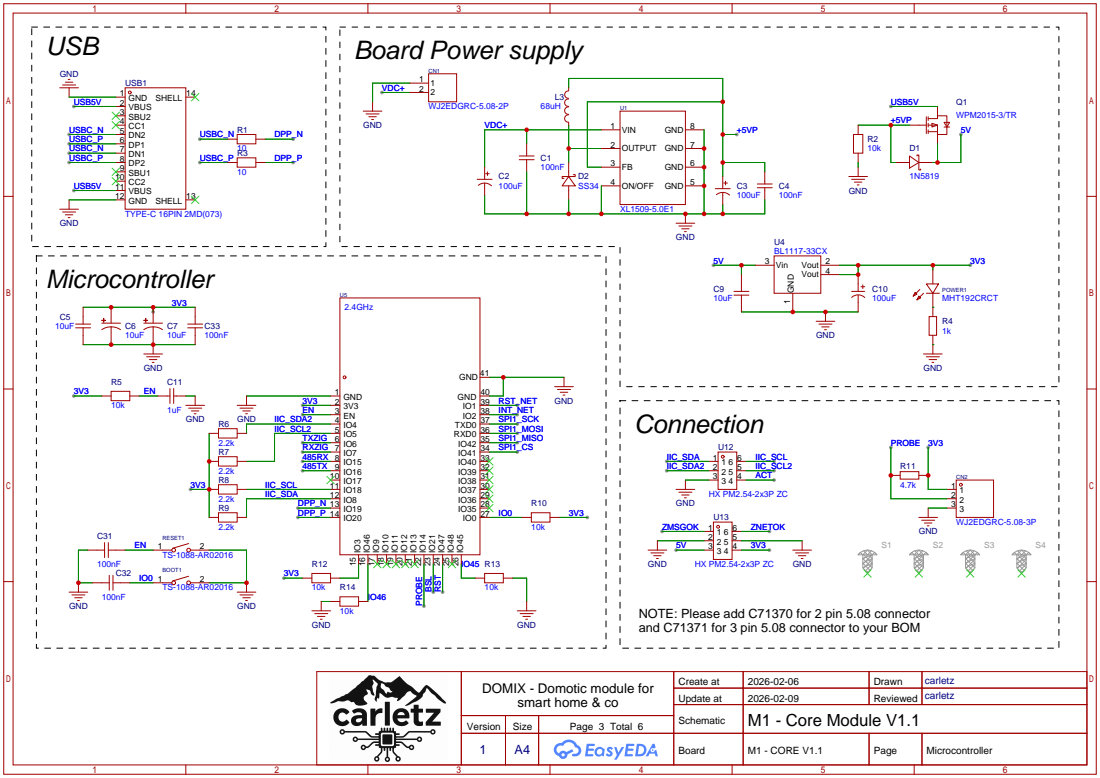
[picture p183: page 3]

NOTE: Please add C71370 for 2 pin 5.08 connector
and C71371 for 3 pin 5.08 connector to your BOM

smart home & co | Create at | 2026-02-06 | Drawn | carletz DOMIX - Domotic module for

Update at | 2026-02-09 | Reviewed | carletz

Schematic | M1 - Core Module V1.1

Version | Size | Page 3 Total 6

Board | M1 - CORE V1.1 | Page | Microcontroller

# Ethernet

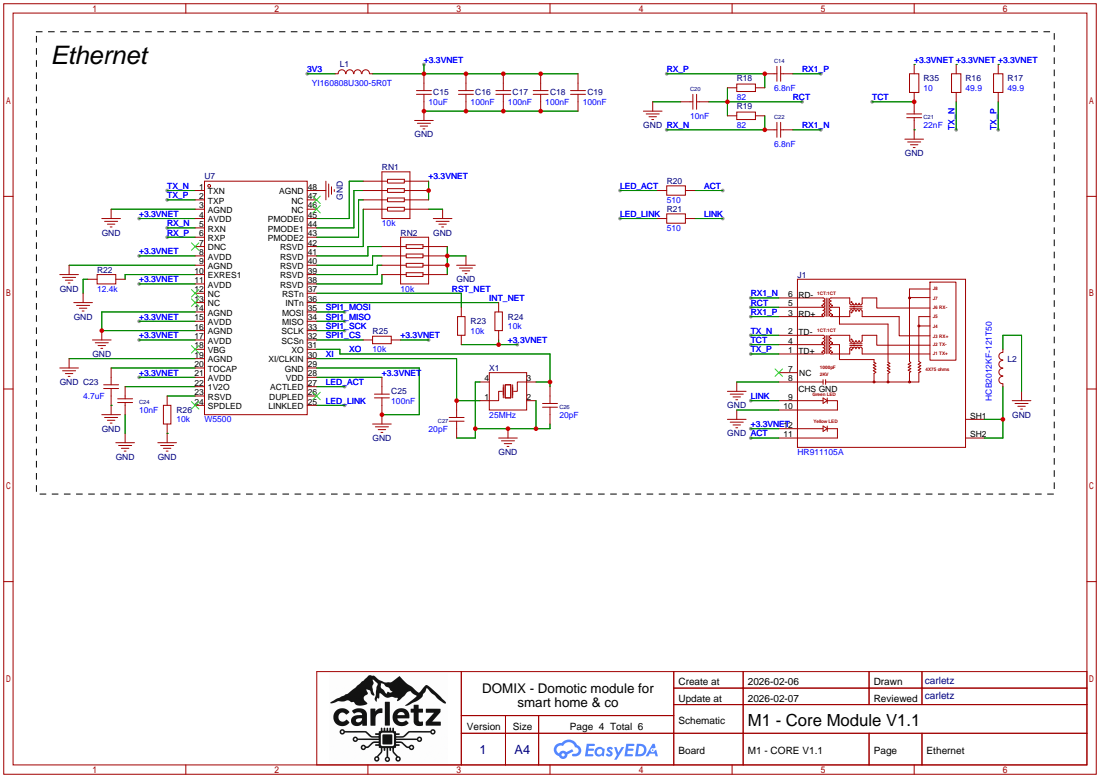
[picture p184: page 4]

smart home & co | Create at | 2026-02-06 | Drawn | carletz DOMIX - Domotic module for

Update at | 2026-02-07 | Reviewed | carletz

Schematic | M1 - Core Module V1.1

Version | Size | Page 4 Total 6

Board | M1 - CORE V1.1 | Page | Ethernet

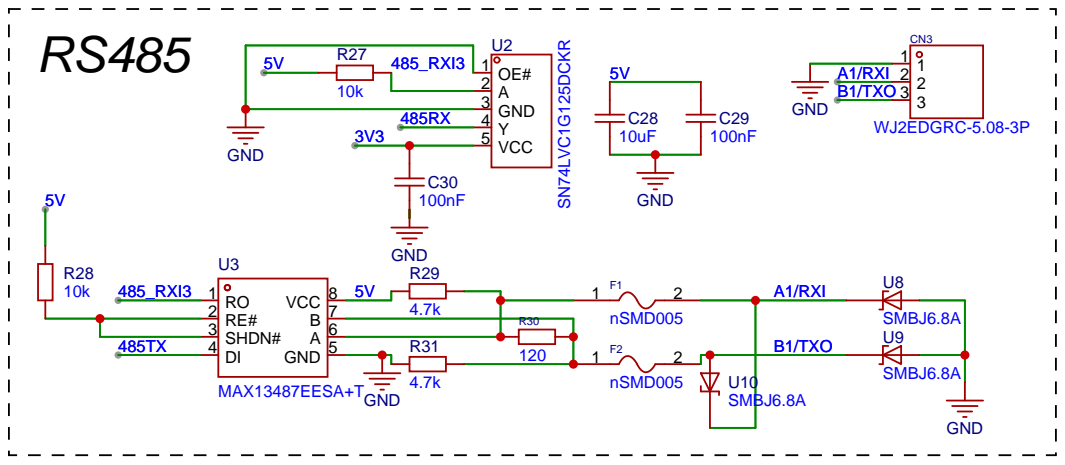
[picture p185: page 5]

smart home & co | Create at | 2026-02-06 | Drawn | carletz DOMIX - Domotic module for

Update at | 2026-02-09 | Reviewed | carletz

Schematic | M1 - Core Module V1.1

Version | Size | Page 5 Total 6

Board | M1 - CORE V1.1 | Page | RS485

# Zigbee

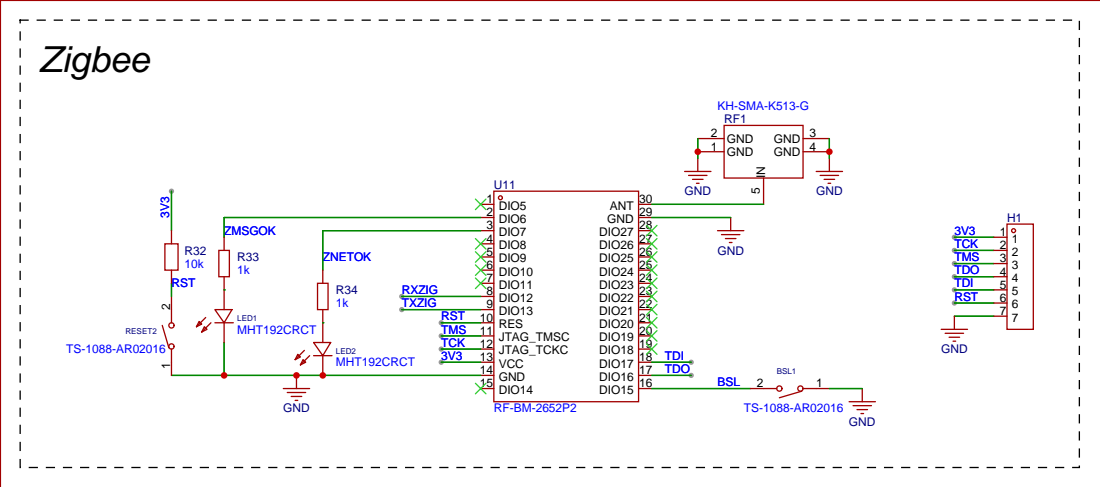
[picture p186: page 6]

smart home & co | Create at | 2026-02-06 | Drawn | carletz DOMIX - Domotic module for

Update at | 2026-02-09 | Reviewed | carletz

Schematic | M1 - Core Module V1.1

Version | Size | Page 6 Total 6

Board | M1 - CORE V1.1 | Page | Zigbee
