carletz/DOMIX-Open-Source-Modular-Home-Automation-System/Software/M/module/m6.yaml

# ============================================================================
#
# M6 MODULE BASIC DESIGN FOR BASIC FUNCTIONS
#
# Adapt the configurations, names and other to your needs
#
# ============================================================================
external_components:
  - source:
      type: git
      url: https://github.com/hzkincony/esphome-zmpt101b
    refresh: 1min

# PCA9554A I/O Expander (for multiplexing of CD74HC4067 chip channel S0-S3)
pca9554:
  - id: domix_m6${m6_number_1}_busi2c
    address: ${m6_i2c_1} 
    i2c_id: ${m6_i2c_id}              # Bus for comunication with DOMIX M1 module    

# ADS1115 ADC
ads1115:
  - id: domix_m6${m6_number_1}_ads1115_hub
    address: ${m6_ads_1} 
    continuous_mode: off
    i2c_id: ${m6_i2c_id}              # Bus for comunication with DOMIX M1 module

# Configurazione multiplexer CD74HC4067
cd74hc4067:
  - id: m6${m6_number_1}_mux
    delay: 15ms
    pin_s0:
      pca9554: domix_m6${m6_number_1}_busi2c
      number: 3
      mode: OUTPUT
      inverted: false
    pin_s1:
      pca9554: domix_m6${m6_number_1}_busi2c
      number: 2
      mode: OUTPUT
      inverted: false
    pin_s2:
      pca9554: domix_m6${m6_number_1}_busi2c
      number: 1
      mode: OUTPUT
      inverted: false
    pin_s3:
      pca9554: domix_m6${m6_number_1}_busi2c
      number: 0
      mode: OUTPUT
      inverted: false

sensor:
  - platform: ads1115
    multiplexer: 'A0_GND'
    gain: 1.024
    id: domix_m6${m6_number_1}_voltage
    ads1115_id: domix_m6${m6_number_1}_ads1115_hub
    internal: true
    update_interval: never

  - platform: zmpt101b
    name: "${m6_voltage_description}"
    sensor: domix_m6${m6_number_1}_voltage
    id: voltage${m6_number_1}
    sensitivity: 538                    # new_sensitivity = current_sensitivity × (actual_voltage / measured_voltage)
    unit_of_measurement: V
    accuracy_decimals: 1
    qos: 1
    retain: true
    state_topic: ${mqtt_name}/${m6_name}${m6_number_1}/${m6_voltage_description}/state
    web_server:
      sorting_group_id: domix_m6_web
      sorting_weight: 1

  - platform: ads1115
    multiplexer: 'A1_GND'
    gain: 1.024
    id: domix_m6${m6_number_1}_clamp_ch0
    ads1115_id: domix_m6${m6_number_1}_ads1115_hub
    internal: true
    update_interval: never

  - platform: cd74hc4067
    id: clamp_ch4_m6${m6_number_1}
    number: 0
    sensor: domix_m6${m6_number_1}_clamp_ch0
    cd74hc4067_id: m6${m6_number_1}_mux
    update_interval: 60s

  - platform: cd74hc4067
    id: clamp_ch3_m6${m6_number_1}
    number: 1
    sensor: domix_m6${m6_number_1}_clamp_ch0
    cd74hc4067_id: m6${m6_number_1}_mux    
    update_interval: 60s

  - platform: cd74hc4067
    id: clamp_ch2_m6${m6_number_1}
    number: 2
    sensor: domix_m6${m6_number_1}_clamp_ch0
    cd74hc4067_id: m6${m6_number_1}_mux    
    update_interval: 60s

  - platform: cd74hc4067
    id: clamp_ch1_m6${m6_number_1}
    number: 3
    sensor: domix_m6${m6_number_1}_clamp_ch0
    cd74hc4067_id: m6${m6_number_1}_mux    
    update_interval: 60s

  - platform: cd74hc4067
    id: clamp_ch8_m6${m6_number_1}
    number: 4
    sensor: domix_m6${m6_number_1}_clamp_ch0
    cd74hc4067_id: m6${m6_number_1}_mux    
    update_interval: 60s

  - platform: cd74hc4067
    id: clamp_ch7_m6${m6_number_1}
    number: 5
    sensor: domix_m6${m6_number_1}_clamp_ch0
    cd74hc4067_id: m6${m6_number_1}_mux    
    update_interval: 60s

  - platform: cd74hc4067
    id: clamp_ch6_m6${m6_number_1}
    number: 6
    sensor: domix_m6${m6_number_1}_clamp_ch0
    cd74hc4067_id: m6${m6_number_1}_mux    
    update_interval: 60s

  - platform: cd74hc4067
    id: clamp_ch5_m6${m6_number_1}
    number: 7
    sensor: domix_m6${m6_number_1}_clamp_ch0
    cd74hc4067_id: m6${m6_number_1}_mux    
    update_interval: 60s

  - platform: cd74hc4067
    id: clamp_ch9_m6${m6_number_1}
    number: 8
    sensor: domix_m6${m6_number_1}_clamp_ch0
    cd74hc4067_id: m6${m6_number_1}_mux    
    update_interval: 60s

  - platform: cd74hc4067
    id: clamp_ch10_m6${m6_number_1}
    number: 9
    sensor: domix_m6${m6_number_1}_clamp_ch0
    cd74hc4067_id: m6${m6_number_1}_mux    
    update_interval: 60s

  - platform: ct_clamp
    sensor: clamp_ch1_m6${m6_number_1}
    id: measured_current_m6${m6_number_1}_clamp_1
    name: "Current ${m6_channel_description} 1"
    icon: "mdi:electric_meter"
    update_interval: 5s
    filters:
      - calibrate_linear:
          # Measured value of 0 maps to 0A
          - 0.0034 -> 0
          # Known load: 4.0A
          # Value shown in logs: 0.1333A
          - 0.31749 -> 8.95608
    qos: 1
    retain: true
    availability:
      topic: ${mqtt_name}/${m6_name}${m6_number_1}/${m6_channel_description} 1
      payload_available: online
      payload_not_available: offline
    state_topic: ${mqtt_name}/${m6_name}${m6_number_1}/${m6_channel_description} 1/Current/state
    web_server:
      sorting_group_id: domix_m6_web
      sorting_weight: 2

  - platform: ct_clamp
    sensor: clamp_ch2_m6${m6_number_1}
    id: measured_current_m6${m6_number_1}_clamp_2
    name: "Current ${m6_channel_description} 2"
    icon: "mdi:electric_meter"
    update_interval: 5s
    filters:
      - calibrate_linear:
          # Measured value of 0 maps to 0A
          - 0.0034 -> 0
          # Known load: 4.0A
          # Value shown in logs: 0.1333A
          - 0.31749 -> 8.95608
    qos: 1
    retain: true
    availability:
      topic: ${mqtt_name}/${m6_name}${m6_number_1}/${m6_channel_description} 2
      payload_available: online
      payload_not_available: offline
    state_topic: ${mqtt_name}/${m6_name}${m6_number_1}/${m6_channel_description} 2/Current/state
    web_server:
      sorting_group_id: domix_m6_web
      sorting_weight: 3

  - platform: ct_clamp
    sensor: clamp_ch3_m6${m6_number_1}
    id: measured_current_m6${m6_number_1}_clamp_3
    name: "Current ${m6_channel_description} 3"
    icon: "mdi:electric_meter"
    update_interval: 5s
    filters:
      - calibrate_linear:
          # Measured value of 0 maps to 0A
          - 0.0034 -> 0
          # Known load: 4.0A
          # Value shown in logs: 0.1333A
          - 0.31749 -> 8.95608
    qos: 1
    retain: true
    availability:
      topic: ${mqtt_name}/${m6_name}${m6_number_1}/${m6_channel_description} 3
      payload_available: online
      payload_not_available: offline
    state_topic: ${mqtt_name}/${m6_name}${m6_number_1}/${m6_channel_description} 3/Current/state
    web_server:
      sorting_group_id: domix_m6_web
      sorting_weight: 4

  - platform: ct_clamp
    sensor: clamp_ch4_m6${m6_number_1}
    id: measured_current_m6${m6_number_1}_clamp_4
    name: "Current ${m6_channel_description} 4"
    icon: "mdi:electric_meter"
    update_interval: 5s
    filters:
      - calibrate_linear:
          # Measured value of 0 maps to 0A
          - 0.0034 -> 0
          # Known load: 4.0A
          # Value shown in logs: 0.1333A
          - 0.31749 -> 8.95608
    qos: 1
    retain: true
    availability:
      topic: ${mqtt_name}/${m6_name}${m6_number_1}/${m6_channel_description} 4
      payload_available: online
      payload_not_available: offline
    state_topic: ${mqtt_name}/${m6_name}${m6_number_1}/${m6_channel_description} 4/Current/state
    web_server:
      sorting_group_id: domix_m6_web
      sorting_weight: 5

  - platform: ct_clamp
    sensor: clamp_ch5_m6${m6_number_1}
    id: measured_current_m6${m6_number_1}_clamp_5
    name: "Current ${m6_channel_description} 5"
    icon: "mdi:electric_meter"
    update_interval: 5s
    filters:
      - calibrate_linear:
          # Measured value of 0 maps to 0A
          - 0.0034 -> 0
          # Known load: 4.0A
          # Value shown in logs: 0.1333A
          - 0.31749 -> 8.95608
    qos: 1
    retain: true
    availability:
      topic: ${mqtt_name}/${m6_name}${m6_number_1}/${m6_channel_description} 5
      payload_available: online
      payload_not_available: offline
    state_topic: ${mqtt_name}/${m6_name}${m6_number_1}/${m6_channel_description} 5/Current/state
    web_server:
      sorting_group_id: domix_m6_web
      sorting_weight: 6

  - platform: ct_clamp
    sensor: clamp_ch6_m6${m6_number_1}
    id: measured_current_m6${m6_number_1}_clamp_6
    name: "Current ${m6_channel_description} 6"
    icon: "mdi:electric_meter"
    update_interval: 5s
    filters:
      - calibrate_linear:
          # Measured value of 0 maps to 0A
          - 0.0034 -> 0
          # Known load: 4.0A
          # Value shown in logs: 0.1333A
          - 0.31749 -> 8.95608
    qos: 1
    retain: true
    availability:
      topic: ${mqtt_name}/${m6_name}${m6_number_1}/${m6_channel_description} 6
      payload_available: online
      payload_not_available: offline
    state_topic: ${mqtt_name}/${m6_name}${m6_number_1}/${m6_channel_description} 6/Current/state
    web_server:
      sorting_group_id: domix_m6_web
      sorting_weight: 7

  - platform: ct_clamp
    sensor: clamp_ch7_m6${m6_number_1}
    id: measured_current_m6${m6_number_1}_clamp_7
    name: "Current ${m6_channel_description} 7"
    icon: "mdi:electric_meter"
    update_interval: 5s
    filters:
      - calibrate_linear:
          # Measured value of 0 maps to 0A
          - 0.0034 -> 0
          # Known load: 4.0A
          # Value shown in logs: 0.1333A
          - 0.31749 -> 8.95608
    qos: 1
    retain: true
    availability:
      topic: ${mqtt_name}/${m6_name}${m6_number_1}/${m6_channel_description} 7
      payload_available: online
      payload_not_available: offline
    state_topic: ${mqtt_name}/${m6_name}${m6_number_1}/${m6_channel_description} 7/Current/state
    web_server:
      sorting_group_id: domix_m6_web
      sorting_weight: 8

  - platform: ct_clamp
    sensor: clamp_ch8_m6${m6_number_1}
    id: measured_current_m6${m6_number_1}_clamp_8
    name: "Current ${m6_channel_description} 8"
    icon: "mdi:electric_meter"
    update_interval: 5s
    filters:
      - calibrate_linear:
          # Measured value of 0 maps to 0A
          - 0.0034 -> 0
          # Known load: 4.0A
          # Value shown in logs: 0.1333A
          - 0.31749 -> 8.95608
    qos: 1
    retain: true
    availability:
      topic: ${mqtt_name}/${m6_name}${m6_number_1}/${m6_channel_description} 8
      payload_available: online
      payload_not_available: offline
    state_topic: ${mqtt_name}/${m6_name}${m6_number_1}/${m6_channel_description} 8/Current/state
    web_server:
      sorting_group_id: domix_m6_web  
      sorting_weight: 9

  - platform: ct_clamp
    sensor: clamp_ch9_m6${m6_number_1}
    id: measured_current_m6${m6_number_1}_clamp_9
    name: "Current ${m6_channel_description} 9"
    icon: "mdi:electric_meter"
    update_interval: 5s
    filters:
      - calibrate_linear:
          # Measured value of 0 maps to 0A
          - 0.0034 -> 0
          # Known load: 4.0A
          # Value shown in logs: 0.1333A
          - 0.31749 -> 8.95608
    qos: 1
    retain: true
    availability:
      topic: ${mqtt_name}/${m6_name}${m6_number_1}/${m6_channel_description} 9
      payload_available: online
      payload_not_available: offline
    state_topic: ${mqtt_name}/${m6_name}${m6_number_1}/${m6_channel_description} 9/Current/state
    web_server:
      sorting_group_id: domix_m6_web
      sorting_weight: 10

  - platform: ct_clamp
    sensor: clamp_ch10_m6${m6_number_1}
    id: measured_current_m6${m6_number_1}_clamp_10
    name: "Current ${m6_channel_description} 10"
    icon: "mdi:electric_meter"
    update_interval: 5s
    filters:
      - calibrate_linear:
          # Measured value of 0 maps to 0A
          - 0.0034 -> 0
          # Known load: 4.0A
          # Value shown in logs: 0.1333A
          - 0.31749 -> 8.95608
    qos: 1
    retain: true
    availability:
      topic: ${mqtt_name}/${m6_name}${m6_number_1}/${m6_channel_description} 10
      payload_available: online
      payload_not_available: offline
    state_topic: ${mqtt_name}/${m6_name}${m6_number_1}/${m6_channel_description} 10/Current/state
    web_server:
      sorting_group_id: domix_m6_web
      sorting_weight: 11

  - platform: template
    id: ${m6_name}${m6_number_1}_power_1
    name: "Power consumption ${m6_channel_description} 1"
    icon: "mdi:electric-meter"
    lambda: return id(measured_current_m6${m6_number_1}_clamp_1).state * id(voltage${m6_number_1}).state;
    device_class: power
    unit_of_measurement: 'W'
    update_interval: 60s
    qos: 1
    retain: true
    state_topic: ${mqtt_name}/${m6_name}${m6_number_1}/${m6_channel_description} 1/Power consumption/state
    web_server:
      sorting_group_id: domix_m6_web
      sorting_weight: 12

  - platform: template
    id: ${m6_name}${m6_number_1}_power_2
    name: "Power consumption ${m6_channel_description} 2"
    icon: "mdi:electric-meter"
    lambda: return id(measured_current_m6${m6_number_1}_clamp_2).state * id(voltage${m6_number_1}).state;
    device_class: power
    unit_of_measurement: 'W'
    update_interval: 60s
    qos: 1
    retain: true
    state_topic: ${mqtt_name}/${m6_name}${m6_number_1}/${m6_channel_description} 2/Power consumption/state
    web_server:
      sorting_group_id: domix_m6_web
      sorting_weight: 13

  - platform: template
    id: ${m6_name}${m6_number_1}_power_3
    name: "Power consumption ${m6_channel_description} 3"
    icon: "mdi:electric-meter"
    lambda: return id(measured_current_m6${m6_number_1}_clamp_3).state * id(voltage${m6_number_1}).state;
    device_class: power
    unit_of_measurement: 'W'
    update_interval: 60s
    qos: 1
    retain: true
    state_topic: ${mqtt_name}/${m6_name}${m6_number_1}/${m6_channel_description} 3/Power consumption/state
    web_server:
      sorting_group_id: domix_m6_web
      sorting_weight: 14

  - platform: template
    id: ${m6_name}${m6_number_1}_power_4
    name: "Power consumption ${m6_channel_description} 4"    
    icon: "mdi:electric-meter"       
    lambda: return id(measured_current_m6${m6_number_1}_clamp_4).state * id(voltage${m6_number_1}).state;
    device_class: power
    unit_of_measurement: 'W'
    update_interval: 60s
    qos: 1
    retain: true
    state_topic: ${mqtt_name}/${m6_name}${m6_number_1}/${m6_channel_description} 4/Power consumption/state
    web_server:
      sorting_group_id: domix_m6_web
      sorting_weight: 15

  - platform: template
    id: ${m6_name}${m6_number_1}_power_5
    name: "Power consumption ${m6_channel_description} 5"
    icon: "mdi:electric-meter"
    lambda: return id(measured_current_m6${m6_number_1}_clamp_5).state * id(voltage${m6_number_1}).state;
    device_class: power
    unit_of_measurement: 'W'
    update_interval: 60s
    qos: 1
    retain: true
    state_topic: ${mqtt_name}/${m6_name}${m6_number_1}/${m6_channel_description} 5/Power consumption/state
    web_server:
      sorting_group_id: domix_m6_web
      sorting_weight: 16

  - platform: template
    id: ${m6_name}${m6_number_1}_power_6
    name: "Power consumption ${m6_channel_description} 6"
    icon: "mdi:electric-meter"
    lambda: return id(measured_current_m6${m6_number_1}_clamp_6).state * id(voltage${m6_number_1}).state;
    device_class: power
    unit_of_measurement: 'W'
    update_interval: 60s
    qos: 1
    retain: true
    state_topic: ${mqtt_name}/${m6_name}${m6_number_1}/${m6_channel_description} 6/Power consumption/state
    web_server:
      sorting_group_id: domix_m6_web
      sorting_weight: 17

  - platform: template
    id: ${m6_name}${m6_number_1}_power_7
    name: "Power consumption ${m6_channel_description} 7"
    icon: "mdi:electric-meter"
    lambda: return id(measured_current_m6${m6_number_1}_clamp_7).state * id(voltage${m6_number_1}).state;
    device_class: power
    unit_of_measurement: 'W'
    update_interval: 60s
    qos: 1
    retain: true
    state_topic: ${mqtt_name}/${m6_name}${m6_number_1}/${m6_channel_description} 7/Power consumption/state
    web_server:
      sorting_group_id: domix_m6_web
      sorting_weight: 18

  - platform: template
    id: ${m6_name}${m6_number_1}_power_8
    name: "Power consumption ${m6_channel_description} 8"
    icon: "mdi:electric-meter"
    lambda: return id(measured_current_m6${m6_number_1}_clamp_8).state * id(voltage${m6_number_1}).state;
    device_class: power
    unit_of_measurement: 'W'
    update_interval: 60s
    qos: 1
    retain: true
    state_topic: ${mqtt_name}/${m6_name}${m6_number_1}/${m6_channel_description} 8/Power consumption/state
    web_server:
      sorting_group_id: domix_m6_web
      sorting_weight: 19

  - platform: template
    id: ${m6_name}${m6_number_1}_power_9
    name: "Power consumption ${m6_channel_description} 9"
    icon: "mdi:electric-meter"
    lambda: return id(measured_current_m6${m6_number_1}_clamp_9).state * id(voltage${m6_number_1}).state;
    device_class: power
    unit_of_measurement: 'W'
    update_interval: 60s
    qos: 1
    retain: true
    state_topic: ${mqtt_name}/${m6_name}${m6_number_1}/${m6_channel_description} 9/Power consumption/state
    web_server:
      sorting_group_id: domix_m6_web
      sorting_weight: 20

  - platform: template
    id: ${m6_name}${m6_number_1}_power_10
    name: "Power consumption ${m6_channel_description} 10"
    icon: "mdi:electric-meter"
    lambda: return id(measured_current_m6${m6_number_1}_clamp_10).state * id(voltage${m6_number_1}).state;
    device_class: power
    unit_of_measurement: 'W'
    update_interval: 60s
    qos: 1
    retain: true
    state_topic: ${mqtt_name}/${m6_name}${m6_number_1}/${m6_channel_description} 10/Power consumption/state
    web_server:
      sorting_group_id: domix_m6_web
      sorting_weight: 21

  - platform: total_daily_energy
    name: "Total Daily Energy ${m6_channel_description} 1"
    power_id: ${m6_name}${m6_number_1}_power_1
    icon: "mdi:whatshot"
    filters:
        - multiply: 0.001
    unit_of_measurement: kWh
    accuracy_decimals: 3
    device_class: energy
    qos: 1
    retain: true
    state_topic: ${mqtt_name}/${m6_name}${m6_number_1}/${m6_channel_description} 1/Total Daily Energy/state
    web_server:
      sorting_group_id: domix_m6_web
      sorting_weight: 22

  - platform: total_daily_energy
    name: "Total Daily Energy ${m6_channel_description} 2"
    power_id: ${m6_name}${m6_number_1}_power_2
    icon: "mdi:whatshot"
    filters:
        - multiply: 0.001
    unit_of_measurement: kWh
    accuracy_decimals: 3
    device_class: energy
    qos: 1
    retain: true
    state_topic: ${mqtt_name}/${m6_name}${m6_number_1}/${m6_channel_description} 2/Total Daily Energy/state
    web_server:
      sorting_group_id: domix_m6_web
      sorting_weight: 23

  - platform: total_daily_energy
    name: "Total Daily Energy ${m6_channel_description} 3"
    power_id: ${m6_name}${m6_number_1}_power_3
    icon: "mdi:whatshot"
    filters:
        - multiply: 0.001
    unit_of_measurement: kWh
    accuracy_decimals: 3
    device_class: energy
    qos: 1
    retain: true
    state_topic: ${mqtt_name}/${m6_name}${m6_number_1}/${m6_channel_description} 3/Total Daily Energy/state
    web_server:
      sorting_group_id: domix_m6_web     
      sorting_weight: 24
      
  - platform: total_daily_energy
    name: "Total Daily Energy ${m6_channel_description} 4"
    power_id: ${m6_name}${m6_number_1}_power_4
    icon: "mdi:whatshot"
    filters:
        - multiply: 0.001
    unit_of_measurement: kWh
    accuracy_decimals: 3
    device_class: energy
    qos: 1
    retain: true
    state_topic: ${mqtt_name}/${m6_name}${m6_number_1}/${m6_channel_description} 4/Total Daily Energy/state
    web_server:
      sorting_group_id: domix_m6_web
      sorting_weight: 25

  - platform: total_daily_energy
    name: "Total Daily Energy ${m6_channel_description} 5"
    power_id: ${m6_name}${m6_number_1}_power_5
    icon: "mdi:whatshot"
    filters:
        - multiply: 0.001
    unit_of_measurement: kWh
    accuracy_decimals: 3
    device_class: energy
    qos: 1
    retain: true
    state_topic: ${mqtt_name}/${m6_name}${m6_number_1}/${m6_channel_description} 5/Total Daily Energy/state
    web_server:
      sorting_group_id: domix_m6_web   
      sorting_weight: 26   

  - platform: total_daily_energy
    name: "Total Daily Energy ${m6_channel_description} 6"
    power_id: ${m6_name}${m6_number_1}_power_6
    icon: "mdi:whatshot"
    filters:
        - multiply: 0.001
    unit_of_measurement: kWh
    accuracy_decimals: 3
    device_class: energy
    qos: 1
    retain: true
    state_topic: ${mqtt_name}/${m6_name}${m6_number_1}/${m6_channel_description} 6/Total Daily Energy/state
    web_server:
      sorting_group_id: domix_m6_web    
      sorting_weight: 27  

  - platform: total_daily_energy
    name: "Total Daily Energy ${m6_channel_description} 7"
    power_id: ${m6_name}${m6_number_1}_power_7
    icon: "mdi:whatshot"
    filters:
        - multiply: 0.001
    unit_of_measurement: kWh
    accuracy_decimals: 3
    device_class: energy
    qos: 1
    retain: true
    state_topic: ${mqtt_name}/${m6_name}${m6_number_1}/${m6_channel_description} 7/Total Daily Energy/state
    web_server:
      sorting_group_id: domix_m6_web    
      sorting_weight: 28  

  - platform: total_daily_energy
    name: "Total Daily Energy ${m6_channel_description} 8"
    power_id: ${m6_name}${m6_number_1}_power_8
    icon: "mdi:whatshot"
    filters:
        - multiply: 0.001
    unit_of_measurement: kWh
    accuracy_decimals: 3
    device_class: energy
    qos: 1
    retain: true
    state_topic: ${mqtt_name}/${m6_name}${m6_number_1}/${m6_channel_description} 8/Total Daily Energy/state
    web_server:
      sorting_group_id: domix_m6_web   
      sorting_weight: 29   

  - platform: total_daily_energy
    name: "Total Daily Energy ${m6_channel_description} 9"
    power_id: ${m6_name}${m6_number_1}_power_9
    icon: "mdi:whatshot"
    filters:
        - multiply: 0.001
    unit_of_measurement: kWh
    accuracy_decimals: 3
    device_class: energy
    qos: 1
    retain: true
    state_topic: ${mqtt_name}/${m6_name}${m6_number_1}/${m6_channel_description} 9/Total Daily Energy/state
    web_server:
      sorting_group_id: domix_m6_web    
      sorting_weight: 30  

  - platform: total_daily_energy
    name: "Total Daily Energy ${m6_channel_description} 10"
    power_id: ${m6_name}${m6_number_1}_power_10
    icon: "mdi:whatshot"
    filters:
        - multiply: 0.001
    unit_of_measurement: kWh
    accuracy_decimals: 3
    device_class: energy
    qos: 1
    retain: true
    state_topic: ${mqtt_name}/${m6_name}${m6_number_1}/${m6_channel_description} 10/Total Daily Energy/state
    web_server:
      sorting_group_id: domix_m6_web    
      sorting_weight: 31  
